shsa5563/Ring-WearTech/Project_Updates/low_power_project_update_7.pdf

## LOW POWER EMBEDDED DESIGN PROJECT UPDATE #7

Team Name: WearTech

Team Mates:

Sanjana Kalyanappagol | Shekhar Satyanarayana
saka2821@colorado.edu | shsa5563@colorado.edu

## Executive Summary:

Part Selection
Battery | GMB401215-45mAh
PMU IC | LT1965
Processor | EFR32BG13– f1024
Inductive Charging IC | BQ5103B
Battery Charger IC | BQ24040
Sensor | BMA280

As discussed, our project requires 2 Blue Gecko dev kits to act as devices in the mesh network.

On Schedule: Yes

Accomplishments:
- We have completed 100% of the schematics.
- Half way through the Layouts.
- Got the schematics reviewed
- Worked on the ESD diode

Next week:
- get second review on schematics
- Complete the Layouts
- Start Firmware Development
- Test Inductive charging
