shsa5563/Ring-WearTech/Final Report/gantchart_final.xlsx

 |  |  |  |  |  |  |  |  |  |  |  |  |  |  |  |  |  |  |  |  |  |  |  |  |  |  |  |  |  |  |  |  |  |  |  |  |  |  |  |  |  |  |  |  |  |  |  |  |  |  |  |  |  |  |  | PCB released to fab
Project Planner
 |  |  |  |  |  |  |  | Period Highlight: |  |  |  |  | 15 |  |  |  | Plan |  |  | Actual |  |  |  | % Complete |  |  |  |  | Actual (beyond plan) |  |  |  |  |  |  |  | % Complete (beyond plan)
 |  | PLAN | PLAN | ACTUAL | ACTUAL | PERCENT |  | August 28th |  |  |  | September 1st |  |  |  |  |  |  |  |  |  |  |  |  |  |  |  |  |  |  |  |  |  |  |  |  |  |  |  |  |  | October 1st
ACTIVITY |  | START | DURATION | START | DURATION | COMPLETE |  | PERIODS
 | Lead |  |  |  |  |  | Comments | 1 | 2 | 3 | 4 | 5 | 6 | 7 | 8 | 9 | 10 | 11 | 12 | 13 | 14 | 15 | 16 | 17 | 18 | 19 | 20 | 21 | 22 | 23 | 24 | 25 | 26 | 27 | 28 | 29 | 30 | 31 | 32 | 33 | 34 | 35 | 36 | 37 | 38 | 39 | 40 | 41 | 42 | 43 | 44 | 45 | 46 | 47 | 48 | 49 | 50 | 51
Search Project Idea | Sanjana & Shekhar | 1 | 7 | 6 | 3 | 100%
Project proposal | Sanjana & Shekhar | 7 | 2 | 8 | 2 | 100%
Search for Part Kits | Sanjana & Shekhar | 11 | 3 | 11 | 3 | 100%
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
