shsa5563/Ring-WearTech/Altium_Schematics_Layout/WearTechPCB/MajorICandDescription.xlsx

Project | Description
Ring-WearTech | A wearable device which recognises and acts on the alphabets/commands/gestures. The accelerometer helps in acquiring the information, which is relyed in realtime to the mobile Device through BLE. The intelligence to decode the information recevied and map to the appropriate defined gestures/commands is accomplished by the Mobile Device.
Major Ics | Description
BQ51013B | Used for Inductive charging from the Inductive coil and produces a current of 1.254A to 1.2A and voltage of 4.3V
BQ24040 | Used for LiPo battery Charging, takes the output from BQ51013B. It has an output Current of 1.2 to 1A and voltage at 4.3V
BMA280 | Accelerometer sensor IC, used to sense the accelerometer readings and double tap
EFR32BG | BLE/Bluetooth Mesh capable IC for accessing the BMA280 sensor and relying the information gained through BLE to the Mobile Device
LT1965 | And LDO for regulating the voltage to 2.5V
