shsa5563/Ring-WearTech/Project_Updates/PMU_Capacitance_Simulation_Assignment/LT1965_MultipleSink.asc

C1: cap; 10µ; Rser=5m
C2: cap; 10µ; Rser=5m
C4: cap; 0.3µ
I1: current; PULSE(0 2.487mA 0 1us 1us 5ms 133ms 4)
I2: current; PULSE(0 4.988mA 10ms 1us 1us 10ms 133ms 4)
I3: current; PULSE(0 4.988mA 23ms 1us 1us 40ms 133ms 4)
I4: current; PULSE(0 10.693mA 63ms 1us 1us 70ms 133ms 4)
R1: RES; 4.53K; tol=1 pwr=0.1
R2: res; 4.12K
R3: res; 18.79K
U1: LT1965
V1: VOLTAGE; 3.7; Rser=700m
Named nets: 0, OUT, IN
.tran 800ms startup
Note:
  If the simulation model is not found please update with the "Sync Release" command from the "Tools" menu.
  It remains the customer's responsibility to verify proper and reliable operation in the actual application.
  Component substitution and printed circuit board layout may significantly affect circuit performance or reliability.
  Contact your local sales representative for assistance. This circuit is distributed to customers only for use with LTC parts.
  Copyright © 2008 Linear Technology Inc. All rights reserved.
LT1965- 1.1A, Low Noise Low Dropout Linear Regulator
Input: 3.3V       Output: 2.5V@1.1A
