shsa5563/Ring-WearTech/Firmware/soc-smartPhone_NoBuff/inc/efr32bg13p532f512gm32.h

/**************************************************************************//**
 * @file efr32bg13p532f512gm32.h
 * @brief CMSIS Cortex-M Peripheral Access Layer Header File
 *        for EFR32BG13P532F512GM32
 * @version 5.3.2
 ******************************************************************************
 * # License
 * <b>Copyright 2017 Silicon Laboratories, Inc. http://www.silabs.com</b>
 ******************************************************************************
 *
 * Permission is granted to anyone to use this software for any purpose,
 * including commercial applications, and to alter it and redistribute it
 * freely, subject to the following restrictions:
 *
 * 1. The origin of this software must not be misrepresented; you must not
 *    claim that you wrote the original software.@n
 * 2. Altered source versions must be plainly marked as such, and must not be
 *    misrepresented as being the original software.@n
 * 3. This notice may not be removed or altered from any source distribution.
 *
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
 * Silicon Laboratories, Inc. will not be liable for any consequential,
 * incidental, or special damages, or any other relief, or for any claim by
 * any third party, arising from your use of this Software.
 *
 *****************************************************************************/

#if defined(__ICCARM__)
#pragma system_include       /* Treat file as system include file. */
#elif defined(__ARMCC_VERSION) && (__ARMCC_VERSION >= 6010050)
#pragma clang system_header  /* Treat file as system include file. */
#endif

#ifndef EFR32BG13P532F512GM32_H
#define EFR32BG13P532F512GM32_H

#ifdef __cplusplus
extern "C" {
#endif

/**************************************************************************//**
 * @addtogroup Parts
 * @{
 *****************************************************************************/

/**************************************************************************//**
 * @defgroup EFR32BG13P532F512GM32 EFR32BG13P532F512GM32
 * @{
 *****************************************************************************/

/** Interrupt Number Definition */
typedef enum IRQn{
/******  Cortex-M4 Processor Exceptions Numbers ********************************************/
  NonMaskableInt_IRQn   = -14,              /*!< 2  Cortex-M4 Non Maskable Interrupt      */
  HardFault_IRQn        = -13,              /*!< 3  Cortex-M4 Hard Fault Interrupt        */
  MemoryManagement_IRQn = -12,              /*!< 4  Cortex-M4 Memory Management Interrupt */
  BusFault_IRQn         = -11,              /*!< 5  Cortex-M4 Bus Fault Interrupt         */
  UsageFault_IRQn       = -10,              /*!< 6  Cortex-M4 Usage Fault Interrupt       */
  SVCall_IRQn           = -5,               /*!< 11 Cortex-M4 SV Call Interrupt           */
  DebugMonitor_IRQn     = -4,               /*!< 12 Cortex-M4 Debug Monitor Interrupt     */
  PendSV_IRQn           = -2,               /*!< 14 Cortex-M4 Pend SV Interrupt           */
  SysTick_IRQn          = -1,               /*!< 15 Cortex-M4 System Tick Interrupt       */

/******  EFR32BG13P Peripheral Interrupt Numbers ********************************************/

  EMU_IRQn              = 0,  /*!< 16+0 EFR32 EMU Interrupt */
  WDOG0_IRQn            = 2,  /*!< 16+2 EFR32 WDOG0 Interrupt */
  WDOG1_IRQn            = 3,  /*!< 16+3 EFR32 WDOG1 Interrupt */
  LDMA_IRQn             = 9,  /*!< 16+9 EFR32 LDMA Interrupt */
  GPIO_EVEN_IRQn        = 10, /*!< 16+10 EFR32 GPIO_EVEN Interrupt */
  TIMER0_IRQn           = 11, /*!< 16+11 EFR32 TIMER0 Interrupt */
  USART0_RX_IRQn        = 12, /*!< 16+12 EFR32 USART0_RX Interrupt */
  USART0_TX_IRQn        = 13, /*!< 16+13 EFR32 USART0_TX Interrupt */
  ACMP0_IRQn            = 14, /*!< 16+14 EFR32 ACMP0 Interrupt */
  ADC0_IRQn             = 15, /*!< 16+15 EFR32 ADC0 Interrupt */
  IDAC0_IRQn            = 16, /*!< 16+16 EFR32 IDAC0 Interrupt */
  I2C0_IRQn             = 17, /*!< 16+17 EFR32 I2C0 Interrupt */
  GPIO_ODD_IRQn         = 18, /*!< 16+18 EFR32 GPIO_ODD Interrupt */
  TIMER1_IRQn           = 19, /*!< 16+19 EFR32 TIMER1 Interrupt */
  USART1_RX_IRQn        = 20, /*!< 16+20 EFR32 USART1_RX Interrupt */
  USART1_TX_IRQn        = 21, /*!< 16+21 EFR32 USART1_TX Interrupt */
  LEUART0_IRQn          = 22, /*!< 16+22 EFR32 LEUART0 Interrupt */
  PCNT0_IRQn            = 23, /*!< 16+23 EFR32 PCNT0 Interrupt */
  CMU_IRQn              = 24, /*!< 16+24 EFR32 CMU Interrupt */
  MSC_IRQn              = 25, /*!< 16+25 EFR32 MSC Interrupt */
  CRYPTO0_IRQn          = 26, /*!< 16+26 EFR32 CRYPTO0 Interrupt */
  LETIMER0_IRQn         = 27, /*!< 16+27 EFR32 LETIMER0 Interrupt */
  RTCC_IRQn             = 31, /*!< 16+31 EFR32 RTCC Interrupt */
  CRYOTIMER_IRQn        = 33, /*!< 16+33 EFR32 CRYOTIMER Interrupt */
  FPUEH_IRQn            = 35, /*!< 16+35 EFR32 FPUEH Interrupt */
  SMU_IRQn              = 36, /*!< 16+36 EFR32 SMU Interrupt */
  WTIMER0_IRQn          = 37, /*!< 16+37 EFR32 WTIMER0 Interrupt */
  USART2_RX_IRQn        = 38, /*!< 16+38 EFR32 USART2_RX Interrupt */
  USART2_TX_IRQn        = 39, /*!< 16+39 EFR32 USART2_TX Interrupt */
  I2C1_IRQn             = 40, /*!< 16+40 EFR32 I2C1 Interrupt */
  VDAC0_IRQn            = 41, /*!< 16+41 EFR32 VDAC0 Interrupt */
  CSEN_IRQn             = 42, /*!< 16+42 EFR32 CSEN Interrupt */
  LESENSE_IRQn          = 43, /*!< 16+43 EFR32 LESENSE Interrupt */
  CRYPTO1_IRQn          = 44, /*!< 16+44 EFR32 CRYPTO1 Interrupt */
  TRNG0_IRQn            = 45, /*!< 16+45 EFR32 TRNG0 Interrupt */
} IRQn_Type;

#define CRYPTO_IRQn               CRYPTO0_IRQn /*!< Alias for CRYPTO0_IRQn */

/**************************************************************************//**
 * @defgroup EFR32BG13P532F512GM32_Core Core
 * @{
 * @brief Processor and Core Peripheral Section
 *****************************************************************************/
#define __MPU_PRESENT             1 /**< Presence of MPU  */
#define __FPU_PRESENT             1 /**< Presence of FPU  */
#define __VTOR_PRESENT            1 /**< Presence of VTOR register in SCB */
#define __NVIC_PRIO_BITS          3 /**< NVIC interrupt priority bits */
#define __Vendor_SysTickConfig    0 /**< Is 1 if different SysTick counter is used */

/** @} End of group EFR32BG13P532F512GM32_Core */

/**************************************************************************//**
* @defgroup EFR32BG13P532F512GM32_Part Part
* @{
******************************************************************************/

/** Part family */
#define _EFR32_BLUE_FAMILY                      1                               /**< BLUE Gecko RF SoC Family  */
#define _EFR_DEVICE                                                             /**< Silicon Labs EFR-type RF SoC */
#define _SILICON_LABS_32B_SERIES_1                                              /**< Silicon Labs series number */
#define _SILICON_LABS_32B_SERIES                1                               /**< Silicon Labs series number */
#define _SILICON_LABS_32B_SERIES_1_CONFIG_3                                     /**< Series 1, Configuration 3 */
#define _SILICON_LABS_32B_SERIES_1_CONFIG       3                               /**< Series 1, Configuration 3 */
#define _SILICON_LABS_GECKO_INTERNAL_SDID       89                              /**< Silicon Labs internal use only, may change any time */
#define _SILICON_LABS_GECKO_INTERNAL_SDID_89                                    /**< Silicon Labs internal use only, may change any time */
#define _SILICON_LABS_EFR32_RADIO_SUBGHZ        1                               /**< Radio supports Sub-GHz */
#define _SILICON_LABS_EFR32_RADIO_2G4HZ         2                               /**< Radio supports 2.4 GHz */
#define _SILICON_LABS_EFR32_RADIO_DUALBAND      3                               /**< Radio supports dual band */
#define _SILICON_LABS_EFR32_RADIO_TYPE          _SILICON_LABS_EFR32_RADIO_2G4HZ /**< Radio type */
#define _SILICON_LABS_32B_PLATFORM_2                                            /**< @deprecated Silicon Labs platform name */
#define _SILICON_LABS_32B_PLATFORM              2                               /**< @deprecated Silicon Labs platform name */
#define _SILICON_LABS_32B_PLATFORM_2_GEN_3                                      /**< @deprecated Platform 2, generation 3 */
#define _SILICON_LABS_32B_PLATFORM_2_GEN        3                               /**< @deprecated Platform 2, generation 3 */

/* If part number is not defined as compiler option, define it */
#if !defined(EFR32BG13P532F512GM32)
#define EFR32BG13P532F512GM32    1 /**< BLUE Gecko Part */
#endif

/** Configure part number */
#define PART_NUMBER                "EFR32BG13P532F512GM32" /**< Part Number */

/** Memory Base addresses and limits */
#define RAM0_CODE_MEM_BASE         ((uint32_t) 0x10000000UL) /**< RAM0_CODE base address  */
#define RAM0_CODE_MEM_SIZE         ((uint32_t) 0x8000UL)     /**< RAM0_CODE available address space  */
#define RAM0_CODE_MEM_END          ((uint32_t) 0x10007FFFUL) /**< RAM0_CODE end address  */
#define RAM0_CODE_MEM_BITS         ((uint32_t) 0x0000000FUL) /**< RAM0_CODE used bits  */
#define RAM2_MEM_BASE              ((uint32_t) 0x20010000UL) /**< RAM2 base address  */
#define RAM2_MEM_SIZE              ((uint32_t) 0x800UL)      /**< RAM2 available address space  */
#define RAM2_MEM_END               ((uint32_t) 0x200107FFUL) /**< RAM2 end address  */
#define RAM2_MEM_BITS              ((uint32_t) 0x0000000BUL) /**< RAM2 used bits  */
#define RAM1_MEM_BASE              ((uint32_t) 0x20008000UL) /**< RAM1 base address  */
#define RAM1_MEM_SIZE              ((uint32_t) 0x8000UL)     /**< RAM1 available address space  */
#define RAM1_MEM_END               ((uint32_t) 0x2000FFFFUL) /**< RAM1 end address  */
#define RAM1_MEM_BITS              ((uint32_t) 0x0000000FUL) /**< RAM1 used bits  */
#define CRYPTO1_BITCLR_MEM_BASE    ((uint32_t) 0x440F0400UL) /**< CRYPTO1_BITCLR base address  */
#define CRYPTO1_BITCLR_MEM_SIZE    ((uint32_t) 0x400UL)      /**< CRYPTO1_BITCLR available address space  */
#define CRYPTO1_BITCLR_MEM_END     ((uint32_t) 0x440F07FFUL) /**< CRYPTO1_BITCLR end address  */
#define CRYPTO1_BITCLR_MEM_BITS    ((uint32_t) 0x0000000AUL) /**< CRYPTO1_BITCLR used bits  */
#define PER_MEM_BASE               ((uint32_t) 0x40000000UL) /**< PER base address  */
#define PER_MEM_SIZE               ((uint32_t) 0xF0000UL)    /**< PER available address space  */
#define PER_MEM_END                ((uint32_t) 0x400EFFFFUL) /**< PER end address  */
#define PER_MEM_BITS               ((uint32_t) 0x00000014UL) /**< PER used bits  */
#define RAM1_CODE_MEM_BASE         ((uint32_t) 0x10008000UL) /**< RAM1_CODE base address  */
#define RAM1_CODE_MEM_SIZE         ((uint32_t) 0x8000UL)     /**< RAM1_CODE available address space  */
#define RAM1_CODE_MEM_END          ((uint32_t) 0x1000FFFFUL) /**< RAM1_CODE end address  */
#define RAM1_CODE_MEM_BITS         ((uint32_t) 0x0000000FUL) /**< RAM1_CODE used bits  */
#define CRYPTO1_MEM_BASE           ((uint32_t) 0x400F0400UL) /**< CRYPTO1 base address  */
#define CRYPTO1_MEM_SIZE           ((uint32_t) 0x400UL)      /**< CRYPTO1 available address space  */
#define CRYPTO1_MEM_END            ((uint32_t) 0x400F07FFUL) /**< CRYPTO1 end address  */
#define CRYPTO1_MEM_BITS           ((uint32_t) 0x0000000AUL) /**< CRYPTO1 used bits  */
#define FLASH_MEM_BASE             ((uint32_t) 0x00000000UL) /**< FLASH base address  */
#define FLASH_MEM_SIZE             ((uint32_t) 0x10000000UL) /**< FLASH available address space  */
#define FLASH_MEM_END              ((uint32_t) 0x0FFFFFFFUL) /**< FLASH end address  */
#define FLASH_MEM_BITS             ((uint32_t) 0x0000001CUL) /**< FLASH used bits  */
#define CRYPTO0_MEM_BASE           ((uint32_t) 0x400F0000UL) /**< CRYPTO0 base address  */
#define CRYPTO0_MEM_SIZE           ((uint32_t) 0x400UL)      /**< CRYPTO0 available address space  */
#define CRYPTO0_MEM_END            ((uint32_t) 0x400F03FFUL) /**< CRYPTO0 end address  */
#define CRYPTO0_MEM_BITS           ((uint32_t) 0x0000000AUL) /**< CRYPTO0 used bits  */
#define CRYPTO_MEM_BASE            CRYPTO0_MEM_BASE          /**< Alias for CRYPTO0_MEM_BASE */
#define CRYPTO_MEM_SIZE            CRYPTO0_MEM_SIZE          /**< Alias for CRYPTO0_MEM_SIZE */
#define CRYPTO_MEM_END             CRYPTO0_MEM_END           /**< Alias for CRYPTO0_MEM_END  */
#define CRYPTO_MEM_BITS            CRYPTO0_MEM_BITS          /**< Alias for CRYPTO0_MEM_BITS */
#define PER_BITCLR_MEM_BASE        ((uint32_t) 0x44000000UL) /**< PER_BITCLR base address  */
#define PER_BITCLR_MEM_SIZE        ((uint32_t) 0xF0000UL)    /**< PER_BITCLR available address space  */
#define PER_BITCLR_MEM_END         ((uint32_t) 0x440EFFFFUL) /**< PER_BITCLR end address  */
#define PER_BITCLR_MEM_BITS        ((uint32_t) 0x00000014UL) /**< PER_BITCLR used bits  */
#define CRYPTO0_BITSET_MEM_BASE    ((uint32_t) 0x460F0000UL) /**< CRYPTO0_BITSET base address  */
#define CRYPTO0_BITSET_MEM_SIZE    ((uint32_t) 0x400UL)      /**< CRYPTO0_BITSET available address space  */
#define CRYPTO0_BITSET_MEM_END     ((uint32_t) 0x460F03FFUL) /**< CRYPTO0_BITSET end address  */
#define CRYPTO0_BITSET_MEM_BITS    ((uint32_t) 0x0000000AUL) /**< CRYPTO0_BITSET used bits  */
#define CRYPTO_BITSET_MEM_BASE     CRYPTO0_BITSET_MEM_BASE   /**< Alias for CRYPTO0_BITSET_MEM_BASE */
#define CRYPTO_BITSET_MEM_SIZE     CRYPTO0_BITSET_MEM_SIZE   /**< Alias for CRYPTO0_BITSET_MEM_SIZE */
#define CRYPTO_BITSET_MEM_END      CRYPTO0_BITSET_MEM_END    /**< Alias for CRYPTO0_BITSET_MEM_END  */
#define CRYPTO_BITSET_MEM_BITS     CRYPTO0_BITSET_MEM_BITS   /**< Alias for CRYPTO0_BITSET_MEM_BITS */
#define CRYPTO0_BITCLR_MEM_BASE    ((uint32_t) 0x440F0000UL) /**< CRYPTO0_BITCLR base address  */
#define CRYPTO0_BITCLR_MEM_SIZE    ((uint32_t) 0x400UL)      /**< CRYPTO0_BITCLR available address space  */
#define CRYPTO0_BITCLR_MEM_END     ((uint32_t) 0x440F03FFUL) /**< CRYPTO0_BITCLR end address  */
#define CRYPTO0_BITCLR_MEM_BITS    ((uint32_t) 0x0000000AUL) /**< CRYPTO0_BITCLR used bits  */
#define CRYPTO_BITCLR_MEM_BASE     CRYPTO0_BITCLR_MEM_BASE   /**< Alias for CRYPTO0_BITCLR_MEM_BASE */
#define CRYPTO_BITCLR_MEM_SIZE     CRYPTO0_BITCLR_MEM_SIZE   /**< Alias for CRYPTO0_BITCLR_MEM_SIZE */
#define CRYPTO_BITCLR_MEM_END      CRYPTO0_BITCLR_MEM_END    /**< Alias for CRYPTO0_BITCLR_MEM_END  */
#define CRYPTO_BITCLR_MEM_BITS     CRYPTO0_BITCLR_MEM_BITS   /**< Alias for CRYPTO0_BITCLR_MEM_BITS */
#define PER_BITSET_MEM_BASE        ((uint32_t) 0x46000000UL) /**< PER_BITSET base address  */
#define PER_BITSET_MEM_SIZE        ((uint32_t) 0xF0000UL)    /**< PER_BITSET available address space  */
#define PER_BITSET_MEM_END         ((uint32_t) 0x460EFFFFUL) /**< PER_BITSET end address  */
#define PER_BITSET_MEM_BITS        ((uint32_t) 0x00000014UL) /**< PER_BITSET used bits  */
#define CRYPTO1_BITSET_MEM_BASE    ((uint32_t) 0x460F0400UL) /**< CRYPTO1_BITSET base address  */
#define CRYPTO1_BITSET_MEM_SIZE    ((uint32_t) 0x400UL)      /**< CRYPTO1_BITSET available address space  */
#define CRYPTO1_BITSET_MEM_END     ((uint32_t) 0x460F07FFUL) /**< CRYPTO1_BITSET end address  */
#define CRYPTO1_BITSET_MEM_BITS    ((uint32_t) 0x0000000AUL) /**< CRYPTO1_BITSET used bits  */
#define RAM2_CODE_MEM_BASE         ((uint32_t) 0x10010000UL) /**< RAM2_CODE base address  */
#define RAM2_CODE_MEM_SIZE         ((uint32_t) 0x800UL)      /**< RAM2_CODE available address space  */
#define RAM2_CODE_MEM_END          ((uint32_t) 0x100107FFUL) /**< RAM2_CODE end address  */
#define RAM2_CODE_MEM_BITS         ((uint32_t) 0x0000000BUL) /**< RAM2_CODE used bits  */
#define RAM_MEM_BASE               ((uint32_t) 0x20000000UL) /**< RAM base address  */
#define RAM_MEM_SIZE               ((uint32_t) 0x8000UL)     /**< RAM available address space  */
#define RAM_MEM_END                ((uint32_t) 0x20007FFFUL) /**< RAM end address  */
#define RAM_MEM_BITS               ((uint32_t) 0x0000000FUL) /**< RAM used bits  */

/** Bit banding area */
#define BITBAND_PER_BASE           ((uint32_t) 0x42000000UL) /**< Peripheral Address Space bit-band area */
#define BITBAND_RAM_BASE           ((uint32_t) 0x22000000UL) /**< SRAM Address Space bit-band area */

/** Flash and SRAM limits for EFR32BG13P532F512GM32 */
#define FLASH_BASE                 (0x00000000UL) /**< Flash Base Address */
#define FLASH_SIZE                 (0x00080000UL) /**< Available Flash Memory */
#define FLASH_PAGE_SIZE            2048U          /**< Flash Memory page size */
#define SRAM_BASE                  (0x20000000UL) /**< SRAM Base Address */
#define SRAM_SIZE                  (0x00010000UL) /**< Available SRAM Memory */
#define __CM4_REV                  0x001          /**< Cortex-M4 Core revision r0p1 */
#define PRS_CHAN_COUNT             12             /**< Number of PRS channels */
#define DMA_CHAN_COUNT             8              /**< Number of DMA channels */
#define EXT_IRQ_COUNT              47             /**< Number of External (NVIC) interrupts */

/** AF channels connect the different on-chip peripherals with the af-mux */
#define AFCHAN_MAX                 118
/** AF channel maximum location number */
#define AFCHANLOC_MAX              32
/** Analog AF channels */
#define AFACHAN_MAX                118

/* Part number capabilities */

#define CRYPTO_PRESENT          /**< CRYPTO is available in this part */
#define CRYPTO_COUNT          2 /**< 2 CRYPTOs available  */
#define TIMER_PRESENT           /**< TIMER is available in this part */
#define TIMER_COUNT           2 /**< 2 TIMERs available  */
#define WTIMER_PRESENT          /**< WTIMER is available in this part */
#define WTIMER_COUNT          1 /**< 1 WTIMERs available  */
#define USART_PRESENT           /**< USART is available in this part */
#define USART_COUNT           3 /**< 3 USARTs available  */
#define LEUART_PRESENT          /**< LEUART is available in this part */
#define LEUART_COUNT          1 /**< 1 LEUARTs available  */
#define LETIMER_PRESENT         /**< LETIMER is available in this part */
#define LETIMER_COUNT         1 /**< 1 LETIMERs available  */
#define PCNT_PRESENT            /**< PCNT is available in this part */
#define PCNT_COUNT            1 /**< 1 PCNTs available  */
#define I2C_PRESENT             /**< I2C is available in this part */
#define I2C_COUNT             2 /**< 2 I2Cs available  */
#define ADC_PRESENT             /**< ADC is available in this part */
#define ADC_COUNT             1 /**< 1 ADCs available  */
#define ACMP_PRESENT            /**< ACMP is available in this part */
#define ACMP_COUNT            2 /**< 2 ACMPs available  */
#define VDAC_PRESENT            /**< VDAC is available in this part */
#define VDAC_COUNT            1 /**< 1 VDACs available  */
#define WDOG_PRESENT            /**< WDOG is available in this part */
#define WDOG_COUNT            2 /**< 2 WDOGs available  */
#define IDAC_PRESENT            /**< IDAC is available in this part */
#define IDAC_COUNT            1 /**< 1 IDACs available  */
#define TRNG_PRESENT            /**< TRNG is available in this part */
#define TRNG_COUNT            1 /**< 1 TRNGs available  */
#define MSC_PRESENT             /**< MSC is available in this part */
#define MSC_COUNT             1 /**< 1 MSC available */
#define EMU_PRESENT             /**< EMU is available in this part */
#define EMU_COUNT             1 /**< 1 EMU available */
#define RMU_PRESENT             /**< RMU is available in this part */
#define RMU_COUNT             1 /**< 1 RMU available */
#define CMU_PRESENT             /**< CMU is available in this part */
#define CMU_COUNT             1 /**< 1 CMU available */
#define GPIO_PRESENT            /**< GPIO is available in this part */
#define GPIO_COUNT            1 /**< 1 GPIO available */
#define PRS_PRESENT             /**< PRS is available in this part */
#define PRS_COUNT             1 /**< 1 PRS available */
#define LDMA_PRESENT            /**< LDMA is available in this part */
#define LDMA_COUNT            1 /**< 1 LDMA available */
#define FPUEH_PRESENT           /**< FPUEH is available in this part */
#define FPUEH_COUNT           1 /**< 1 FPUEH available */
#define GPCRC_PRESENT           /**< GPCRC is available in this part */
#define GPCRC_COUNT           1 /**< 1 GPCRC available */
#define CRYOTIMER_PRESENT       /**< CRYOTIMER is available in this part */
#define CRYOTIMER_COUNT       1 /**< 1 CRYOTIMER available */
#define CSEN_PRESENT            /**< CSEN is available in this part */
#define CSEN_COUNT            1 /**< 1 CSEN available */
#define LESENSE_PRESENT         /**< LESENSE is available in this part */
#define LESENSE_COUNT         1 /**< 1 LESENSE available */
#define RTCC_PRESENT            /**< RTCC is available in this part */
#define RTCC_COUNT            1 /**< 1 RTCC available */
#define ETM_PRESENT             /**< ETM is available in this part */
#define ETM_COUNT             1 /**< 1 ETM available */
#define BOOTLOADER_PRESENT      /**< BOOTLOADER is available in this part */
#define BOOTLOADER_COUNT      1 /**< 1 BOOTLOADER available */
#define SMU_PRESENT             /**< SMU is available in this part */
#define SMU_COUNT             1 /**< 1 SMU available */
#define DCDC_PRESENT            /**< DCDC is available in this part */
#define DCDC_COUNT            1 /**< 1 DCDC available */

#include "core_cm4.h"           /* Cortex-M4 processor and core peripherals */
#include "system_efr32bg13p.h"  /* System Header File */

/** @} End of group EFR32BG13P532F512GM32_Part */

/**************************************************************************//**
 * @defgroup EFR32BG13P532F512GM32_Peripheral_TypeDefs Peripheral TypeDefs
 * @{
 * @brief Device Specific Peripheral Register Structures
 *****************************************************************************/

#include "efr32bg13p_msc.h"
#include "efr32bg13p_emu.h"
#include "efr32bg13p_rmu.h"
#include "efr32bg13p_cmu.h"
#include "efr32bg13p_crypto.h"
#include "efr32bg13p_gpio_p.h"
#include "efr32bg13p_gpio.h"
#include "efr32bg13p_prs_ch.h"
#include "efr32bg13p_prs.h"
#include "efr32bg13p_ldma_ch.h"
#include "efr32bg13p_ldma.h"
#include "efr32bg13p_fpueh.h"
#include "efr32bg13p_gpcrc.h"
#include "efr32bg13p_timer_cc.h"
#include "efr32bg13p_timer.h"
#include "efr32bg13p_usart.h"
#include "efr32bg13p_leuart.h"
#include "efr32bg13p_letimer.h"
#include "efr32bg13p_cryotimer.h"
#include "efr32bg13p_pcnt.h"
#include "efr32bg13p_i2c.h"
#include "efr32bg13p_adc.h"
#include "efr32bg13p_acmp.h"
#include "efr32bg13p_vdac_opa.h"
#include "efr32bg13p_vdac.h"
#include "efr32bg13p_csen.h"
#include "efr32bg13p_lesense_st.h"
#include "efr32bg13p_lesense_buf.h"
#include "efr32bg13p_lesense_ch.h"
#include "efr32bg13p_lesense.h"
#include "efr32bg13p_rtcc_cc.h"
#include "efr32bg13p_rtcc_ret.h"
#include "efr32bg13p_rtcc.h"
#include "efr32bg13p_wdog_pch.h"
#include "efr32bg13p_wdog.h"
#include "efr32bg13p_etm.h"
#include "efr32bg13p_idac.h"
#include "efr32bg13p_smu.h"
#include "efr32bg13p_trng.h"
#include "efr32bg13p_dma_descriptor.h"
#include "efr32bg13p_devinfo.h"
#include "efr32bg13p_romtable.h"

/** @} End of group EFR32BG13P532F512GM32_Peripheral_TypeDefs  */

/**************************************************************************//**
 * @defgroup EFR32BG13P532F512GM32_Peripheral_Base Peripheral Memory Map
 * @{
 *****************************************************************************/

#define MSC_BASE          (0x400E0000UL) /**< MSC base address  */
#define EMU_BASE          (0x400E3000UL) /**< EMU base address  */
#define RMU_BASE          (0x400E5000UL) /**< RMU base address  */
#define CMU_BASE          (0x400E4000UL) /**< CMU base address  */
#define CRYPTO0_BASE      (0x400F0000UL) /**< CRYPTO0 base address  */
#define CRYPTO_BASE       CRYPTO0_BASE   /**< Alias for CRYPTO0 base address */
#define CRYPTO1_BASE      (0x400F0400UL) /**< CRYPTO1 base address  */
#define GPIO_BASE         (0x4000A000UL) /**< GPIO base address  */
#define PRS_BASE          (0x400E6000UL) /**< PRS base address  */
#define LDMA_BASE         (0x400E2000UL) /**< LDMA base address  */
#define FPUEH_BASE        (0x400E1000UL) /**< FPUEH base address  */
#define GPCRC_BASE        (0x4001C000UL) /**< GPCRC base address  */
#define TIMER0_BASE       (0x40018000UL) /**< TIMER0 base address  */
#define TIMER1_BASE       (0x40018400UL) /**< TIMER1 base address  */
#define WTIMER0_BASE      (0x4001A000UL) /**< WTIMER0 base address  */
#define USART0_BASE       (0x40010000UL) /**< USART0 base address  */
#define USART1_BASE       (0x40010400UL) /**< USART1 base address  */
#define USART2_BASE       (0x40010800UL) /**< USART2 base address  */
#define LEUART0_BASE      (0x4004A000UL) /**< LEUART0 base address  */
#define LETIMER0_BASE     (0x40046000UL) /**< LETIMER0 base address  */
#define CRYOTIMER_BASE    (0x4001E000UL) /**< CRYOTIMER base address  */
#define PCNT0_BASE        (0x4004E000UL) /**< PCNT0 base address  */
#define I2C0_BASE         (0x4000C000UL) /**< I2C0 base address  */
#define I2C1_BASE         (0x4000C400UL) /**< I2C1 base address  */
#define ADC0_BASE         (0x40002000UL) /**< ADC0 base address  */
#define ACMP0_BASE        (0x40000000UL) /**< ACMP0 base address  */
#define ACMP1_BASE        (0x40000400UL) /**< ACMP1 base address  */
#define VDAC0_BASE        (0x40008000UL) /**< VDAC0 base address  */
#define CSEN_BASE         (0x4001F000UL) /**< CSEN base address  */
#define LESENSE_BASE      (0x40055000UL) /**< LESENSE base address  */
#define RTCC_BASE         (0x40042000UL) /**< RTCC base address  */
#define WDOG0_BASE        (0x40052000UL) /**< WDOG0 base address  */
#define WDOG1_BASE        (0x40052400UL) /**< WDOG1 base address  */
#define ETM_BASE          (0xE0041000UL) /**< ETM base address  */
#define IDAC0_BASE        (0x40006000UL) /**< IDAC0 base address  */
#define SMU_BASE          (0x40022000UL) /**< SMU base address  */
#define TRNG0_BASE        (0x4001D000UL) /**< TRNG0 base address  */
#define DEVINFO_BASE      (0x0FE081B0UL) /**< DEVINFO base address */
#define ROMTABLE_BASE     (0xE00FFFD0UL) /**< ROMTABLE base address */
#define LOCKBITS_BASE     (0x0FE04000UL) /**< Lock-bits page base address */
#define USERDATA_BASE     (0x0FE00000UL) /**< User data page base address */

/** @} End of group EFR32BG13P532F512GM32_Peripheral_Base */

/**************************************************************************//**
 * @defgroup EFR32BG13P532F512GM32_Peripheral_Declaration Peripheral Declarations
 * @{
 *****************************************************************************/

#define MSC          ((MSC_TypeDef *) MSC_BASE)             /**< MSC base pointer */
#define EMU          ((EMU_TypeDef *) EMU_BASE)             /**< EMU base pointer */
#define RMU          ((RMU_TypeDef *) RMU_BASE)             /**< RMU base pointer */
#define CMU          ((CMU_TypeDef *) CMU_BASE)             /**< CMU base pointer */
#define CRYPTO0      ((CRYPTO_TypeDef *) CRYPTO0_BASE)      /**< CRYPTO0 base pointer */
#define CRYPTO       CRYPTO0                                /**< Alias for CRYPTO0 base pointer */
#define CRYPTO1      ((CRYPTO_TypeDef *) CRYPTO1_BASE)      /**< CRYPTO1 base pointer */
#define GPIO         ((GPIO_TypeDef *) GPIO_BASE)           /**< GPIO base pointer */
#define PRS          ((PRS_TypeDef *) PRS_BASE)             /**< PRS base pointer */
#define LDMA         ((LDMA_TypeDef *) LDMA_BASE)           /**< LDMA base pointer */
#define FPUEH        ((FPUEH_TypeDef *) FPUEH_BASE)         /**< FPUEH base pointer */
#define GPCRC        ((GPCRC_TypeDef *) GPCRC_BASE)         /**< GPCRC base pointer */
#define TIMER0       ((TIMER_TypeDef *) TIMER0_BASE)        /**< TIMER0 base pointer */
#define TIMER1       ((TIMER_TypeDef *) TIMER1_BASE)        /**< TIMER1 base pointer */
#define WTIMER0      ((TIMER_TypeDef *) WTIMER0_BASE)       /**< WTIMER0 base pointer */
#define USART0       ((USART_TypeDef *) USART0_BASE)        /**< USART0 base pointer */
#define USART1       ((USART_TypeDef *) USART1_BASE)        /**< USART1 base pointer */
#define USART2       ((USART_TypeDef *) USART2_BASE)        /**< USART2 base pointer */
#define LEUART0      ((LEUART_TypeDef *) LEUART0_BASE)      /**< LEUART0 base pointer */
#define LETIMER0     ((LETIMER_TypeDef *) LETIMER0_BASE)    /**< LETIMER0 base pointer */
#define CRYOTIMER    ((CRYOTIMER_TypeDef *) CRYOTIMER_BASE) /**< CRYOTIMER base pointer */
#define PCNT0        ((PCNT_TypeDef *) PCNT0_BASE)          /**< PCNT0 base pointer */
#define I2C0         ((I2C_TypeDef *) I2C0_BASE)            /**< I2C0 base pointer */
#define I2C1         ((I2C_TypeDef *) I2C1_BASE)            /**< I2C1 base pointer */
#define ADC0         ((ADC_TypeDef *) ADC0_BASE)            /**< ADC0 base pointer */
#define ACMP0        ((ACMP_TypeDef *) ACMP0_BASE)          /**< ACMP0 base pointer */
#define ACMP1        ((ACMP_TypeDef *) ACMP1_BASE)          /**< ACMP1 base pointer */
#define VDAC0        ((VDAC_TypeDef *) VDAC0_BASE)          /**< VDAC0 base pointer */
#define CSEN         ((CSEN_TypeDef *) CSEN_BASE)           /**< CSEN base pointer */
#define LESENSE      ((LESENSE_TypeDef *) LESENSE_BASE)     /**< LESENSE base pointer */
#define RTCC         ((RTCC_TypeDef *) RTCC_BASE)           /**< RTCC base pointer */
#define WDOG0        ((WDOG_TypeDef *) WDOG0_BASE)          /**< WDOG0 base pointer */
#define WDOG1        ((WDOG_TypeDef *) WDOG1_BASE)          /**< WDOG1 base pointer */
#define ETM          ((ETM_TypeDef *) ETM_BASE)             /**< ETM base pointer */
#define IDAC0        ((IDAC_TypeDef *) IDAC0_BASE)          /**< IDAC0 base pointer */
#define SMU          ((SMU_TypeDef *) SMU_BASE)             /**< SMU base pointer */
#define TRNG0        ((TRNG_TypeDef *) TRNG0_BASE)          /**< TRNG0 base pointer */
#define DEVINFO      ((DEVINFO_TypeDef *) DEVINFO_BASE)     /**< DEVINFO base pointer */
#define ROMTABLE     ((ROMTABLE_TypeDef *) ROMTABLE_BASE)   /**< ROMTABLE base pointer */

/** @} End of group EFR32BG13P532F512GM32_Peripheral_Declaration */

/**************************************************************************//**
 * @defgroup EFR32BG13P532F512GM32_Peripheral_Offsets Peripheral Offsets
 * @{
 *****************************************************************************/

#define CRYPTO_OFFSET     0x400 /**< Offset in bytes between CRYPTO instances */
#define TIMER_OFFSET      0x400 /**< Offset in bytes between TIMER instances */
#define WTIMER_OFFSET     0x400 /**< Offset in bytes between WTIMER instances */
#define USART_OFFSET      0x400 /**< Offset in bytes between USART instances */
#define LEUART_OFFSET     0x400 /**< Offset in bytes between LEUART instances */
#define LETIMER_OFFSET    0x400 /**< Offset in bytes between LETIMER instances */
#define PCNT_OFFSET       0x400 /**< Offset in bytes between PCNT instances */
#define I2C_OFFSET        0x400 /**< Offset in bytes between I2C instances */
#define ADC_OFFSET        0x400 /**< Offset in bytes between ADC instances */
#define ACMP_OFFSET       0x400 /**< Offset in bytes between ACMP instances */
#define VDAC_OFFSET       0x400 /**< Offset in bytes between VDAC instances */
#define WDOG_OFFSET       0x400 /**< Offset in bytes between WDOG instances */
#define IDAC_OFFSET       0x400 /**< Offset in bytes between IDAC instances */
#define TRNG_OFFSET       0x400 /**< Offset in bytes between TRNG instances */

/** @} End of group EFR32BG13P532F512GM32_Peripheral_Offsets */

/**************************************************************************//**
 * @defgroup EFR32BG13P532F512GM32_BitFields Bit Fields
 * @{
 *****************************************************************************/

#include "efr32bg13p_prs_signals.h"
#include "efr32bg13p_dmareq.h"

/**************************************************************************//**
 * @addtogroup EFR32BG13P532F512GM32_WTIMER
 * @{
 * @defgroup EFR32BG13P532F512GM32_WTIMER_BitFields  WTIMER Bit Fields
 * @{
 *****************************************************************************/

/* Bit fields for WTIMER CTRL */
#define _WTIMER_CTRL_RESETVALUE                     0x00000000UL                              /**< Default value for WTIMER_CTRL */
#define _WTIMER_CTRL_MASK                           0x3F036FFBUL                              /**< Mask for WTIMER_CTRL */
#define _WTIMER_CTRL_MODE_SHIFT                     0                                         /**< Shift value for TIMER_MODE */
#define _WTIMER_CTRL_MODE_MASK                      0x3UL                                     /**< Bit mask for TIMER_MODE */
#define _WTIMER_CTRL_MODE_DEFAULT                   0x00000000UL                              /**< Mode DEFAULT for WTIMER_CTRL */
#define _WTIMER_CTRL_MODE_UP                        0x00000000UL                              /**< Mode UP for WTIMER_CTRL */
#define _WTIMER_CTRL_MODE_DOWN                      0x00000001UL                              /**< Mode DOWN for WTIMER_CTRL */
#define _WTIMER_CTRL_MODE_UPDOWN                    0x00000002UL                              /**< Mode UPDOWN for WTIMER_CTRL */
#define _WTIMER_CTRL_MODE_QDEC                      0x00000003UL                              /**< Mode QDEC for WTIMER_CTRL */
#define WTIMER_CTRL_MODE_DEFAULT                    (_WTIMER_CTRL_MODE_DEFAULT << 0)          /**< Shifted mode DEFAULT for WTIMER_CTRL */
#define WTIMER_CTRL_MODE_UP                         (_WTIMER_CTRL_MODE_UP << 0)               /**< Shifted mode UP for WTIMER_CTRL */
#define WTIMER_CTRL_MODE_DOWN                       (_WTIMER_CTRL_MODE_DOWN << 0)             /**< Shifted mode DOWN for WTIMER_CTRL */
#define WTIMER_CTRL_MODE_UPDOWN                     (_WTIMER_CTRL_MODE_UPDOWN << 0)           /**< Shifted mode UPDOWN for WTIMER_CTRL */
#define WTIMER_CTRL_MODE_QDEC                       (_WTIMER_CTRL_MODE_QDEC << 0)             /**< Shifted mode QDEC for WTIMER_CTRL */
#define WTIMER_CTRL_SYNC                            (0x1UL << 3)                              /**< Timer Start/Stop/Reload Synchronization */
#define _WTIMER_CTRL_SYNC_SHIFT                     3                                         /**< Shift value for TIMER_SYNC */
#define _WTIMER_CTRL_SYNC_MASK                      0x8UL                                     /**< Bit mask for TIMER_SYNC */
#define _WTIMER_CTRL_SYNC_DEFAULT                   0x00000000UL                              /**< Mode DEFAULT for WTIMER_CTRL */
#define WTIMER_CTRL_SYNC_DEFAULT                    (_WTIMER_CTRL_SYNC_DEFAULT << 3)          /**< Shifted mode DEFAULT for WTIMER_CTRL */
#define WTIMER_CTRL_OSMEN                           (0x1UL << 4)                              /**< One-shot Mode Enable */
#define _WTIMER_CTRL_OSMEN_SHIFT                    4                                         /**< Shift value for TIMER_OSMEN */
#define _WTIMER_CTRL_OSMEN_MASK                     0x10UL                                    /**< Bit mask for TIMER_OSMEN */
#define _WTIMER_CTRL_OSMEN_DEFAULT                  0x00000000UL                              /**< Mode DEFAULT for WTIMER_CTRL */
#define WTIMER_CTRL_OSMEN_DEFAULT                   (_WTIMER_CTRL_OSMEN_DEFAULT << 4)         /**< Shifted mode DEFAULT for WTIMER_CTRL */
#define WTIMER_CTRL_QDM                             (0x1UL << 5)                              /**< Quadrature Decoder Mode Selection */
#define _WTIMER_CTRL_QDM_SHIFT                      5                                         /**< Shift value for TIMER_QDM */
#define _WTIMER_CTRL_QDM_MASK                       0x20UL                                    /**< Bit mask for TIMER_QDM */
#define _WTIMER_CTRL_QDM_DEFAULT                    0x00000000UL                              /**< Mode DEFAULT for WTIMER_CTRL */
#define _WTIMER_CTRL_QDM_X2                         0x00000000UL                              /**< Mode X2 for WTIMER_CTRL */
#define _WTIMER_CTRL_QDM_X4                         0x00000001UL                              /**< Mode X4 for WTIMER_CTRL */
#define WTIMER_CTRL_QDM_DEFAULT                     (_WTIMER_CTRL_QDM_DEFAULT << 5)           /**< Shifted mode DEFAULT for WTIMER_CTRL */
#define WTIMER_CTRL_QDM_X2                          (_WTIMER_CTRL_QDM_X2 << 5)                /**< Shifted mode X2 for WTIMER_CTRL */
#define WTIMER_CTRL_QDM_X4                          (_WTIMER_CTRL_QDM_X4 << 5)                /**< Shifted mode X4 for WTIMER_CTRL */
#define WTIMER_CTRL_DEBUGRUN                        (0x1UL << 6)                              /**< Debug Mode Run Enable */
#define _WTIMER_CTRL_DEBUGRUN_SHIFT                 6                                         /**< Shift value for TIMER_DEBUGRUN */
#define _WTIMER_CTRL_DEBUGRUN_MASK                  0x40UL                                    /**< Bit mask for TIMER_DEBUGRUN */
#define _WTIMER_CTRL_DEBUGRUN_DEFAULT               0x00000000UL                              /**< Mode DEFAULT for WTIMER_CTRL */
#define WTIMER_CTRL_DEBUGRUN_DEFAULT                (_WTIMER_CTRL_DEBUGRUN_DEFAULT << 6)      /**< Shifted mode DEFAULT for WTIMER_CTRL */
#define WTIMER_CTRL_DMACLRACT                       (0x1UL << 7)                              /**< DMA Request Clear on Active */
#define _WTIMER_CTRL_DMACLRACT_SHIFT                7                                         /**< Shift value for TIMER_DMACLRACT */
#define _WTIMER_CTRL_DMACLRACT_MASK                 0x80UL                                    /**< Bit mask for TIMER_DMACLRACT */
#define _WTIMER_CTRL_DMACLRACT_DEFAULT              0x00000000UL                              /**< Mode DEFAULT for WTIMER_CTRL */
#define WTIMER_CTRL_DMACLRACT_DEFAULT               (_WTIMER_CTRL_DMACLRACT_DEFAULT << 7)     /**< Shifted mode DEFAULT for WTIMER_CTRL */
#define _WTIMER_CTRL_RISEA_SHIFT                    8                                         /**< Shift value for TIMER_RISEA */
#define _WTIMER_CTRL_RISEA_MASK                     0x300UL                                   /**< Bit mask for TIMER_RISEA */
#define _WTIMER_CTRL_RISEA_DEFAULT                  0x00000000UL                              /**< Mode DEFAULT for WTIMER_CTRL */
#define _WTIMER_CTRL_RISEA_NONE                     0x00000000UL                              /**< Mode NONE for WTIMER_CTRL */
#define _WTIMER_CTRL_RISEA_START                    0x00000001UL                              /**< Mode START for WTIMER_CTRL */
#define _WTIMER_CTRL_RISEA_STOP                     0x00000002UL                              /**< Mode STOP for WTIMER_CTRL */
#define _WTIMER_CTRL_RISEA_RELOADSTART              0x00000003UL                              /**< Mode RELOADSTART for WTIMER_CTRL */
#define WTIMER_CTRL_RISEA_DEFAULT                   (_WTIMER_CTRL_RISEA_DEFAULT << 8)         /**< Shifted mode DEFAULT for WTIMER_CTRL */
#define WTIMER_CTRL_RISEA_NONE                      (_WTIMER_CTRL_RISEA_NONE << 8)            /**< Shifted mode NONE for WTIMER_CTRL */
#define WTIMER_CTRL_RISEA_START                     (_WTIMER_CTRL_RISEA_START << 8)           /**< Shifted mode START for WTIMER_CTRL */
#define WTIMER_CTRL_RISEA_STOP                      (_WTIMER_CTRL_RISEA_STOP << 8)            /**< Shifted mode STOP for WTIMER_CTRL */
#define WTIMER_CTRL_RISEA_RELOADSTART               (_WTIMER_CTRL_RISEA_RELOADSTART << 8)     /**< Shifted mode RELOADSTART for WTIMER_CTRL */
#define _WTIMER_CTRL_FALLA_SHIFT                    10                                        /**< Shift value for TIMER_FALLA */
#define _WTIMER_CTRL_FALLA_MASK                     0xC00UL                                   /**< Bit mask for TIMER_FALLA */
#define _WTIMER_CTRL_FALLA_DEFAULT                  0x00000000UL                              /**< Mode DEFAULT for WTIMER_CTRL */
#define _WTIMER_CTRL_FALLA_NONE                     0x00000000UL                              /**< Mode NONE for WTIMER_CTRL */
#define _WTIMER_CTRL_FALLA_START                    0x00000001UL                              /**< Mode START for WTIMER_CTRL */
#define _WTIMER_CTRL_FALLA_STOP                     0x00000002UL                              /**< Mode STOP for WTIMER_CTRL */
#define _WTIMER_CTRL_FALLA_RELOADSTART              0x00000003UL                              /**< Mode RELOADSTART for WTIMER_CTRL */
#define WTIMER_CTRL_FALLA_DEFAULT                   (_WTIMER_CTRL_FALLA_DEFAULT << 10)        /**< Shifted mode DEFAULT for WTIMER_CTRL */
#define WTIMER_CTRL_FALLA_NONE                      (_WTIMER_CTRL_FALLA_NONE << 10)           /**< Shifted mode NONE for WTIMER_CTRL */
#define WTIMER_CTRL_FALLA_START                     (_WTIMER_CTRL_FALLA_START << 10)          /**< Shifted mode START for WTIMER_CTRL */
#define WTIMER_CTRL_FALLA_STOP                      (_WTIMER_CTRL_FALLA_STOP << 10)           /**< Shifted mode STOP for WTIMER_CTRL */
#define WTIMER_CTRL_FALLA_RELOADSTART               (_WTIMER_CTRL_FALLA_RELOADSTART << 10)    /**< Shifted mode RELOADSTART for WTIMER_CTRL */
#define WTIMER_CTRL_X2CNT                           (0x1UL << 13)                             /**< 2x Count Mode */
#define _WTIMER_CTRL_X2CNT_SHIFT                    13                                        /**< Shift value for TIMER_X2CNT */
#define _WTIMER_CTRL_X2CNT_MASK                     0x2000UL                                  /**< Bit mask for TIMER_X2CNT */
#define _WTIMER_CTRL_X2CNT_DEFAULT                  0x00000000UL                              /**< Mode DEFAULT for WTIMER_CTRL */
#define WTIMER_CTRL_X2CNT_DEFAULT                   (_WTIMER_CTRL_X2CNT_DEFAULT << 13)        /**< Shifted mode DEFAULT for WTIMER_CTRL */
#define WTIMER_CTRL_DISSYNCOUT                      (0x1UL << 14)                             /**< Disable Timer from Start/Stop/Reload other Synchronized Timers */
#define _WTIMER_CTRL_DISSYNCOUT_SHIFT               14                                        /**< Shift value for TIMER_DISSYNCOUT */
#define _WTIMER_CTRL_DISSYNCOUT_MASK                0x4000UL                                  /**< Bit mask for TIMER_DISSYNCOUT */
#define _WTIMER_CTRL_DISSYNCOUT_DEFAULT             0x00000000UL                              /**< Mode DEFAULT for WTIMER_CTRL */
#define WTIMER_CTRL_DISSYNCOUT_DEFAULT              (_WTIMER_CTRL_DISSYNCOUT_DEFAULT << 14)   /**< Shifted mode DEFAULT for WTIMER_CTRL */
#define _WTIMER_CTRL_CLKSEL_SHIFT                   16                                        /**< Shift value for TIMER_CLKSEL */
#define _WTIMER_CTRL_CLKSEL_MASK                    0x30000UL                                 /**< Bit mask for TIMER_CLKSEL */
#define _WTIMER_CTRL_CLKSEL_DEFAULT                 0x00000000UL                              /**< Mode DEFAULT for WTIMER_CTRL */
#define _WTIMER_CTRL_CLKSEL_PRESCHFPERCLK           0x00000000UL                              /**< Mode PRESCHFPERCLK for WTIMER_CTRL */
#define _WTIMER_CTRL_CLKSEL_CC1                     0x00000001UL                              /**< Mode CC1 for WTIMER_CTRL */
#define _WTIMER_CTRL_CLKSEL_TIMEROUF                0x00000002UL                              /**< Mode TIMEROUF for WTIMER_CTRL */
#define WTIMER_CTRL_CLKSEL_DEFAULT                  (_WTIMER_CTRL_CLKSEL_DEFAULT << 16)       /**< Shifted mode DEFAULT for WTIMER_CTRL */
#define WTIMER_CTRL_CLKSEL_PRESCHFPERCLK            (_WTIMER_CTRL_CLKSEL_PRESCHFPERCLK << 16) /**< Shifted mode PRESCHFPERCLK for WTIMER_CTRL */
#define WTIMER_CTRL_CLKSEL_CC1                      (_WTIMER_CTRL_CLKSEL_CC1 << 16)           /**< Shifted mode CC1 for WTIMER_CTRL */
#define WTIMER_CTRL_CLKSEL_TIMEROUF                 (_WTIMER_CTRL_CLKSEL_TIMEROUF << 16)      /**< Shifted mode TIMEROUF for WTIMER_CTRL */
#define _WTIMER_CTRL_PRESC_SHIFT                    24                                        /**< Shift value for TIMER_PRESC */
#define _WTIMER_CTRL_PRESC_MASK                     0xF000000UL                               /**< Bit mask for TIMER_PRESC */
#define _WTIMER_CTRL_PRESC_DEFAULT                  0x00000000UL                              /**< Mode DEFAULT for WTIMER_CTRL */
#define _WTIMER_CTRL_PRESC_DIV1                     0x00000000UL                              /**< Mode DIV1 for WTIMER_CTRL */
#define _WTIMER_CTRL_PRESC_DIV2                     0x00000001UL                              /**< Mode DIV2 for WTIMER_CTRL */
#define _WTIMER_CTRL_PRESC_DIV4                     0x00000002UL                              /**< Mode DIV4 for WTIMER_CTRL */
#define _WTIMER_CTRL_PRESC_DIV8                     0x00000003UL                              /**< Mode DIV8 for WTIMER_CTRL */
#define _WTIMER_CTRL_PRESC_DIV16                    0x00000004UL                              /**< Mode DIV16 for WTIMER_CTRL */
#define _WTIMER_CTRL_PRESC_DIV32                    0x00000005UL                              /**< Mode DIV32 for WTIMER_CTRL */
#define _WTIMER_CTRL_PRESC_DIV64                    0x00000006UL                              /**< Mode DIV64 for WTIMER_CTRL */
#define _WTIMER_CTRL_PRESC_DIV128                   0x00000007UL                              /**< Mode DIV128 for WTIMER_CTRL */
#define _WTIMER_CTRL_PRESC_DIV256                   0x00000008UL                              /**< Mode DIV256 for WTIMER_CTRL */
#define _WTIMER_CTRL_PRESC_DIV512                   0x00000009UL                              /**< Mode DIV512 for WTIMER_CTRL */
#define _WTIMER_CTRL_PRESC_DIV1024                  0x0000000AUL                              /**< Mode DIV1024 for WTIMER_CTRL */
#define WTIMER_CTRL_PRESC_DEFAULT                   (_WTIMER_CTRL_PRESC_DEFAULT << 24)        /**< Shifted mode DEFAULT for WTIMER_CTRL */
#define WTIMER_CTRL_PRESC_DIV1                      (_WTIMER_CTRL_PRESC_DIV1 << 24)           /**< Shifted mode DIV1 for WTIMER_CTRL */
#define WTIMER_CTRL_PRESC_DIV2                      (_WTIMER_CTRL_PRESC_DIV2 << 24)           /**< Shifted mode DIV2 for WTIMER_CTRL */
#define WTIMER_CTRL_PRESC_DIV4                      (_WTIMER_CTRL_PRESC_DIV4 << 24)           /**< Shifted mode DIV4 for WTIMER_CTRL */
#define WTIMER_CTRL_PRESC_DIV8                      (_WTIMER_CTRL_PRESC_DIV8 << 24)           /**< Shifted mode DIV8 for WTIMER_CTRL */
#define WTIMER_CTRL_PRESC_DIV16                     (_WTIMER_CTRL_PRESC_DIV16 << 24)          /**< Shifted mode DIV16 for WTIMER_CTRL */
#define WTIMER_CTRL_PRESC_DIV32                     (_WTIMER_CTRL_PRESC_DIV32 << 24)          /**< Shifted mode DIV32 for WTIMER_CTRL */
#define WTIMER_CTRL_PRESC_DIV64                     (_WTIMER_CTRL_PRESC_DIV64 << 24)          /**< Shifted mode DIV64 for WTIMER_CTRL */
#define WTIMER_CTRL_PRESC_DIV128                    (_WTIMER_CTRL_PRESC_DIV128 << 24)         /**< Shifted mode DIV128 for WTIMER_CTRL */
#define WTIMER_CTRL_PRESC_DIV256                    (_WTIMER_CTRL_PRESC_DIV256 << 24)         /**< Shifted mode DIV256 for WTIMER_CTRL */
#define WTIMER_CTRL_PRESC_DIV512                    (_WTIMER_CTRL_PRESC_DIV512 << 24)         /**< Shifted mode DIV512 for WTIMER_CTRL */
#define WTIMER_CTRL_PRESC_DIV1024                   (_WTIMER_CTRL_PRESC_DIV1024 << 24)        /**< Shifted mode DIV1024 for WTIMER_CTRL */
#define WTIMER_CTRL_ATI                             (0x1UL << 28)                             /**< Always Track Inputs */
#define _WTIMER_CTRL_ATI_SHIFT                      28                                        /**< Shift value for TIMER_ATI */
#define _WTIMER_CTRL_ATI_MASK                       0x10000000UL                              /**< Bit mask for TIMER_ATI */
#define _WTIMER_CTRL_ATI_DEFAULT                    0x00000000UL                              /**< Mode DEFAULT for WTIMER_CTRL */
#define WTIMER_CTRL_ATI_DEFAULT                     (_WTIMER_CTRL_ATI_DEFAULT << 28)          /**< Shifted mode DEFAULT for WTIMER_CTRL */
#define WTIMER_CTRL_RSSCOIST                        (0x1UL << 29)                             /**< Reload-Start Sets Compare Output initial State */
#define _WTIMER_CTRL_RSSCOIST_SHIFT                 29                                        /**< Shift value for TIMER_RSSCOIST */
#define _WTIMER_CTRL_RSSCOIST_MASK                  0x20000000UL                              /**< Bit mask for TIMER_RSSCOIST */
#define _WTIMER_CTRL_RSSCOIST_DEFAULT               0x00000000UL                              /**< Mode DEFAULT for WTIMER_CTRL */
#define WTIMER_CTRL_RSSCOIST_DEFAULT                (_WTIMER_CTRL_RSSCOIST_DEFAULT << 29)     /**< Shifted mode DEFAULT for WTIMER_CTRL */

/* Bit fields for WTIMER CMD */
#define _WTIMER_CMD_RESETVALUE                      0x00000000UL                     /**< Default value for WTIMER_CMD */
#define _WTIMER_CMD_MASK                            0x00000003UL                     /**< Mask for WTIMER_CMD */
#define WTIMER_CMD_START                            (0x1UL << 0)                     /**< Start Timer */
#define _WTIMER_CMD_START_SHIFT                     0                                /**< Shift value for TIMER_START */
#define _WTIMER_CMD_START_MASK                      0x1UL                            /**< Bit mask for TIMER_START */
#define _WTIMER_CMD_START_DEFAULT                   0x00000000UL                     /**< Mode DEFAULT for WTIMER_CMD */
#define WTIMER_CMD_START_DEFAULT                    (_WTIMER_CMD_START_DEFAULT << 0) /**< Shifted mode DEFAULT for WTIMER_CMD */
#define WTIMER_CMD_STOP                             (0x1UL << 1)                     /**< Stop Timer */
#define _WTIMER_CMD_STOP_SHIFT                      1                                /**< Shift value for TIMER_STOP */
#define _WTIMER_CMD_STOP_MASK                       0x2UL                            /**< Bit mask for TIMER_STOP */
#define _WTIMER_CMD_STOP_DEFAULT                    0x00000000UL                     /**< Mode DEFAULT for WTIMER_CMD */
#define WTIMER_CMD_STOP_DEFAULT                     (_WTIMER_CMD_STOP_DEFAULT << 1)  /**< Shifted mode DEFAULT for WTIMER_CMD */

/* Bit fields for WTIMER STATUS */
#define _WTIMER_STATUS_RESETVALUE                   0x00000000UL                           /**< Default value for WTIMER_STATUS */
#define _WTIMER_STATUS_MASK                         0x0F0F0F07UL                           /**< Mask for WTIMER_STATUS */
#define WTIMER_STATUS_RUNNING                       (0x1UL << 0)                           /**< Running */
#define _WTIMER_STATUS_RUNNING_SHIFT                0                                      /**< Shift value for TIMER_RUNNING */
#define _WTIMER_STATUS_RUNNING_MASK                 0x1UL                                  /**< Bit mask for TIMER_RUNNING */
#define _WTIMER_STATUS_RUNNING_DEFAULT              0x00000000UL                           /**< Mode DEFAULT for WTIMER_STATUS */
#define WTIMER_STATUS_RUNNING_DEFAULT               (_WTIMER_STATUS_RUNNING_DEFAULT << 0)  /**< Shifted mode DEFAULT for WTIMER_STATUS */
#define WTIMER_STATUS_DIR                           (0x1UL << 1)                           /**< Direction */
#define _WTIMER_STATUS_DIR_SHIFT                    1                                      /**< Shift value for TIMER_DIR */
#define _WTIMER_STATUS_DIR_MASK                     0x2UL                                  /**< Bit mask for TIMER_DIR */
#define _WTIMER_STATUS_DIR_DEFAULT                  0x00000000UL                           /**< Mode DEFAULT for WTIMER_STATUS */
#define _WTIMER_STATUS_DIR_UP                       0x00000000UL                           /**< Mode UP for WTIMER_STATUS */
#define _WTIMER_STATUS_DIR_DOWN                     0x00000001UL                           /**< Mode DOWN for WTIMER_STATUS */
#define WTIMER_STATUS_DIR_DEFAULT                   (_WTIMER_STATUS_DIR_DEFAULT << 1)      /**< Shifted mode DEFAULT for WTIMER_STATUS */
#define WTIMER_STATUS_DIR_UP                        (_WTIMER_STATUS_DIR_UP << 1)           /**< Shifted mode UP for WTIMER_STATUS */
#define WTIMER_STATUS_DIR_DOWN                      (_WTIMER_STATUS_DIR_DOWN << 1)         /**< Shifted mode DOWN for WTIMER_STATUS */
#define WTIMER_STATUS_TOPBV                         (0x1UL << 2)                           /**< TOPB Valid */
#define _WTIMER_STATUS_TOPBV_SHIFT                  2                                      /**< Shift value for TIMER_TOPBV */
#define _WTIMER_STATUS_TOPBV_MASK                   0x4UL                                  /**< Bit mask for TIMER_TOPBV */
#define _WTIMER_STATUS_TOPBV_DEFAULT                0x00000000UL                           /**< Mode DEFAULT for WTIMER_STATUS */
#define WTIMER_STATUS_TOPBV_DEFAULT                 (_WTIMER_STATUS_TOPBV_DEFAULT << 2)    /**< Shifted mode DEFAULT for WTIMER_STATUS */
#define WTIMER_STATUS_CCVBV0                        (0x1UL << 8)                           /**< CC0 CCVB Valid */
#define _WTIMER_STATUS_CCVBV0_SHIFT                 8                                      /**< Shift value for TIMER_CCVBV0 */
#define _WTIMER_STATUS_CCVBV0_MASK                  0x100UL                                /**< Bit mask for TIMER_CCVBV0 */
#define _WTIMER_STATUS_CCVBV0_DEFAULT               0x00000000UL                           /**< Mode DEFAULT for WTIMER_STATUS */
#define WTIMER_STATUS_CCVBV0_DEFAULT                (_WTIMER_STATUS_CCVBV0_DEFAULT << 8)   /**< Shifted mode DEFAULT for WTIMER_STATUS */
#define WTIMER_STATUS_CCVBV1                        (0x1UL << 9)                           /**< CC1 CCVB Valid */
#define _WTIMER_STATUS_CCVBV1_SHIFT                 9                                      /**< Shift value for TIMER_CCVBV1 */
#define _WTIMER_STATUS_CCVBV1_MASK                  0x200UL                                /**< Bit mask for TIMER_CCVBV1 */
#define _WTIMER_STATUS_CCVBV1_DEFAULT               0x00000000UL                           /**< Mode DEFAULT for WTIMER_STATUS */
#define WTIMER_STATUS_CCVBV1_DEFAULT                (_WTIMER_STATUS_CCVBV1_DEFAULT << 9)   /**< Shifted mode DEFAULT for WTIMER_STATUS */
#define WTIMER_STATUS_CCVBV2                        (0x1UL << 10)                          /**< CC2 CCVB Valid */
#define _WTIMER_STATUS_CCVBV2_SHIFT                 10                                     /**< Shift value for TIMER_CCVBV2 */
#define _WTIMER_STATUS_CCVBV2_MASK                  0x400UL                                /**< Bit mask for TIMER_CCVBV2 */
#define _WTIMER_STATUS_CCVBV2_DEFAULT               0x00000000UL                           /**< Mode DEFAULT for WTIMER_STATUS */
#define WTIMER_STATUS_CCVBV2_DEFAULT                (_WTIMER_STATUS_CCVBV2_DEFAULT << 10)  /**< Shifted mode DEFAULT for WTIMER_STATUS */
#define WTIMER_STATUS_CCVBV3                        (0x1UL << 11)                          /**< CC3 CCVB Valid */
#define _WTIMER_STATUS_CCVBV3_SHIFT                 11                                     /**< Shift value for TIMER_CCVBV3 */
#define _WTIMER_STATUS_CCVBV3_MASK                  0x800UL                                /**< Bit mask for TIMER_CCVBV3 */
#define _WTIMER_STATUS_CCVBV3_DEFAULT               0x00000000UL                           /**< Mode DEFAULT for WTIMER_STATUS */
#define WTIMER_STATUS_CCVBV3_DEFAULT                (_WTIMER_STATUS_CCVBV3_DEFAULT << 11)  /**< Shifted mode DEFAULT for WTIMER_STATUS */
#define WTIMER_STATUS_ICV0                          (0x1UL << 16)                          /**< CC0 Input Capture Valid */
#define _WTIMER_STATUS_ICV0_SHIFT                   16                                     /**< Shift value for TIMER_ICV0 */
#define _WTIMER_STATUS_ICV0_MASK                    0x10000UL                              /**< Bit mask for TIMER_ICV0 */
#define _WTIMER_STATUS_ICV0_DEFAULT                 0x00000000UL                           /**< Mode DEFAULT for WTIMER_STATUS */
#define WTIMER_STATUS_ICV0_DEFAULT                  (_WTIMER_STATUS_ICV0_DEFAULT << 16)    /**< Shifted mode DEFAULT for WTIMER_STATUS */
#define WTIMER_STATUS_ICV1                          (0x1UL << 17)                          /**< CC1 Input Capture Valid */
#define _WTIMER_STATUS_ICV1_SHIFT                   17                                     /**< Shift value for TIMER_ICV1 */
#define _WTIMER_STATUS_ICV1_MASK                    0x20000UL                              /**< Bit mask for TIMER_ICV1 */
#define _WTIMER_STATUS_ICV1_DEFAULT                 0x00000000UL                           /**< Mode DEFAULT for WTIMER_STATUS */
#define WTIMER_STATUS_ICV1_DEFAULT                  (_WTIMER_STATUS_ICV1_DEFAULT << 17)    /**< Shifted mode DEFAULT for WTIMER_STATUS */
#define WTIMER_STATUS_ICV2                          (0x1UL << 18)                          /**< CC2 Input Capture Valid */
#define _WTIMER_STATUS_ICV2_SHIFT                   18                                     /**< Shift value for TIMER_ICV2 */
#define _WTIMER_STATUS_ICV2_MASK                    0x40000UL                              /**< Bit mask for TIMER_ICV2 */
#define _WTIMER_STATUS_ICV2_DEFAULT                 0x00000000UL                           /**< Mode DEFAULT for WTIMER_STATUS */
#define WTIMER_STATUS_ICV2_DEFAULT                  (_WTIMER_STATUS_ICV2_DEFAULT << 18)    /**< Shifted mode DEFAULT for WTIMER_STATUS */
#define WTIMER_STATUS_ICV3                          (0x1UL << 19)                          /**< CC3 Input Capture Valid */
#define _WTIMER_STATUS_ICV3_SHIFT                   19                                     /**< Shift value for TIMER_ICV3 */
#define _WTIMER_STATUS_ICV3_MASK                    0x80000UL                              /**< Bit mask for TIMER_ICV3 */
#define _WTIMER_STATUS_ICV3_DEFAULT                 0x00000000UL                           /**< Mode DEFAULT for WTIMER_STATUS */
#define WTIMER_STATUS_ICV3_DEFAULT                  (_WTIMER_STATUS_ICV3_DEFAULT << 19)    /**< Shifted mode DEFAULT for WTIMER_STATUS */
#define WTIMER_STATUS_CCPOL0                        (0x1UL << 24)                          /**< CC0 Polarity */
#define _WTIMER_STATUS_CCPOL0_SHIFT                 24                                     /**< Shift value for TIMER_CCPOL0 */
#define _WTIMER_STATUS_CCPOL0_MASK                  0x1000000UL                            /**< Bit mask for TIMER_CCPOL0 */
#define _WTIMER_STATUS_CCPOL0_DEFAULT               0x00000000UL                           /**< Mode DEFAULT for WTIMER_STATUS */
#define _WTIMER_STATUS_CCPOL0_LOWRISE               0x00000000UL                           /**< Mode LOWRISE for WTIMER_STATUS */
#define _WTIMER_STATUS_CCPOL0_HIGHFALL              0x00000001UL                           /**< Mode HIGHFALL for WTIMER_STATUS */
#define WTIMER_STATUS_CCPOL0_DEFAULT                (_WTIMER_STATUS_CCPOL0_DEFAULT << 24)  /**< Shifted mode DEFAULT for WTIMER_STATUS */
#define WTIMER_STATUS_CCPOL0_LOWRISE                (_WTIMER_STATUS_CCPOL0_LOWRISE << 24)  /**< Shifted mode LOWRISE for WTIMER_STATUS */
#define WTIMER_STATUS_CCPOL0_HIGHFALL               (_WTIMER_STATUS_CCPOL0_HIGHFALL << 24) /**< Shifted mode HIGHFALL for WTIMER_STATUS */
#define WTIMER_STATUS_CCPOL1                        (0x1UL << 25)                          /**< CC1 Polarity */
#define _WTIMER_STATUS_CCPOL1_SHIFT                 25                                     /**< Shift value for TIMER_CCPOL1 */
#define _WTIMER_STATUS_CCPOL1_MASK                  0x2000000UL                            /**< Bit mask for TIMER_CCPOL1 */
#define _WTIMER_STATUS_CCPOL1_DEFAULT               0x00000000UL                           /**< Mode DEFAULT for WTIMER_STATUS */
#define _WTIMER_STATUS_CCPOL1_LOWRISE               0x00000000UL                           /**< Mode LOWRISE for WTIMER_STATUS */
#define _WTIMER_STATUS_CCPOL1_HIGHFALL              0x00000001UL                           /**< Mode HIGHFALL for WTIMER_STATUS */
#define WTIMER_STATUS_CCPOL1_DEFAULT                (_WTIMER_STATUS_CCPOL1_DEFAULT << 25)  /**< Shifted mode DEFAULT for WTIMER_STATUS */
#define WTIMER_STATUS_CCPOL1_LOWRISE                (_WTIMER_STATUS_CCPOL1_LOWRISE << 25)  /**< Shifted mode LOWRISE for WTIMER_STATUS */
#define WTIMER_STATUS_CCPOL1_HIGHFALL               (_WTIMER_STATUS_CCPOL1_HIGHFALL << 25) /**< Shifted mode HIGHFALL for WTIMER_STATUS */
#define WTIMER_STATUS_CCPOL2                        (0x1UL << 26)                          /**< CC2 Polarity */
#define _WTIMER_STATUS_CCPOL2_SHIFT                 26                                     /**< Shift value for TIMER_CCPOL2 */
#define _WTIMER_STATUS_CCPOL2_MASK                  0x4000000UL                            /**< Bit mask for TIMER_CCPOL2 */
#define _WTIMER_STATUS_CCPOL2_DEFAULT               0x00000000UL                           /**< Mode DEFAULT for WTIMER_STATUS */
#define _WTIMER_STATUS_CCPOL2_LOWRISE               0x00000000UL                           /**< Mode LOWRISE for WTIMER_STATUS */
#define _WTIMER_STATUS_CCPOL2_HIGHFALL              0x00000001UL                           /**< Mode HIGHFALL for WTIMER_STATUS */
#define WTIMER_STATUS_CCPOL2_DEFAULT                (_WTIMER_STATUS_CCPOL2_DEFAULT << 26)  /**< Shifted mode DEFAULT for WTIMER_STATUS */
#define WTIMER_STATUS_CCPOL2_LOWRISE                (_WTIMER_STATUS_CCPOL2_LOWRISE << 26)  /**< Shifted mode LOWRISE for WTIMER_STATUS */
#define WTIMER_STATUS_CCPOL2_HIGHFALL               (_WTIMER_STATUS_CCPOL2_HIGHFALL << 26) /**< Shifted mode HIGHFALL for WTIMER_STATUS */
#define WTIMER_STATUS_CCPOL3                        (0x1UL << 27)                          /**< CC3 Polarity */
#define _WTIMER_STATUS_CCPOL3_SHIFT                 27                                     /**< Shift value for TIMER_CCPOL3 */
#define _WTIMER_STATUS_CCPOL3_MASK                  0x8000000UL                            /**< Bit mask for TIMER_CCPOL3 */
#define _WTIMER_STATUS_CCPOL3_DEFAULT               0x00000000UL                           /**< Mode DEFAULT for WTIMER_STATUS */
#define _WTIMER_STATUS_CCPOL3_LOWRISE               0x00000000UL                           /**< Mode LOWRISE for WTIMER_STATUS */
#define _WTIMER_STATUS_CCPOL3_HIGHFALL              0x00000001UL                           /**< Mode HIGHFALL for WTIMER_STATUS */
#define WTIMER_STATUS_CCPOL3_DEFAULT                (_WTIMER_STATUS_CCPOL3_DEFAULT << 27)  /**< Shifted mode DEFAULT for WTIMER_STATUS */
#define WTIMER_STATUS_CCPOL3_LOWRISE                (_WTIMER_STATUS_CCPOL3_LOWRISE << 27)  /**< Shifted mode LOWRISE for WTIMER_STATUS */
#define WTIMER_STATUS_CCPOL3_HIGHFALL               (_WTIMER_STATUS_CCPOL3_HIGHFALL << 27) /**< Shifted mode HIGHFALL for WTIMER_STATUS */

/* Bit fields for WTIMER IF */
#define _WTIMER_IF_RESETVALUE                       0x00000000UL                      /**< Default value for WTIMER_IF */
#define _WTIMER_IF_MASK                             0x00000FF7UL                      /**< Mask for WTIMER_IF */
#define WTIMER_IF_OF                                (0x1UL << 0)                      /**< Overflow Interrupt Flag */
#define _WTIMER_IF_OF_SHIFT                         0                                 /**< Shift value for TIMER_OF */
#define _WTIMER_IF_OF_MASK                          0x1UL                             /**< Bit mask for TIMER_OF */
#define _WTIMER_IF_OF_DEFAULT                       0x00000000UL                      /**< Mode DEFAULT for WTIMER_IF */
#define WTIMER_IF_OF_DEFAULT                        (_WTIMER_IF_OF_DEFAULT << 0)      /**< Shifted mode DEFAULT for WTIMER_IF */
#define WTIMER_IF_UF                                (0x1UL << 1)                      /**< Underflow Interrupt Flag */
#define _WTIMER_IF_UF_SHIFT                         1                                 /**< Shift value for TIMER_UF */
#define _WTIMER_IF_UF_MASK                          0x2UL                             /**< Bit mask for TIMER_UF */
#define _WTIMER_IF_UF_DEFAULT                       0x00000000UL                      /**< Mode DEFAULT for WTIMER_IF */
#define WTIMER_IF_UF_DEFAULT                        (_WTIMER_IF_UF_DEFAULT << 1)      /**< Shifted mode DEFAULT for WTIMER_IF */
#define WTIMER_IF_DIRCHG                            (0x1UL << 2)                      /**< Direction Change Detect Interrupt Flag */
#define _WTIMER_IF_DIRCHG_SHIFT                     2                                 /**< Shift value for TIMER_DIRCHG */
#define _WTIMER_IF_DIRCHG_MASK                      0x4UL                             /**< Bit mask for TIMER_DIRCHG */
#define _WTIMER_IF_DIRCHG_DEFAULT                   0x00000000UL                      /**< Mode DEFAULT for WTIMER_IF */
#define WTIMER_IF_DIRCHG_DEFAULT                    (_WTIMER_IF_DIRCHG_DEFAULT << 2)  /**< Shifted mode DEFAULT for WTIMER_IF */
#define WTIMER_IF_CC0                               (0x1UL << 4)                      /**< CC Channel 0 Interrupt Flag */
#define _WTIMER_IF_CC0_SHIFT                        4                                 /**< Shift value for TIMER_CC0 */
#define _WTIMER_IF_CC0_MASK                         0x10UL                            /**< Bit mask for TIMER_CC0 */
#define _WTIMER_IF_CC0_DEFAULT                      0x00000000UL                      /**< Mode DEFAULT for WTIMER_IF */
#define WTIMER_IF_CC0_DEFAULT                       (_WTIMER_IF_CC0_DEFAULT << 4)     /**< Shifted mode DEFAULT for WTIMER_IF */
#define WTIMER_IF_CC1                               (0x1UL << 5)                      /**< CC Channel 1 Interrupt Flag */
#define _WTIMER_IF_CC1_SHIFT                        5                                 /**< Shift value for TIMER_CC1 */
#define _WTIMER_IF_CC1_MASK                         0x20UL                            /**< Bit mask for TIMER_CC1 */
#define _WTIMER_IF_CC1_DEFAULT                      0x00000000UL                      /**< Mode DEFAULT for WTIMER_IF */
#define WTIMER_IF_CC1_DEFAULT                       (_WTIMER_IF_CC1_DEFAULT << 5)     /**< Shifted mode DEFAULT for WTIMER_IF */
#define WTIMER_IF_CC2                               (0x1UL << 6)                      /**< CC Channel 2 Interrupt Flag */
#define _WTIMER_IF_CC2_SHIFT                        6                                 /**< Shift value for TIMER_CC2 */
#define _WTIMER_IF_CC2_MASK                         0x40UL                            /**< Bit mask for TIMER_CC2 */
#define _WTIMER_IF_CC2_DEFAULT                      0x00000000UL                      /**< Mode DEFAULT for WTIMER_IF */
#define WTIMER_IF_CC2_DEFAULT                       (_WTIMER_IF_CC2_DEFAULT << 6)     /**< Shifted mode DEFAULT for WTIMER_IF */
#define WTIMER_IF_CC3                               (0x1UL << 7)                      /**< CC Channel 3 Interrupt Flag */
#define _WTIMER_IF_CC3_SHIFT                        7                                 /**< Shift value for TIMER_CC3 */
#define _WTIMER_IF_CC3_MASK                         0x80UL                            /**< Bit mask for TIMER_CC3 */
#define _WTIMER_IF_CC3_DEFAULT                      0x00000000UL                      /**< Mode DEFAULT for WTIMER_IF */
#define WTIMER_IF_CC3_DEFAULT                       (_WTIMER_IF_CC3_DEFAULT << 7)     /**< Shifted mode DEFAULT for WTIMER_IF */
#define WTIMER_IF_ICBOF0                            (0x1UL << 8)                      /**< CC Channel 0 Input Capture Buffer Overflow Interrupt Flag */
#define _WTIMER_IF_ICBOF0_SHIFT                     8                                 /**< Shift value for TIMER_ICBOF0 */
#define _WTIMER_IF_ICBOF0_MASK                      0x100UL                           /**< Bit mask for TIMER_ICBOF0 */
#define _WTIMER_IF_ICBOF0_DEFAULT                   0x00000000UL                      /**< Mode DEFAULT for WTIMER_IF */
#define WTIMER_IF_ICBOF0_DEFAULT                    (_WTIMER_IF_ICBOF0_DEFAULT << 8)  /**< Shifted mode DEFAULT for WTIMER_IF */
#define WTIMER_IF_ICBOF1                            (0x1UL << 9)                      /**< CC Channel 1 Input Capture Buffer Overflow Interrupt Flag */
#define _WTIMER_IF_ICBOF1_SHIFT                     9                                 /**< Shift value for TIMER_ICBOF1 */
#define _WTIMER_IF_ICBOF1_MASK                      0x200UL                           /**< Bit mask for TIMER_ICBOF1 */
#define _WTIMER_IF_ICBOF1_DEFAULT                   0x00000000UL                      /**< Mode DEFAULT for WTIMER_IF */
#define WTIMER_IF_ICBOF1_DEFAULT                    (_WTIMER_IF_ICBOF1_DEFAULT << 9)  /**< Shifted mode DEFAULT for WTIMER_IF */
#define WTIMER_IF_ICBOF2                            (0x1UL << 10)                     /**< CC Channel 2 Input Capture Buffer Overflow Interrupt Flag */
#define _WTIMER_IF_ICBOF2_SHIFT                     10                                /**< Shift value for TIMER_ICBOF2 */
#define _WTIMER_IF_ICBOF2_MASK                      0x400UL                           /**< Bit mask for TIMER_ICBOF2 */
#define _WTIMER_IF_ICBOF2_DEFAULT                   0x00000000UL                      /**< Mode DEFAULT for WTIMER_IF */
#define WTIMER_IF_ICBOF2_DEFAULT                    (_WTIMER_IF_ICBOF2_DEFAULT << 10) /**< Shifted mode DEFAULT for WTIMER_IF */
#define WTIMER_IF_ICBOF3                            (0x1UL << 11)                     /**< CC Channel 3 Input Capture Buffer Overflow Interrupt Flag */
#define _WTIMER_IF_ICBOF3_SHIFT                     11                                /**< Shift value for TIMER_ICBOF3 */
#define _WTIMER_IF_ICBOF3_MASK                      0x800UL                           /**< Bit mask for TIMER_ICBOF3 */
#define _WTIMER_IF_ICBOF3_DEFAULT                   0x00000000UL                      /**< Mode DEFAULT for WTIMER_IF */
#define WTIMER_IF_ICBOF3_DEFAULT                    (_WTIMER_IF_ICBOF3_DEFAULT << 11) /**< Shifted mode DEFAULT for WTIMER_IF */

/* Bit fields for WTIMER IFS */
#define _WTIMER_IFS_RESETVALUE                      0x00000000UL                       /**< Default value for WTIMER_IFS */
#define _WTIMER_IFS_MASK                            0x00000FF7UL                       /**< Mask for WTIMER_IFS */
#define WTIMER_IFS_OF                               (0x1UL << 0)                       /**< Set OF Interrupt Flag */
#define _WTIMER_IFS_OF_SHIFT                        0                                  /**< Shift value for TIMER_OF */
#define _WTIMER_IFS_OF_MASK                         0x1UL                              /**< Bit mask for TIMER_OF */
#define _WTIMER_IFS_OF_DEFAULT                      0x00000000UL                       /**< Mode DEFAULT for WTIMER_IFS */
#define WTIMER_IFS_OF_DEFAULT                       (_WTIMER_IFS_OF_DEFAULT << 0)      /**< Shifted mode DEFAULT for WTIMER_IFS */
#define WTIMER_IFS_UF                               (0x1UL << 1)                       /**< Set UF Interrupt Flag */
#define _WTIMER_IFS_UF_SHIFT                        1                                  /**< Shift value for TIMER_UF */
#define _WTIMER_IFS_UF_MASK                         0x2UL                              /**< Bit mask for TIMER_UF */
#define _WTIMER_IFS_UF_DEFAULT                      0x00000000UL                       /**< Mode DEFAULT for WTIMER_IFS */
#define WTIMER_IFS_UF_DEFAULT                       (_WTIMER_IFS_UF_DEFAULT << 1)      /**< Shifted mode DEFAULT for WTIMER_IFS */
#define WTIMER_IFS_DIRCHG                           (0x1UL << 2)                       /**< Set DIRCHG Interrupt Flag */
#define _WTIMER_IFS_DIRCHG_SHIFT                    2                                  /**< Shift value for TIMER_DIRCHG */
#define _WTIMER_IFS_DIRCHG_MASK                     0x4UL                              /**< Bit mask for TIMER_DIRCHG */
#define _WTIMER_IFS_DIRCHG_DEFAULT                  0x00000000UL                       /**< Mode DEFAULT for WTIMER_IFS */
#define WTIMER_IFS_DIRCHG_DEFAULT                   (_WTIMER_IFS_DIRCHG_DEFAULT << 2)  /**< Shifted mode DEFAULT for WTIMER_IFS */
#define WTIMER_IFS_CC0                              (0x1UL << 4)                       /**< Set CC0 Interrupt Flag */
#define _WTIMER_IFS_CC0_SHIFT                       4                                  /**< Shift value for TIMER_CC0 */
#define _WTIMER_IFS_CC0_MASK                        0x10UL                             /**< Bit mask for TIMER_CC0 */
#define _WTIMER_IFS_CC0_DEFAULT                     0x00000000UL                       /**< Mode DEFAULT for WTIMER_IFS */
#define WTIMER_IFS_CC0_DEFAULT                      (_WTIMER_IFS_CC0_DEFAULT << 4)     /**< Shifted mode DEFAULT for WTIMER_IFS */
#define WTIMER_IFS_CC1                              (0x1UL << 5)                       /**< Set CC1 Interrupt Flag */
#define _WTIMER_IFS_CC1_SHIFT                       5                                  /**< Shift value for TIMER_CC1 */
#define _WTIMER_IFS_CC1_MASK                        0x20UL                             /**< Bit mask for TIMER_CC1 */
#define _WTIMER_IFS_CC1_DEFAULT                     0x00000000UL                       /**< Mode DEFAULT for WTIMER_IFS */
#define WTIMER_IFS_CC1_DEFAULT                      (_WTIMER_IFS_CC1_DEFAULT << 5)     /**< Shifted mode DEFAULT for WTIMER_IFS */
#define WTIMER_IFS_CC2                              (0x1UL << 6)                       /**< Set CC2 Interrupt Flag */
#define _WTIMER_IFS_CC2_SHIFT                       6                                  /**< Shift value for TIMER_CC2 */
#define _WTIMER_IFS_CC2_MASK                        0x40UL                             /**< Bit mask for TIMER_CC2 */
#define _WTIMER_IFS_CC2_DEFAULT                     0x00000000UL                       /**< Mode DEFAULT for WTIMER_IFS */
#define WTIMER_IFS_CC2_DEFAULT                      (_WTIMER_IFS_CC2_DEFAULT << 6)     /**< Shifted mode DEFAULT for WTIMER_IFS */
#define WTIMER_IFS_CC3                              (0x1UL << 7)                       /**< Set CC3 Interrupt Flag */
#define _WTIMER_IFS_CC3_SHIFT                       7                                  /**< Shift value for TIMER_CC3 */
#define _WTIMER_IFS_CC3_MASK                        0x80UL                             /**< Bit mask for TIMER_CC3 */
#define _WTIMER_IFS_CC3_DEFAULT                     0x00000000UL                       /**< Mode DEFAULT for WTIMER_IFS */
#define WTIMER_IFS_CC3_DEFAULT                      (_WTIMER_IFS_CC3_DEFAULT << 7)     /**< Shifted mode DEFAULT for WTIMER_IFS */
#define WTIMER_IFS_ICBOF0                           (0x1UL << 8)                       /**< Set ICBOF0 Interrupt Flag */
#define _WTIMER_IFS_ICBOF0_SHIFT                    8                                  /**< Shift value for TIMER_ICBOF0 */
#define _WTIMER_IFS_ICBOF0_MASK                     0x100UL                            /**< Bit mask for TIMER_ICBOF0 */
#define _WTIMER_IFS_ICBOF0_DEFAULT                  0x00000000UL                       /**< Mode DEFAULT for WTIMER_IFS */
#define WTIMER_IFS_ICBOF0_DEFAULT                   (_WTIMER_IFS_ICBOF0_DEFAULT << 8)  /**< Shifted mode DEFAULT for WTIMER_IFS */
#define WTIMER_IFS_ICBOF1                           (0x1UL << 9)                       /**< Set ICBOF1 Interrupt Flag */
#define _WTIMER_IFS_ICBOF1_SHIFT                    9                                  /**< Shift value for TIMER_ICBOF1 */
#define _WTIMER_IFS_ICBOF1_MASK                     0x200UL                            /**< Bit mask for TIMER_ICBOF1 */
#define _WTIMER_IFS_ICBOF1_DEFAULT                  0x00000000UL                       /**< Mode DEFAULT for WTIMER_IFS */
#define WTIMER_IFS_ICBOF1_DEFAULT                   (_WTIMER_IFS_ICBOF1_DEFAULT << 9)  /**< Shifted mode DEFAULT for WTIMER_IFS */
#define WTIMER_IFS_ICBOF2                           (0x1UL << 10)                      /**< Set ICBOF2 Interrupt Flag */
#define _WTIMER_IFS_ICBOF2_SHIFT                    10                                 /**< Shift value for TIMER_ICBOF2 */
#define _WTIMER_IFS_ICBOF2_MASK                     0x400UL                            /**< Bit mask for TIMER_ICBOF2 */
#define _WTIMER_IFS_ICBOF2_DEFAULT                  0x00000000UL                       /**< Mode DEFAULT for WTIMER_IFS */
#define WTIMER_IFS_ICBOF2_DEFAULT                   (_WTIMER_IFS_ICBOF2_DEFAULT << 10) /**< Shifted mode DEFAULT for WTIMER_IFS */
#define WTIMER_IFS_ICBOF3                           (0x1UL << 11)                      /**< Set ICBOF3 Interrupt Flag */
#define _WTIMER_IFS_ICBOF3_SHIFT                    11                                 /**< Shift value for TIMER_ICBOF3 */
#define _WTIMER_IFS_ICBOF3_MASK                     0x800UL                            /**< Bit mask for TIMER_ICBOF3 */
#define _WTIMER_IFS_ICBOF3_DEFAULT                  0x00000000UL                       /**< Mode DEFAULT for WTIMER_IFS */
#define WTIMER_IFS_ICBOF3_DEFAULT                   (_WTIMER_IFS_ICBOF3_DEFAULT << 11) /**< Shifted mode DEFAULT for WTIMER_IFS */

/* Bit fields for WTIMER IFC */
#define _WTIMER_IFC_RESETVALUE                      0x00000000UL                       /**< Default value for WTIMER_IFC */
#define _WTIMER_IFC_MASK                            0x00000FF7UL                       /**< Mask for WTIMER_IFC */
#define WTIMER_IFC_OF                               (0x1UL << 0)                       /**< Clear OF Interrupt Flag */
#define _WTIMER_IFC_OF_SHIFT                        0                                  /**< Shift value for TIMER_OF */
#define _WTIMER_IFC_OF_MASK                         0x1UL                              /**< Bit mask for TIMER_OF */
#define _WTIMER_IFC_OF_DEFAULT                      0x00000000UL                       /**< Mode DEFAULT for WTIMER_IFC */
#define WTIMER_IFC_OF_DEFAULT                       (_WTIMER_IFC_OF_DEFAULT << 0)      /**< Shifted mode DEFAULT for WTIMER_IFC */
#define WTIMER_IFC_UF                               (0x1UL << 1)                       /**< Clear UF Interrupt Flag */
#define _WTIMER_IFC_UF_SHIFT                        1                                  /**< Shift value for TIMER_UF */
#define _WTIMER_IFC_UF_MASK                         0x2UL                              /**< Bit mask for TIMER_UF */
#define _WTIMER_IFC_UF_DEFAULT                      0x00000000UL                       /**< Mode DEFAULT for WTIMER_IFC */
#define WTIMER_IFC_UF_DEFAULT                       (_WTIMER_IFC_UF_DEFAULT << 1)      /**< Shifted mode DEFAULT for WTIMER_IFC */
#define WTIMER_IFC_DIRCHG                           (0x1UL << 2)                       /**< Clear DIRCHG Interrupt Flag */
#define _WTIMER_IFC_DIRCHG_SHIFT                    2                                  /**< Shift value for TIMER_DIRCHG */
#define _WTIMER_IFC_DIRCHG_MASK                     0x4UL                              /**< Bit mask for TIMER_DIRCHG */
#define _WTIMER_IFC_DIRCHG_DEFAULT                  0x00000000UL                       /**< Mode DEFAULT for WTIMER_IFC */
#define WTIMER_IFC_DIRCHG_DEFAULT                   (_WTIMER_IFC_DIRCHG_DEFAULT << 2)  /**< Shifted mode DEFAULT for WTIMER_IFC */
#define WTIMER_IFC_CC0                              (0x1UL << 4)                       /**< Clear CC0 Interrupt Flag */
#define _WTIMER_IFC_CC0_SHIFT                       4                                  /**< Shift value for TIMER_CC0 */
#define _WTIMER_IFC_CC0_MASK                        0x10UL                             /**< Bit mask for TIMER_CC0 */
#define _WTIMER_IFC_CC0_DEFAULT                     0x00000000UL                       /**< Mode DEFAULT for WTIMER_IFC */
#define WTIMER_IFC_CC0_DEFAULT                      (_WTIMER_IFC_CC0_DEFAULT << 4)     /**< Shifted mode DEFAULT for WTIMER_IFC */
#define WTIMER_IFC_CC1                              (0x1UL << 5)                       /**< Clear CC1 Interrupt Flag */
#define _WTIMER_IFC_CC1_SHIFT                       5                                  /**< Shift value for TIMER_CC1 */
#define _WTIMER_IFC_CC1_MASK                        0x20UL                             /**< Bit mask for TIMER_CC1 */
#define _WTIMER_IFC_CC1_DEFAULT                     0x00000000UL                       /**< Mode DEFAULT for WTIMER_IFC */
#define WTIMER_IFC_CC1_DEFAULT                      (_WTIMER_IFC_CC1_DEFAULT << 5)     /**< Shifted mode DEFAULT for WTIMER_IFC */
#define WTIMER_IFC_CC2                              (0x1UL << 6)                       /**< Clear CC2 Interrupt Flag */
#define _WTIMER_IFC_CC2_SHIFT                       6                                  /**< Shift value for TIMER_CC2 */
#define _WTIMER_IFC_CC2_MASK                        0x40UL                             /**< Bit mask for TIMER_CC2 */
#define _WTIMER_IFC_CC2_DEFAULT                     0x00000000UL                       /**< Mode DEFAULT for WTIMER_IFC */
#define WTIMER_IFC_CC2_DEFAULT                      (_WTIMER_IFC_CC2_DEFAULT << 6)     /**< Shifted mode DEFAULT for WTIMER_IFC */
#define WTIMER_IFC_CC3                              (0x1UL << 7)                       /**< Clear CC3 Interrupt Flag */
#define _WTIMER_IFC_CC3_SHIFT                       7                                  /**< Shift value for TIMER_CC3 */
#define _WTIMER_IFC_CC3_MASK                        0x80UL                             /**< Bit mask for TIMER_CC3 */
#define _WTIMER_IFC_CC3_DEFAULT                     0x00000000UL                       /**< Mode DEFAULT for WTIMER_IFC */
#define WTIMER_IFC_CC3_DEFAULT                      (_WTIMER_IFC_CC3_DEFAULT << 7)     /**< Shifted mode DEFAULT for WTIMER_IFC */
#define WTIMER_IFC_ICBOF0                           (0x1UL << 8)                       /**< Clear ICBOF0 Interrupt Flag */
#define _WTIMER_IFC_ICBOF0_SHIFT                    8                                  /**< Shift value for TIMER_ICBOF0 */
#define _WTIMER_IFC_ICBOF0_MASK                     0x100UL                            /**< Bit mask for TIMER_ICBOF0 */
#define _WTIMER_IFC_ICBOF0_DEFAULT                  0x00000000UL                       /**< Mode DEFAULT for WTIMER_IFC */
#define WTIMER_IFC_ICBOF0_DEFAULT                   (_WTIMER_IFC_ICBOF0_DEFAULT << 8)  /**< Shifted mode DEFAULT for WTIMER_IFC */
#define WTIMER_IFC_ICBOF1                           (0x1UL << 9)                       /**< Clear ICBOF1 Interrupt Flag */
#define _WTIMER_IFC_ICBOF1_SHIFT                    9                                  /**< Shift value for TIMER_ICBOF1 */
#define _WTIMER_IFC_ICBOF1_MASK                     0x200UL                            /**< Bit mask for TIMER_ICBOF1 */
#define _WTIMER_IFC_ICBOF1_DEFAULT                  0x00000000UL                       /**< Mode DEFAULT for WTIMER_IFC */
#define WTIMER_IFC_ICBOF1_DEFAULT                   (_WTIMER_IFC_ICBOF1_DEFAULT << 9)  /**< Shifted mode DEFAULT for WTIMER_IFC */
#define WTIMER_IFC_ICBOF2                           (0x1UL << 10)                      /**< Clear ICBOF2 Interrupt Flag */
#define _WTIMER_IFC_ICBOF2_SHIFT                    10                                 /**< Shift value for TIMER_ICBOF2 */
#define _WTIMER_IFC_ICBOF2_MASK                     0x400UL                            /**< Bit mask for TIMER_ICBOF2 */
#define _WTIMER_IFC_ICBOF2_DEFAULT                  0x00000000UL                       /**< Mode DEFAULT for WTIMER_IFC */
#define WTIMER_IFC_ICBOF2_DEFAULT                   (_WTIMER_IFC_ICBOF2_DEFAULT << 10) /**< Shifted mode DEFAULT for WTIMER_IFC */
#define WTIMER_IFC_ICBOF3                           (0x1UL << 11)                      /**< Clear ICBOF3 Interrupt Flag */
#define _WTIMER_IFC_ICBOF3_SHIFT                    11                                 /**< Shift value for TIMER_ICBOF3 */
#define _WTIMER_IFC_ICBOF3_MASK                     0x800UL                            /**< Bit mask for TIMER_ICBOF3 */
#define _WTIMER_IFC_ICBOF3_DEFAULT                  0x00000000UL                       /**< Mode DEFAULT for WTIMER_IFC */
#define WTIMER_IFC_ICBOF3_DEFAULT                   (_WTIMER_IFC_ICBOF3_DEFAULT << 11) /**< Shifted mode DEFAULT for WTIMER_IFC */

/* Bit fields for WTIMER IEN */
#define _WTIMER_IEN_RESETVALUE                      0x00000000UL                       /**< Default value for WTIMER_IEN */
#define _WTIMER_IEN_MASK                            0x00000FF7UL                       /**< Mask for WTIMER_IEN */
#define WTIMER_IEN_OF                               (0x1UL << 0)                       /**< OF Interrupt Enable */
#define _WTIMER_IEN_OF_SHIFT                        0                                  /**< Shift value for TIMER_OF */
#define _WTIMER_IEN_OF_MASK                         0x1UL                              /**< Bit mask for TIMER_OF */
#define _WTIMER_IEN_OF_DEFAULT                      0x00000000UL                       /**< Mode DEFAULT for WTIMER_IEN */
#define WTIMER_IEN_OF_DEFAULT                       (_WTIMER_IEN_OF_DEFAULT << 0)      /**< Shifted mode DEFAULT for WTIMER_IEN */
#define WTIMER_IEN_UF                               (0x1UL << 1)                       /**< UF Interrupt Enable */
#define _WTIMER_IEN_UF_SHIFT                        1                                  /**< Shift value for TIMER_UF */
#define _WTIMER_IEN_UF_MASK                         0x2UL                              /**< Bit mask for TIMER_UF */
#define _WTIMER_IEN_UF_DEFAULT                      0x00000000UL                       /**< Mode DEFAULT for WTIMER_IEN */
#define WTIMER_IEN_UF_DEFAULT                       (_WTIMER_IEN_UF_DEFAULT << 1)      /**< Shifted mode DEFAULT for WTIMER_IEN */
#define WTIMER_IEN_DIRCHG                           (0x1UL << 2)                       /**< DIRCHG Interrupt Enable */
#define _WTIMER_IEN_DIRCHG_SHIFT                    2                                  /**< Shift value for TIMER_DIRCHG */
#define _WTIMER_IEN_DIRCHG_MASK                     0x4UL                              /**< Bit mask for TIMER_DIRCHG */
#define _WTIMER_IEN_DIRCHG_DEFAULT                  0x00000000UL                       /**< Mode DEFAULT for WTIMER_IEN */
#define WTIMER_IEN_DIRCHG_DEFAULT                   (_WTIMER_IEN_DIRCHG_DEFAULT << 2)  /**< Shifted mode DEFAULT for WTIMER_IEN */
#define WTIMER_IEN_CC0                              (0x1UL << 4)                       /**< CC0 Interrupt Enable */
#define _WTIMER_IEN_CC0_SHIFT                       4                                  /**< Shift value for TIMER_CC0 */
#define _WTIMER_IEN_CC0_MASK                        0x10UL                             /**< Bit mask for TIMER_CC0 */
#define _WTIMER_IEN_CC0_DEFAULT                     0x00000000UL                       /**< Mode DEFAULT for WTIMER_IEN */
#define WTIMER_IEN_CC0_DEFAULT                      (_WTIMER_IEN_CC0_DEFAULT << 4)     /**< Shifted mode DEFAULT for WTIMER_IEN */
#define WTIMER_IEN_CC1                              (0x1UL << 5)                       /**< CC1 Interrupt Enable */
#define _WTIMER_IEN_CC1_SHIFT                       5                                  /**< Shift value for TIMER_CC1 */
#define _WTIMER_IEN_CC1_MASK                        0x20UL                             /**< Bit mask for TIMER_CC1 */
#define _WTIMER_IEN_CC1_DEFAULT                     0x00000000UL                       /**< Mode DEFAULT for WTIMER_IEN */
#define WTIMER_IEN_CC1_DEFAULT                      (_WTIMER_IEN_CC1_DEFAULT << 5)     /**< Shifted mode DEFAULT for WTIMER_IEN */
#define WTIMER_IEN_CC2                              (0x1UL << 6)                       /**< CC2 Interrupt Enable */
#define _WTIMER_IEN_CC2_SHIFT                       6                                  /**< Shift value for TIMER_CC2 */
#define _WTIMER_IEN_CC2_MASK                        0x40UL                             /**< Bit mask for TIMER_CC2 */
#define _WTIMER_IEN_CC2_DEFAULT                     0x00000000UL                       /**< Mode DEFAULT for WTIMER_IEN */
#define WTIMER_IEN_CC2_DEFAULT                      (_WTIMER_IEN_CC2_DEFAULT << 6)     /**< Shifted mode DEFAULT for WTIMER_IEN */
#define WTIMER_IEN_CC3                              (0x1UL << 7)                       /**< CC3 Interrupt Enable */
#define _WTIMER_IEN_CC3_SHIFT                       7                                  /**< Shift value for TIMER_CC3 */
#define _WTIMER_IEN_CC3_MASK                        0x80UL                             /**< Bit mask for TIMER_CC3 */
#define _WTIMER_IEN_CC3_DEFAULT                     0x00000000UL                       /**< Mode DEFAULT for WTIMER_IEN */
#define WTIMER_IEN_CC3_DEFAULT                      (_WTIMER_IEN_CC3_DEFAULT << 7)     /**< Shifted mode DEFAULT for WTIMER_IEN */
#define WTIMER_IEN_ICBOF0                           (0x1UL << 8)                       /**< ICBOF0 Interrupt Enable */
#define _WTIMER_IEN_ICBOF0_SHIFT                    8                                  /**< Shift value for TIMER_ICBOF0 */
#define _WTIMER_IEN_ICBOF0_MASK                     0x100UL                            /**< Bit mask for TIMER_ICBOF0 */
#define _WTIMER_IEN_ICBOF0_DEFAULT                  0x00000000UL                       /**< Mode DEFAULT for WTIMER_IEN */
#define WTIMER_IEN_ICBOF0_DEFAULT                   (_WTIMER_IEN_ICBOF0_DEFAULT << 8)  /**< Shifted mode DEFAULT for WTIMER_IEN */
#define WTIMER_IEN_ICBOF1                           (0x1UL << 9)                       /**< ICBOF1 Interrupt Enable */
#define _WTIMER_IEN_ICBOF1_SHIFT                    9                                  /**< Shift value for TIMER_ICBOF1 */
#define _WTIMER_IEN_ICBOF1_MASK                     0x200UL                            /**< Bit mask for TIMER_ICBOF1 */
#define _WTIMER_IEN_ICBOF1_DEFAULT                  0x00000000UL                       /**< Mode DEFAULT for WTIMER_IEN */
#define WTIMER_IEN_ICBOF1_DEFAULT                   (_WTIMER_IEN_ICBOF1_DEFAULT << 9)  /**< Shifted mode DEFAULT for WTIMER_IEN */
#define WTIMER_IEN_ICBOF2                           (0x1UL << 10)                      /**< ICBOF2 Interrupt Enable */
#define _WTIMER_IEN_ICBOF2_SHIFT                    10                                 /**< Shift value for TIMER_ICBOF2 */
#define _WTIMER_IEN_ICBOF2_MASK                     0x400UL                            /**< Bit mask for TIMER_ICBOF2 */
#define _WTIMER_IEN_ICBOF2_DEFAULT                  0x00000000UL                       /**< Mode DEFAULT for WTIMER_IEN */
#define WTIMER_IEN_ICBOF2_DEFAULT                   (_WTIMER_IEN_ICBOF2_DEFAULT << 10) /**< Shifted mode DEFAULT for WTIMER_IEN */
#define WTIMER_IEN_ICBOF3                           (0x1UL << 11)                      /**< ICBOF3 Interrupt Enable */
#define _WTIMER_IEN_ICBOF3_SHIFT                    11                                 /**< Shift value for TIMER_ICBOF3 */
#define _WTIMER_IEN_ICBOF3_MASK                     0x800UL                            /**< Bit mask for TIMER_ICBOF3 */
#define _WTIMER_IEN_ICBOF3_DEFAULT                  0x00000000UL                       /**< Mode DEFAULT for WTIMER_IEN */
#define WTIMER_IEN_ICBOF3_DEFAULT                   (_WTIMER_IEN_ICBOF3_DEFAULT << 11) /**< Shifted mode DEFAULT for WTIMER_IEN */

/* Bit fields for WTIMER TOP */
#define _WTIMER_TOP_RESETVALUE                      0x0000FFFFUL                   /**< Default value for WTIMER_TOP */
#define _WTIMER_TOP_MASK                            0xFFFFFFFFUL                   /**< Mask for WTIMER_TOP */
#define _WTIMER_TOP_TOP_SHIFT                       0                              /**< Shift value for TIMER_TOP */
#define _WTIMER_TOP_TOP_MASK                        0xFFFFFFFFUL                   /**< Bit mask for TIMER_TOP */
#define _WTIMER_TOP_TOP_DEFAULT                     0x0000FFFFUL                   /**< Mode DEFAULT for WTIMER_TOP */
#define WTIMER_TOP_TOP_DEFAULT                      (_WTIMER_TOP_TOP_DEFAULT << 0) /**< Shifted mode DEFAULT for WTIMER_TOP */

/* Bit fields for WTIMER TOPB */
#define _WTIMER_TOPB_RESETVALUE                     0x00000000UL                     /**< Default value for WTIMER_TOPB */
#define _WTIMER_TOPB_MASK                           0xFFFFFFFFUL                     /**< Mask for WTIMER_TOPB */
#define _WTIMER_TOPB_TOPB_SHIFT                     0                                /**< Shift value for TIMER_TOPB */
#define _WTIMER_TOPB_TOPB_MASK                      0xFFFFFFFFUL                     /**< Bit mask for TIMER_TOPB */
#define _WTIMER_TOPB_TOPB_DEFAULT                   0x00000000UL                     /**< Mode DEFAULT for WTIMER_TOPB */
#define WTIMER_TOPB_TOPB_DEFAULT                    (_WTIMER_TOPB_TOPB_DEFAULT << 0) /**< Shifted mode DEFAULT for WTIMER_TOPB */

/* Bit fields for WTIMER CNT */
#define _WTIMER_CNT_RESETVALUE                      0x00000000UL                   /**< Default value for WTIMER_CNT */
#define _WTIMER_CNT_MASK                            0xFFFFFFFFUL                   /**< Mask for WTIMER_CNT */
#define _WTIMER_CNT_CNT_SHIFT                       0                              /**< Shift value for TIMER_CNT */
#define _WTIMER_CNT_CNT_MASK                        0xFFFFFFFFUL                   /**< Bit mask for TIMER_CNT */
#define _WTIMER_CNT_CNT_DEFAULT                     0x00000000UL                   /**< Mode DEFAULT for WTIMER_CNT */
#define WTIMER_CNT_CNT_DEFAULT                      (_WTIMER_CNT_CNT_DEFAULT << 0) /**< Shifted mode DEFAULT for WTIMER_CNT */

/* Bit fields for WTIMER LOCK */
#define _WTIMER_LOCK_RESETVALUE                     0x00000000UL                              /**< Default value for WTIMER_LOCK */
#define _WTIMER_LOCK_MASK                           0x0000FFFFUL                              /**< Mask for WTIMER_LOCK */
#define _WTIMER_LOCK_TIMERLOCKKEY_SHIFT             0                                         /**< Shift value for TIMER_TIMERLOCKKEY */
#define _WTIMER_LOCK_TIMERLOCKKEY_MASK              0xFFFFUL                                  /**< Bit mask for TIMER_TIMERLOCKKEY */
#define _WTIMER_LOCK_TIMERLOCKKEY_DEFAULT           0x00000000UL                              /**< Mode DEFAULT for WTIMER_LOCK */
#define _WTIMER_LOCK_TIMERLOCKKEY_LOCK              0x00000000UL                              /**< Mode LOCK for WTIMER_LOCK */
#define _WTIMER_LOCK_TIMERLOCKKEY_UNLOCKED          0x00000000UL                              /**< Mode UNLOCKED for WTIMER_LOCK */
#define _WTIMER_LOCK_TIMERLOCKKEY_LOCKED            0x00000001UL                              /**< Mode LOCKED for WTIMER_LOCK */
#define _WTIMER_LOCK_TIMERLOCKKEY_UNLOCK            0x0000CE80UL                              /**< Mode UNLOCK for WTIMER_LOCK */
#define WTIMER_LOCK_TIMERLOCKKEY_DEFAULT            (_WTIMER_LOCK_TIMERLOCKKEY_DEFAULT << 0)  /**< Shifted mode DEFAULT for WTIMER_LOCK */
#define WTIMER_LOCK_TIMERLOCKKEY_LOCK               (_WTIMER_LOCK_TIMERLOCKKEY_LOCK << 0)     /**< Shifted mode LOCK for WTIMER_LOCK */
#define WTIMER_LOCK_TIMERLOCKKEY_UNLOCKED           (_WTIMER_LOCK_TIMERLOCKKEY_UNLOCKED << 0) /**< Shifted mode UNLOCKED for WTIMER_LOCK */
#define WTIMER_LOCK_TIMERLOCKKEY_LOCKED             (_WTIMER_LOCK_TIMERLOCKKEY_LOCKED << 0)   /**< Shifted mode LOCKED for WTIMER_LOCK */
#define WTIMER_LOCK_TIMERLOCKKEY_UNLOCK             (_WTIMER_LOCK_TIMERLOCKKEY_UNLOCK << 0)   /**< Shifted mode UNLOCK for WTIMER_LOCK */

/* Bit fields for WTIMER ROUTEPEN */
#define _WTIMER_ROUTEPEN_RESETVALUE                 0x00000000UL                              /**< Default value for WTIMER_ROUTEPEN */
#define _WTIMER_ROUTEPEN_MASK                       0x0000070FUL                              /**< Mask for WTIMER_ROUTEPEN */
#define WTIMER_ROUTEPEN_CC0PEN                      (0x1UL << 0)                              /**< CC Channel 0 Pin Enable */
#define _WTIMER_ROUTEPEN_CC0PEN_SHIFT               0                                         /**< Shift value for TIMER_CC0PEN */
#define _WTIMER_ROUTEPEN_CC0PEN_MASK                0x1UL                                     /**< Bit mask for TIMER_CC0PEN */
#define _WTIMER_ROUTEPEN_CC0PEN_DEFAULT             0x00000000UL                              /**< Mode DEFAULT for WTIMER_ROUTEPEN */
#define WTIMER_ROUTEPEN_CC0PEN_DEFAULT              (_WTIMER_ROUTEPEN_CC0PEN_DEFAULT << 0)    /**< Shifted mode DEFAULT for WTIMER_ROUTEPEN */
#define WTIMER_ROUTEPEN_CC1PEN                      (0x1UL << 1)                              /**< CC Channel 1 Pin Enable */
#define _WTIMER_ROUTEPEN_CC1PEN_SHIFT               1                                         /**< Shift value for TIMER_CC1PEN */
#define _WTIMER_ROUTEPEN_CC1PEN_MASK                0x2UL                                     /**< Bit mask for TIMER_CC1PEN */
#define _WTIMER_ROUTEPEN_CC1PEN_DEFAULT             0x00000000UL                              /**< Mode DEFAULT for WTIMER_ROUTEPEN */
#define WTIMER_ROUTEPEN_CC1PEN_DEFAULT              (_WTIMER_ROUTEPEN_CC1PEN_DEFAULT << 1)    /**< Shifted mode DEFAULT for WTIMER_ROUTEPEN */
#define WTIMER_ROUTEPEN_CC2PEN                      (0x1UL << 2)                              /**< CC Channel 2 Pin Enable */
#define _WTIMER_ROUTEPEN_CC2PEN_SHIFT               2                                         /**< Shift value for TIMER_CC2PEN */
#define _WTIMER_ROUTEPEN_CC2PEN_MASK                0x4UL                                     /**< Bit mask for TIMER_CC2PEN */
#define _WTIMER_ROUTEPEN_CC2PEN_DEFAULT             0x00000000UL                              /**< Mode DEFAULT for WTIMER_ROUTEPEN */
#define WTIMER_ROUTEPEN_CC2PEN_DEFAULT              (_WTIMER_ROUTEPEN_CC2PEN_DEFAULT << 2)    /**< Shifted mode DEFAULT for WTIMER_ROUTEPEN */
#define WTIMER_ROUTEPEN_CC3PEN                      (0x1UL << 3)                              /**< CC Channel 3 Pin Enable */
#define _WTIMER_ROUTEPEN_CC3PEN_SHIFT               3                                         /**< Shift value for TIMER_CC3PEN */
#define _WTIMER_ROUTEPEN_CC3PEN_MASK                0x8UL                                     /**< Bit mask for TIMER_CC3PEN */
#define _WTIMER_ROUTEPEN_CC3PEN_DEFAULT             0x00000000UL                              /**< Mode DEFAULT for WTIMER_ROUTEPEN */
#define WTIMER_ROUTEPEN_CC3PEN_DEFAULT              (_WTIMER_ROUTEPEN_CC3PEN_DEFAULT << 3)    /**< Shifted mode DEFAULT for WTIMER_ROUTEPEN */
#define WTIMER_ROUTEPEN_CDTI0PEN                    (0x1UL << 8)                              /**< CC Channel 0 Complementary Dead-Time Insertion Pin Enable */
#define _WTIMER_ROUTEPEN_CDTI0PEN_SHIFT             8                                         /**< Shift value for TIMER_CDTI0PEN */
#define _WTIMER_ROUTEPEN_CDTI0PEN_MASK              0x100UL                                   /**< Bit mask for TIMER_CDTI0PEN */
#define _WTIMER_ROUTEPEN_CDTI0PEN_DEFAULT           0x00000000UL                              /**< Mode DEFAULT for WTIMER_ROUTEPEN */
#define WTIMER_ROUTEPEN_CDTI0PEN_DEFAULT            (_WTIMER_ROUTEPEN_CDTI0PEN_DEFAULT << 8)  /**< Shifted mode DEFAULT for WTIMER_ROUTEPEN */
#define WTIMER_ROUTEPEN_CDTI1PEN                    (0x1UL << 9)                              /**< CC Channel 1 Complementary Dead-Time Insertion Pin Enable */
#define _WTIMER_ROUTEPEN_CDTI1PEN_SHIFT             9                                         /**< Shift value for TIMER_CDTI1PEN */
#define _WTIMER_ROUTEPEN_CDTI1PEN_MASK              0x200UL                                   /**< Bit mask for TIMER_CDTI1PEN */
#define _WTIMER_ROUTEPEN_CDTI1PEN_DEFAULT           0x00000000UL                              /**< Mode DEFAULT for WTIMER_ROUTEPEN */
#define WTIMER_ROUTEPEN_CDTI1PEN_DEFAULT            (_WTIMER_ROUTEPEN_CDTI1PEN_DEFAULT << 9)  /**< Shifted mode DEFAULT for WTIMER_ROUTEPEN */
#define WTIMER_ROUTEPEN_CDTI2PEN                    (0x1UL << 10)                             /**< CC Channel 2 Complementary Dead-Time Insertion Pin Enable */
#define _WTIMER_ROUTEPEN_CDTI2PEN_SHIFT             10                                        /**< Shift value for TIMER_CDTI2PEN */
#define _WTIMER_ROUTEPEN_CDTI2PEN_MASK              0x400UL                                   /**< Bit mask for TIMER_CDTI2PEN */
#define _WTIMER_ROUTEPEN_CDTI2PEN_DEFAULT           0x00000000UL                              /**< Mode DEFAULT for WTIMER_ROUTEPEN */
#define WTIMER_ROUTEPEN_CDTI2PEN_DEFAULT            (_WTIMER_ROUTEPEN_CDTI2PEN_DEFAULT << 10) /**< Shifted mode DEFAULT for WTIMER_ROUTEPEN */
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
