shsa5563/Ring-WearTech/Firmware/soc-smartPhone_NoBuff/inc/efr32bg13p_acmp.h

/**************************************************************************//**
 * @file efr32bg13p_acmp.h
 * @brief EFR32BG13P_ACMP register and bit field definitions
 * @version 5.3.2
 ******************************************************************************
 * # License
 * <b>Copyright 2017 Silicon Laboratories, Inc. http://www.silabs.com</b>
 ******************************************************************************
 *
 * Permission is granted to anyone to use this software for any purpose,
 * including commercial applications, and to alter it and redistribute it
 * freely, subject to the following restrictions:
 *
 * 1. The origin of this software must not be misrepresented; you must not
 *    claim that you wrote the original software.@n
 * 2. Altered source versions must be plainly marked as such, and must not be
 *    misrepresented as being the original software.@n
 * 3. This notice may not be removed or altered from any source distribution.
 *
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
 * Silicon Laboratories, Inc. will not be liable for any consequential,
 * incidental, or special damages, or any other relief, or for any claim by
 * any third party, arising from your use of this Software.
 *
 *****************************************************************************/

#if defined(__ICCARM__)
#pragma system_include       /* Treat file as system include file. */
#elif defined(__ARMCC_VERSION) && (__ARMCC_VERSION >= 6010050)
#pragma clang system_header  /* Treat file as system include file. */
#endif

/**************************************************************************//**
* @addtogroup Parts
* @{
******************************************************************************/
/**************************************************************************//**
 * @defgroup EFR32BG13P_ACMP ACMP
 * @{
 * @brief EFR32BG13P_ACMP Register Declaration
 *****************************************************************************/
/** ACMP Register Declaration */
typedef struct {
  __IOM uint32_t CTRL;          /**< Control Register  */
  __IOM uint32_t INPUTSEL;      /**< Input Selection Register  */
  __IM uint32_t  STATUS;        /**< Status Register  */
  __IM uint32_t  IF;            /**< Interrupt Flag Register  */
  __IOM uint32_t IFS;           /**< Interrupt Flag Set Register  */
  __IOM uint32_t IFC;           /**< Interrupt Flag Clear Register  */
  __IOM uint32_t IEN;           /**< Interrupt Enable Register  */
  uint32_t       RESERVED0[1];  /**< Reserved for future use **/
  __IM uint32_t  APORTREQ;      /**< APORT Request Status Register  */
  __IM uint32_t  APORTCONFLICT; /**< APORT Conflict Status Register  */
  __IOM uint32_t HYSTERESIS0;   /**< Hysteresis 0 Register  */
  __IOM uint32_t HYSTERESIS1;   /**< Hysteresis 1 Register  */

  uint32_t       RESERVED1[4];  /**< Reserved for future use **/
  __IOM uint32_t ROUTEPEN;      /**< I/O Routing Pine Enable Register  */
  __IOM uint32_t ROUTELOC0;     /**< I/O Routing Location Register  */
  __IOM uint32_t EXTIFCTRL;     /**< External override interface control  */
} ACMP_TypeDef;                 /** @} */

/**************************************************************************//**
 * @addtogroup EFR32BG13P_ACMP
 * @{
 * @defgroup EFR32BG13P_ACMP_BitFields  ACMP Bit Fields
 * @{
 *****************************************************************************/

/* Bit fields for ACMP CTRL */
#define _ACMP_CTRL_RESETVALUE                          0x07000000UL                               /**< Default value for ACMP_CTRL */
#define _ACMP_CTRL_MASK                                0xBF3CF70DUL                               /**< Mask for ACMP_CTRL */
#define ACMP_CTRL_EN                                   (0x1UL << 0)                               /**< Analog Comparator Enable */
#define _ACMP_CTRL_EN_SHIFT                            0                                          /**< Shift value for ACMP_EN */
#define _ACMP_CTRL_EN_MASK                             0x1UL                                      /**< Bit mask for ACMP_EN */
#define _ACMP_CTRL_EN_DEFAULT                          0x00000000UL                               /**< Mode DEFAULT for ACMP_CTRL */
#define ACMP_CTRL_EN_DEFAULT                           (_ACMP_CTRL_EN_DEFAULT << 0)               /**< Shifted mode DEFAULT for ACMP_CTRL */
#define ACMP_CTRL_INACTVAL                             (0x1UL << 2)                               /**< Inactive Value */
#define _ACMP_CTRL_INACTVAL_SHIFT                      2                                          /**< Shift value for ACMP_INACTVAL */
#define _ACMP_CTRL_INACTVAL_MASK                       0x4UL                                      /**< Bit mask for ACMP_INACTVAL */
#define _ACMP_CTRL_INACTVAL_DEFAULT                    0x00000000UL                               /**< Mode DEFAULT for ACMP_CTRL */
#define _ACMP_CTRL_INACTVAL_LOW                        0x00000000UL                               /**< Mode LOW for ACMP_CTRL */
#define _ACMP_CTRL_INACTVAL_HIGH                       0x00000001UL                               /**< Mode HIGH for ACMP_CTRL */
#define ACMP_CTRL_INACTVAL_DEFAULT                     (_ACMP_CTRL_INACTVAL_DEFAULT << 2)         /**< Shifted mode DEFAULT for ACMP_CTRL */
#define ACMP_CTRL_INACTVAL_LOW                         (_ACMP_CTRL_INACTVAL_LOW << 2)             /**< Shifted mode LOW for ACMP_CTRL */
#define ACMP_CTRL_INACTVAL_HIGH                        (_ACMP_CTRL_INACTVAL_HIGH << 2)            /**< Shifted mode HIGH for ACMP_CTRL */
#define ACMP_CTRL_GPIOINV                              (0x1UL << 3)                               /**< Comparator GPIO Output Invert */
#define _ACMP_CTRL_GPIOINV_SHIFT                       3                                          /**< Shift value for ACMP_GPIOINV */
#define _ACMP_CTRL_GPIOINV_MASK                        0x8UL                                      /**< Bit mask for ACMP_GPIOINV */
#define _ACMP_CTRL_GPIOINV_DEFAULT                     0x00000000UL                               /**< Mode DEFAULT for ACMP_CTRL */
#define _ACMP_CTRL_GPIOINV_NOTINV                      0x00000000UL                               /**< Mode NOTINV for ACMP_CTRL */
#define _ACMP_CTRL_GPIOINV_INV                         0x00000001UL                               /**< Mode INV for ACMP_CTRL */
#define ACMP_CTRL_GPIOINV_DEFAULT                      (_ACMP_CTRL_GPIOINV_DEFAULT << 3)          /**< Shifted mode DEFAULT for ACMP_CTRL */
#define ACMP_CTRL_GPIOINV_NOTINV                       (_ACMP_CTRL_GPIOINV_NOTINV << 3)           /**< Shifted mode NOTINV for ACMP_CTRL */
#define ACMP_CTRL_GPIOINV_INV                          (_ACMP_CTRL_GPIOINV_INV << 3)              /**< Shifted mode INV for ACMP_CTRL */
#define ACMP_CTRL_APORTXMASTERDIS                      (0x1UL << 8)                               /**< APORT Bus X Master Disable */
#define _ACMP_CTRL_APORTXMASTERDIS_SHIFT               8                                          /**< Shift value for ACMP_APORTXMASTERDIS */
#define _ACMP_CTRL_APORTXMASTERDIS_MASK                0x100UL                                    /**< Bit mask for ACMP_APORTXMASTERDIS */
#define _ACMP_CTRL_APORTXMASTERDIS_DEFAULT             0x00000000UL                               /**< Mode DEFAULT for ACMP_CTRL */
#define ACMP_CTRL_APORTXMASTERDIS_DEFAULT              (_ACMP_CTRL_APORTXMASTERDIS_DEFAULT << 8)  /**< Shifted mode DEFAULT for ACMP_CTRL */
#define ACMP_CTRL_APORTYMASTERDIS                      (0x1UL << 9)                               /**< APORT Bus Y Master Disable */
#define _ACMP_CTRL_APORTYMASTERDIS_SHIFT               9                                          /**< Shift value for ACMP_APORTYMASTERDIS */
#define _ACMP_CTRL_APORTYMASTERDIS_MASK                0x200UL                                    /**< Bit mask for ACMP_APORTYMASTERDIS */
#define _ACMP_CTRL_APORTYMASTERDIS_DEFAULT             0x00000000UL                               /**< Mode DEFAULT for ACMP_CTRL */
#define ACMP_CTRL_APORTYMASTERDIS_DEFAULT              (_ACMP_CTRL_APORTYMASTERDIS_DEFAULT << 9)  /**< Shifted mode DEFAULT for ACMP_CTRL */
#define ACMP_CTRL_APORTVMASTERDIS                      (0x1UL << 10)                              /**< APORT Bus Master Disable for Bus selected by VASEL */
#define _ACMP_CTRL_APORTVMASTERDIS_SHIFT               10                                         /**< Shift value for ACMP_APORTVMASTERDIS */
#define _ACMP_CTRL_APORTVMASTERDIS_MASK                0x400UL                                    /**< Bit mask for ACMP_APORTVMASTERDIS */
#define _ACMP_CTRL_APORTVMASTERDIS_DEFAULT             0x00000000UL                               /**< Mode DEFAULT for ACMP_CTRL */
#define ACMP_CTRL_APORTVMASTERDIS_DEFAULT              (_ACMP_CTRL_APORTVMASTERDIS_DEFAULT << 10) /**< Shifted mode DEFAULT for ACMP_CTRL */
#define _ACMP_CTRL_PWRSEL_SHIFT                        12                                         /**< Shift value for ACMP_PWRSEL */
#define _ACMP_CTRL_PWRSEL_MASK                         0x7000UL                                   /**< Bit mask for ACMP_PWRSEL */
#define _ACMP_CTRL_PWRSEL_DEFAULT                      0x00000000UL                               /**< Mode DEFAULT for ACMP_CTRL */
#define _ACMP_CTRL_PWRSEL_AVDD                         0x00000000UL                               /**< Mode AVDD for ACMP_CTRL */
#define _ACMP_CTRL_PWRSEL_VREGVDD                      0x00000001UL                               /**< Mode VREGVDD for ACMP_CTRL */
#define _ACMP_CTRL_PWRSEL_IOVDD0                       0x00000002UL                               /**< Mode IOVDD0 for ACMP_CTRL */
#define _ACMP_CTRL_PWRSEL_IOVDD1                       0x00000004UL                               /**< Mode IOVDD1 for ACMP_CTRL */
#define ACMP_CTRL_PWRSEL_DEFAULT                       (_ACMP_CTRL_PWRSEL_DEFAULT << 12)          /**< Shifted mode DEFAULT for ACMP_CTRL */
#define ACMP_CTRL_PWRSEL_AVDD                          (_ACMP_CTRL_PWRSEL_AVDD << 12)             /**< Shifted mode AVDD for ACMP_CTRL */
#define ACMP_CTRL_PWRSEL_VREGVDD                       (_ACMP_CTRL_PWRSEL_VREGVDD << 12)          /**< Shifted mode VREGVDD for ACMP_CTRL */
#define ACMP_CTRL_PWRSEL_IOVDD0                        (_ACMP_CTRL_PWRSEL_IOVDD0 << 12)           /**< Shifted mode IOVDD0 for ACMP_CTRL */
#define ACMP_CTRL_PWRSEL_IOVDD1                        (_ACMP_CTRL_PWRSEL_IOVDD1 << 12)           /**< Shifted mode IOVDD1 for ACMP_CTRL */
#define ACMP_CTRL_ACCURACY                             (0x1UL << 15)                              /**< ACMP accuracy mode */
#define _ACMP_CTRL_ACCURACY_SHIFT                      15                                         /**< Shift value for ACMP_ACCURACY */
#define _ACMP_CTRL_ACCURACY_MASK                       0x8000UL                                   /**< Bit mask for ACMP_ACCURACY */
#define _ACMP_CTRL_ACCURACY_DEFAULT                    0x00000000UL                               /**< Mode DEFAULT for ACMP_CTRL */
#define _ACMP_CTRL_ACCURACY_LOW                        0x00000000UL                               /**< Mode LOW for ACMP_CTRL */
#define _ACMP_CTRL_ACCURACY_HIGH                       0x00000001UL                               /**< Mode HIGH for ACMP_CTRL */
#define ACMP_CTRL_ACCURACY_DEFAULT                     (_ACMP_CTRL_ACCURACY_DEFAULT << 15)        /**< Shifted mode DEFAULT for ACMP_CTRL */
#define ACMP_CTRL_ACCURACY_LOW                         (_ACMP_CTRL_ACCURACY_LOW << 15)            /**< Shifted mode LOW for ACMP_CTRL */
#define ACMP_CTRL_ACCURACY_HIGH                        (_ACMP_CTRL_ACCURACY_HIGH << 15)           /**< Shifted mode HIGH for ACMP_CTRL */
#define _ACMP_CTRL_INPUTRANGE_SHIFT                    18                                         /**< Shift value for ACMP_INPUTRANGE */
#define _ACMP_CTRL_INPUTRANGE_MASK                     0xC0000UL                                  /**< Bit mask for ACMP_INPUTRANGE */
#define _ACMP_CTRL_INPUTRANGE_DEFAULT                  0x00000000UL                               /**< Mode DEFAULT for ACMP_CTRL */
#define _ACMP_CTRL_INPUTRANGE_FULL                     0x00000000UL                               /**< Mode FULL for ACMP_CTRL */
#define _ACMP_CTRL_INPUTRANGE_GTVDDDIV2                0x00000001UL                               /**< Mode GTVDDDIV2 for ACMP_CTRL */
#define _ACMP_CTRL_INPUTRANGE_LTVDDDIV2                0x00000002UL                               /**< Mode LTVDDDIV2 for ACMP_CTRL */
#define ACMP_CTRL_INPUTRANGE_DEFAULT                   (_ACMP_CTRL_INPUTRANGE_DEFAULT << 18)      /**< Shifted mode DEFAULT for ACMP_CTRL */
#define ACMP_CTRL_INPUTRANGE_FULL                      (_ACMP_CTRL_INPUTRANGE_FULL << 18)         /**< Shifted mode FULL for ACMP_CTRL */
#define ACMP_CTRL_INPUTRANGE_GTVDDDIV2                 (_ACMP_CTRL_INPUTRANGE_GTVDDDIV2 << 18)    /**< Shifted mode GTVDDDIV2 for ACMP_CTRL */
#define ACMP_CTRL_INPUTRANGE_LTVDDDIV2                 (_ACMP_CTRL_INPUTRANGE_LTVDDDIV2 << 18)    /**< Shifted mode LTVDDDIV2 for ACMP_CTRL */
#define ACMP_CTRL_IRISE                                (0x1UL << 20)                              /**< Rising Edge Interrupt Sense */
#define _ACMP_CTRL_IRISE_SHIFT                         20                                         /**< Shift value for ACMP_IRISE */
#define _ACMP_CTRL_IRISE_MASK                          0x100000UL                                 /**< Bit mask for ACMP_IRISE */
#define _ACMP_CTRL_IRISE_DEFAULT                       0x00000000UL                               /**< Mode DEFAULT for ACMP_CTRL */
#define _ACMP_CTRL_IRISE_DISABLED                      0x00000000UL                               /**< Mode DISABLED for ACMP_CTRL */
#define _ACMP_CTRL_IRISE_ENABLED                       0x00000001UL                               /**< Mode ENABLED for ACMP_CTRL */
#define ACMP_CTRL_IRISE_DEFAULT                        (_ACMP_CTRL_IRISE_DEFAULT << 20)           /**< Shifted mode DEFAULT for ACMP_CTRL */
#define ACMP_CTRL_IRISE_DISABLED                       (_ACMP_CTRL_IRISE_DISABLED << 20)          /**< Shifted mode DISABLED for ACMP_CTRL */
#define ACMP_CTRL_IRISE_ENABLED                        (_ACMP_CTRL_IRISE_ENABLED << 20)           /**< Shifted mode ENABLED for ACMP_CTRL */
#define ACMP_CTRL_IFALL                                (0x1UL << 21)                              /**< Falling Edge Interrupt Sense */
#define _ACMP_CTRL_IFALL_SHIFT                         21                                         /**< Shift value for ACMP_IFALL */
#define _ACMP_CTRL_IFALL_MASK                          0x200000UL                                 /**< Bit mask for ACMP_IFALL */
#define _ACMP_CTRL_IFALL_DEFAULT                       0x00000000UL                               /**< Mode DEFAULT for ACMP_CTRL */
#define _ACMP_CTRL_IFALL_DISABLED                      0x00000000UL                               /**< Mode DISABLED for ACMP_CTRL */
#define _ACMP_CTRL_IFALL_ENABLED                       0x00000001UL                               /**< Mode ENABLED for ACMP_CTRL */
#define ACMP_CTRL_IFALL_DEFAULT                        (_ACMP_CTRL_IFALL_DEFAULT << 21)           /**< Shifted mode DEFAULT for ACMP_CTRL */
#define ACMP_CTRL_IFALL_DISABLED                       (_ACMP_CTRL_IFALL_DISABLED << 21)          /**< Shifted mode DISABLED for ACMP_CTRL */
#define ACMP_CTRL_IFALL_ENABLED                        (_ACMP_CTRL_IFALL_ENABLED << 21)           /**< Shifted mode ENABLED for ACMP_CTRL */
#define _ACMP_CTRL_BIASPROG_SHIFT                      24                                         /**< Shift value for ACMP_BIASPROG */
#define _ACMP_CTRL_BIASPROG_MASK                       0x3F000000UL                               /**< Bit mask for ACMP_BIASPROG */
#define _ACMP_CTRL_BIASPROG_DEFAULT                    0x00000007UL                               /**< Mode DEFAULT for ACMP_CTRL */
#define ACMP_CTRL_BIASPROG_DEFAULT                     (_ACMP_CTRL_BIASPROG_DEFAULT << 24)        /**< Shifted mode DEFAULT for ACMP_CTRL */
#define ACMP_CTRL_FULLBIAS                             (0x1UL << 31)                              /**< Full Bias Current */
#define _ACMP_CTRL_FULLBIAS_SHIFT                      31                                         /**< Shift value for ACMP_FULLBIAS */
#define _ACMP_CTRL_FULLBIAS_MASK                       0x80000000UL                               /**< Bit mask for ACMP_FULLBIAS */
#define _ACMP_CTRL_FULLBIAS_DEFAULT                    0x00000000UL                               /**< Mode DEFAULT for ACMP_CTRL */
#define ACMP_CTRL_FULLBIAS_DEFAULT                     (_ACMP_CTRL_FULLBIAS_DEFAULT << 31)        /**< Shifted mode DEFAULT for ACMP_CTRL */

/* Bit fields for ACMP INPUTSEL */
#define _ACMP_INPUTSEL_RESETVALUE                      0x00000000UL                             /**< Default value for ACMP_INPUTSEL */
#define _ACMP_INPUTSEL_MASK                            0x757FFFFFUL                             /**< Mask for ACMP_INPUTSEL */
#define _ACMP_INPUTSEL_POSSEL_SHIFT                    0                                        /**< Shift value for ACMP_POSSEL */
#define _ACMP_INPUTSEL_POSSEL_MASK                     0xFFUL                                   /**< Bit mask for ACMP_POSSEL */
#define _ACMP_INPUTSEL_POSSEL_DEFAULT                  0x00000000UL                             /**< Mode DEFAULT for ACMP_INPUTSEL */
#define _ACMP_INPUTSEL_POSSEL_APORT0XCH0               0x00000000UL                             /**< Mode APORT0XCH0 for ACMP_INPUTSEL */
#define _ACMP_INPUTSEL_POSSEL_APORT0XCH1               0x00000001UL                             /**< Mode APORT0XCH1 for ACMP_INPUTSEL */
#define _ACMP_INPUTSEL_POSSEL_APORT0XCH2               0x00000002UL                             /**< Mode APORT0XCH2 for ACMP_INPUTSEL */
#define _ACMP_INPUTSEL_POSSEL_APORT0XCH3               0x00000003UL                             /**< Mode APORT0XCH3 for ACMP_INPUTSEL */
#define _ACMP_INPUTSEL_POSSEL_APORT0XCH4               0x00000004UL                             /**< Mode APORT0XCH4 for ACMP_INPUTSEL */
#define _ACMP_INPUTSEL_POSSEL_APORT0XCH5               0x00000005UL                             /**< Mode APORT0XCH5 for ACMP_INPUTSEL */
#define _ACMP_INPUTSEL_POSSEL_APORT0XCH6               0x00000006UL                             /**< Mode APORT0XCH6 for ACMP_INPUTSEL */
#define _ACMP_INPUTSEL_POSSEL_APORT0XCH7               0x00000007UL                             /**< Mode APORT0XCH7 for ACMP_INPUTSEL */
#define _ACMP_INPUTSEL_POSSEL_APORT0XCH8               0x00000008UL                             /**< Mode APORT0XCH8 for ACMP_INPUTSEL */
#define _ACMP_INPUTSEL_POSSEL_APORT0XCH9               0x00000009UL                             /**< Mode APORT0XCH9 for ACMP_INPUTSEL */
#define _ACMP_INPUTSEL_POSSEL_APORT0XCH10              0x0000000AUL                             /**< Mode APORT0XCH10 for ACMP_INPUTSEL */
#define _ACMP_INPUTSEL_POSSEL_APORT0XCH11              0x0000000BUL                             /**< Mode APORT0XCH11 for ACMP_INPUTSEL */
#define _ACMP_INPUTSEL_POSSEL_APORT0XCH12              0x0000000CUL                             /**< Mode APORT0XCH12 for ACMP_INPUTSEL */
#define _ACMP_INPUTSEL_POSSEL_APORT0XCH13              0x0000000DUL                             /**< Mode APORT0XCH13 for ACMP_INPUTSEL */
#define _ACMP_INPUTSEL_POSSEL_APORT0XCH14              0x0000000EUL                             /**< Mode APORT0XCH14 for ACMP_INPUTSEL */
#define _ACMP_INPUTSEL_POSSEL_APORT0XCH15              0x0000000FUL                             /**< Mode APORT0XCH15 for ACMP_INPUTSEL */
#define _ACMP_INPUTSEL_POSSEL_APORT0YCH0               0x00000010UL                             /**< Mode APORT0YCH0 for ACMP_INPUTSEL */
#define _ACMP_INPUTSEL_POSSEL_APORT0YCH1               0x00000011UL                             /**< Mode APORT0YCH1 for ACMP_INPUTSEL */
#define _ACMP_INPUTSEL_POSSEL_APORT0YCH2               0x00000012UL                             /**< Mode APORT0YCH2 for ACMP_INPUTSEL */
#define _ACMP_INPUTSEL_POSSEL_APORT0YCH3               0x00000013UL                             /**< Mode APORT0YCH3 for ACMP_INPUTSEL */
#define _ACMP_INPUTSEL_POSSEL_APORT0YCH4               0x00000014UL                             /**< Mode APORT0YCH4 for ACMP_INPUTSEL */
#define _ACMP_INPUTSEL_POSSEL_APORT0YCH5               0x00000015UL                             /**< Mode APORT0YCH5 for ACMP_INPUTSEL */
#define _ACMP_INPUTSEL_POSSEL_APORT0YCH6               0x00000016UL                             /**< Mode APORT0YCH6 for ACMP_INPUTSEL */
#define _ACMP_INPUTSEL_POSSEL_APORT0YCH7               0x00000017UL                             /**< Mode APORT0YCH7 for ACMP_INPUTSEL */
#define _ACMP_INPUTSEL_POSSEL_APORT0YCH8               0x00000018UL                             /**< Mode APORT0YCH8 for ACMP_INPUTSEL */
#define _ACMP_INPUTSEL_POSSEL_APORT0YCH9               0x00000019UL                             /**< Mode APORT0YCH9 for ACMP_INPUTSEL */
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
#define _ACMP_INPUTSEL_POSSEL_APORT1XCH24              0x00000038UL                             /**< Mode APORT1XCH24 for ACMP_INPUTSEL */
#define _ACMP_INPUTSEL_POSSEL_APORT1YCH25              0x00000039UL                             /**< Mode APORT1YCH25 for ACMP_INPUTSEL */
#define _ACMP_INPUTSEL_POSSEL_APORT1XCH26              0x0000003AUL                             /**< Mode APORT1XCH26 for ACMP_INPUTSEL */
#define _ACMP_INPUTSEL_POSSEL_APORT1YCH27              0x0000003BUL                             /**< Mode APORT1YCH27 for ACMP_INPUTSEL */
#define _ACMP_INPUTSEL_POSSEL_APORT1XCH28              0x0000003CUL                             /**< Mode APORT1XCH28 for ACMP_INPUTSEL */
#define _ACMP_INPUTSEL_POSSEL_APORT1YCH29              0x0000003DUL                             /**< Mode APORT1YCH29 for ACMP_INPUTSEL */
#define _ACMP_INPUTSEL_POSSEL_APORT1XCH30              0x0000003EUL                             /**< Mode APORT1XCH30 for ACMP_INPUTSEL */
#define _ACMP_INPUTSEL_POSSEL_APORT1YCH31              0x0000003FUL                             /**< Mode APORT1YCH31 for ACMP_INPUTSEL */
#define _ACMP_INPUTSEL_POSSEL_APORT2YCH0               0x00000040UL                             /**< Mode APORT2YCH0 for ACMP_INPUTSEL */
#define _ACMP_INPUTSEL_POSSEL_APORT2XCH1               0x00000041UL                             /**< Mode APORT2XCH1 for ACMP_INPUTSEL */
#define _ACMP_INPUTSEL_POSSEL_APORT2YCH2               0x00000042UL                             /**< Mode APORT2YCH2 for ACMP_INPUTSEL */
#define _ACMP_INPUTSEL_POSSEL_APORT2XCH3               0x00000043UL                             /**< Mode APORT2XCH3 for ACMP_INPUTSEL */
#define _ACMP_INPUTSEL_POSSEL_APORT2YCH4               0x00000044UL                             /**< Mode APORT2YCH4 for ACMP_INPUTSEL */
#define _ACMP_INPUTSEL_POSSEL_APORT2XCH5               0x00000045UL                             /**< Mode APORT2XCH5 for ACMP_INPUTSEL */
#define _ACMP_INPUTSEL_POSSEL_APORT2YCH6               0x00000046UL                             /**< Mode APORT2YCH6 for ACMP_INPUTSEL */
#define _ACMP_INPUTSEL_POSSEL_APORT2XCH7               0x00000047UL                             /**< Mode APORT2XCH7 for ACMP_INPUTSEL */
#define _ACMP_INPUTSEL_POSSEL_APORT2YCH8               0x00000048UL                             /**< Mode APORT2YCH8 for ACMP_INPUTSEL */
#define _ACMP_INPUTSEL_POSSEL_APORT2XCH9               0x00000049UL                             /**< Mode APORT2XCH9 for ACMP_INPUTSEL */
#define _ACMP_INPUTSEL_POSSEL_APORT2YCH10              0x0000004AUL                             /**< Mode APORT2YCH10 for ACMP_INPUTSEL */
#define _ACMP_INPUTSEL_POSSEL_APORT2XCH11              0x0000004BUL                             /**< Mode APORT2XCH11 for ACMP_INPUTSEL */
#define _ACMP_INPUTSEL_POSSEL_APORT2YCH12              0x0000004CUL                             /**< Mode APORT2YCH12 for ACMP_INPUTSEL */
#define _ACMP_INPUTSEL_POSSEL_APORT2XCH13              0x0000004DUL                             /**< Mode APORT2XCH13 for ACMP_INPUTSEL */
#define _ACMP_INPUTSEL_POSSEL_APORT2YCH14              0x0000004EUL                             /**< Mode APORT2YCH14 for ACMP_INPUTSEL */
#define _ACMP_INPUTSEL_POSSEL_APORT2XCH15              0x0000004FUL                             /**< Mode APORT2XCH15 for ACMP_INPUTSEL */
#define _ACMP_INPUTSEL_POSSEL_APORT2YCH16              0x00000050UL                             /**< Mode APORT2YCH16 for ACMP_INPUTSEL */
#define _ACMP_INPUTSEL_POSSEL_APORT2XCH17              0x00000051UL                             /**< Mode APORT2XCH17 for ACMP_INPUTSEL */
#define _ACMP_INPUTSEL_POSSEL_APORT2YCH18              0x00000052UL                             /**< Mode APORT2YCH18 for ACMP_INPUTSEL */
#define _ACMP_INPUTSEL_POSSEL_APORT2XCH19              0x00000053UL                             /**< Mode APORT2XCH19 for ACMP_INPUTSEL */
#define _ACMP_INPUTSEL_POSSEL_APORT2YCH20              0x00000054UL                             /**< Mode APORT2YCH20 for ACMP_INPUTSEL */
#define _ACMP_INPUTSEL_POSSEL_APORT2XCH21              0x00000055UL                             /**< Mode APORT2XCH21 for ACMP_INPUTSEL */
#define _ACMP_INPUTSEL_POSSEL_APORT2YCH22              0x00000056UL                             /**< Mode APORT2YCH22 for ACMP_INPUTSEL */
#define _ACMP_INPUTSEL_POSSEL_APORT2XCH23              0x00000057UL                             /**< Mode APORT2XCH23 for ACMP_INPUTSEL */
#define _ACMP_INPUTSEL_POSSEL_APORT2YCH24              0x00000058UL                             /**< Mode APORT2YCH24 for ACMP_INPUTSEL */
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
#define _ACMP_INPUTSEL_POSSEL_APORT3YCH23              0x00000077UL                             /**< Mode APORT3YCH23 for ACMP_INPUTSEL */
#define _ACMP_INPUTSEL_POSSEL_APORT3XCH24              0x00000078UL                             /**< Mode APORT3XCH24 for ACMP_INPUTSEL */
#define _ACMP_INPUTSEL_POSSEL_APORT3YCH25              0x00000079UL                             /**< Mode APORT3YCH25 for ACMP_INPUTSEL */
#define _ACMP_INPUTSEL_POSSEL_APORT3XCH26              0x0000007AUL                             /**< Mode APORT3XCH26 for ACMP_INPUTSEL */
#define _ACMP_INPUTSEL_POSSEL_APORT3YCH27              0x0000007BUL                             /**< Mode APORT3YCH27 for ACMP_INPUTSEL */
#define _ACMP_INPUTSEL_POSSEL_APORT3XCH28              0x0000007CUL                             /**< Mode APORT3XCH28 for ACMP_INPUTSEL */
#define _ACMP_INPUTSEL_POSSEL_APORT3YCH29              0x0000007DUL                             /**< Mode APORT3YCH29 for ACMP_INPUTSEL */
#define _ACMP_INPUTSEL_POSSEL_APORT3XCH30              0x0000007EUL                             /**< Mode APORT3XCH30 for ACMP_INPUTSEL */
#define _ACMP_INPUTSEL_POSSEL_APORT3YCH31              0x0000007FUL                             /**< Mode APORT3YCH31 for ACMP_INPUTSEL */
#define _ACMP_INPUTSEL_POSSEL_APORT4YCH0               0x00000080UL                             /**< Mode APORT4YCH0 for ACMP_INPUTSEL */
#define _ACMP_INPUTSEL_POSSEL_APORT4XCH1               0x00000081UL                             /**< Mode APORT4XCH1 for ACMP_INPUTSEL */
#define _ACMP_INPUTSEL_POSSEL_APORT4YCH2               0x00000082UL                             /**< Mode APORT4YCH2 for ACMP_INPUTSEL */
#define _ACMP_INPUTSEL_POSSEL_APORT4XCH3               0x00000083UL                             /**< Mode APORT4XCH3 for ACMP_INPUTSEL */
#define _ACMP_INPUTSEL_POSSEL_APORT4YCH4               0x00000084UL                             /**< Mode APORT4YCH4 for ACMP_INPUTSEL */
#define _ACMP_INPUTSEL_POSSEL_APORT4XCH5               0x00000085UL                             /**< Mode APORT4XCH5 for ACMP_INPUTSEL */
#define _ACMP_INPUTSEL_POSSEL_APORT4YCH6               0x00000086UL                             /**< Mode APORT4YCH6 for ACMP_INPUTSEL */
#define _ACMP_INPUTSEL_POSSEL_APORT4XCH7               0x00000087UL                             /**< Mode APORT4XCH7 for ACMP_INPUTSEL */
#define _ACMP_INPUTSEL_POSSEL_APORT4YCH8               0x00000088UL                             /**< Mode APORT4YCH8 for ACMP_INPUTSEL */
#define _ACMP_INPUTSEL_POSSEL_APORT4XCH9               0x00000089UL                             /**< Mode APORT4XCH9 for ACMP_INPUTSEL */
#define _ACMP_INPUTSEL_POSSEL_APORT4YCH10              0x0000008AUL                             /**< Mode APORT4YCH10 for ACMP_INPUTSEL */
#define _ACMP_INPUTSEL_POSSEL_APORT4XCH11              0x0000008BUL                             /**< Mode APORT4XCH11 for ACMP_INPUTSEL */
#define _ACMP_INPUTSEL_POSSEL_APORT4YCH12              0x0000008CUL                             /**< Mode APORT4YCH12 for ACMP_INPUTSEL */
#define _ACMP_INPUTSEL_POSSEL_APORT4XCH13              0x0000008DUL                             /**< Mode APORT4XCH13 for ACMP_INPUTSEL */
#define _ACMP_INPUTSEL_POSSEL_APORT4YCH16              0x00000090UL                             /**< Mode APORT4YCH16 for ACMP_INPUTSEL */
#define _ACMP_INPUTSEL_POSSEL_APORT4XCH17              0x00000091UL                             /**< Mode APORT4XCH17 for ACMP_INPUTSEL */
#define _ACMP_INPUTSEL_POSSEL_APORT4YCH18              0x00000092UL                             /**< Mode APORT4YCH18 for ACMP_INPUTSEL */
#define _ACMP_INPUTSEL_POSSEL_APORT4XCH19              0x00000093UL                             /**< Mode APORT4XCH19 for ACMP_INPUTSEL */
#define _ACMP_INPUTSEL_POSSEL_APORT4YCH20              0x00000094UL                             /**< Mode APORT4YCH20 for ACMP_INPUTSEL */
#define _ACMP_INPUTSEL_POSSEL_APORT4XCH21              0x00000095UL                             /**< Mode APORT4XCH21 for ACMP_INPUTSEL */
#define _ACMP_INPUTSEL_POSSEL_APORT4YCH22              0x00000096UL                             /**< Mode APORT4YCH22 for ACMP_INPUTSEL */
#define _ACMP_INPUTSEL_POSSEL_APORT4XCH23              0x00000097UL                             /**< Mode APORT4XCH23 for ACMP_INPUTSEL */
#define _ACMP_INPUTSEL_POSSEL_APORT4YCH24              0x00000098UL                             /**< Mode APORT4YCH24 for ACMP_INPUTSEL */
#define _ACMP_INPUTSEL_POSSEL_APORT4XCH25              0x00000099UL                             /**< Mode APORT4XCH25 for ACMP_INPUTSEL */
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
#define ACMP_INPUTSEL_POSSEL_APORT1YCH21               (_ACMP_INPUTSEL_POSSEL_APORT1YCH21 << 0) /**< Shifted mode APORT1YCH21 for ACMP_INPUTSEL */
#define ACMP_INPUTSEL_POSSEL_APORT1XCH22               (_ACMP_INPUTSEL_POSSEL_APORT1XCH22 << 0) /**< Shifted mode APORT1XCH22 for ACMP_INPUTSEL */
#define ACMP_INPUTSEL_POSSEL_APORT1YCH23               (_ACMP_INPUTSEL_POSSEL_APORT1YCH23 << 0) /**< Shifted mode APORT1YCH23 for ACMP_INPUTSEL */
#define ACMP_INPUTSEL_POSSEL_APORT1XCH24               (_ACMP_INPUTSEL_POSSEL_APORT1XCH24 << 0) /**< Shifted mode APORT1XCH24 for ACMP_INPUTSEL */
#define ACMP_INPUTSEL_POSSEL_APORT1YCH25               (_ACMP_INPUTSEL_POSSEL_APORT1YCH25 << 0) /**< Shifted mode APORT1YCH25 for ACMP_INPUTSEL */
#define ACMP_INPUTSEL_POSSEL_APORT1XCH26               (_ACMP_INPUTSEL_POSSEL_APORT1XCH26 << 0) /**< Shifted mode APORT1XCH26 for ACMP_INPUTSEL */
#define ACMP_INPUTSEL_POSSEL_APORT1YCH27               (_ACMP_INPUTSEL_POSSEL_APORT1YCH27 << 0) /**< Shifted mode APORT1YCH27 for ACMP_INPUTSEL */
#define ACMP_INPUTSEL_POSSEL_APORT1XCH28               (_ACMP_INPUTSEL_POSSEL_APORT1XCH28 << 0) /**< Shifted mode APORT1XCH28 for ACMP_INPUTSEL */
#define ACMP_INPUTSEL_POSSEL_APORT1YCH29               (_ACMP_INPUTSEL_POSSEL_APORT1YCH29 << 0) /**< Shifted mode APORT1YCH29 for ACMP_INPUTSEL */
#define ACMP_INPUTSEL_POSSEL_APORT1XCH30               (_ACMP_INPUTSEL_POSSEL_APORT1XCH30 << 0) /**< Shifted mode APORT1XCH30 for ACMP_INPUTSEL */
#define ACMP_INPUTSEL_POSSEL_APORT1YCH31               (_ACMP_INPUTSEL_POSSEL_APORT1YCH31 << 0) /**< Shifted mode APORT1YCH31 for ACMP_INPUTSEL */
#define ACMP_INPUTSEL_POSSEL_APORT2YCH0                (_ACMP_INPUTSEL_POSSEL_APORT2YCH0 << 0)  /**< Shifted mode APORT2YCH0 for ACMP_INPUTSEL */
#define ACMP_INPUTSEL_POSSEL_APORT2XCH1                (_ACMP_INPUTSEL_POSSEL_APORT2XCH1 << 0)  /**< Shifted mode APORT2XCH1 for ACMP_INPUTSEL */
#define ACMP_INPUTSEL_POSSEL_APORT2YCH2                (_ACMP_INPUTSEL_POSSEL_APORT2YCH2 << 0)  /**< Shifted mode APORT2YCH2 for ACMP_INPUTSEL */
#define ACMP_INPUTSEL_POSSEL_APORT2XCH3                (_ACMP_INPUTSEL_POSSEL_APORT2XCH3 << 0)  /**< Shifted mode APORT2XCH3 for ACMP_INPUTSEL */
#define ACMP_INPUTSEL_POSSEL_APORT2YCH4                (_ACMP_INPUTSEL_POSSEL_APORT2YCH4 << 0)  /**< Shifted mode APORT2YCH4 for ACMP_INPUTSEL */
#define ACMP_INPUTSEL_POSSEL_APORT2XCH5                (_ACMP_INPUTSEL_POSSEL_APORT2XCH5 << 0)  /**< Shifted mode APORT2XCH5 for ACMP_INPUTSEL */
#define ACMP_INPUTSEL_POSSEL_APORT2YCH6                (_ACMP_INPUTSEL_POSSEL_APORT2YCH6 << 0)  /**< Shifted mode APORT2YCH6 for ACMP_INPUTSEL */
#define ACMP_INPUTSEL_POSSEL_APORT2XCH7                (_ACMP_INPUTSEL_POSSEL_APORT2XCH7 << 0)  /**< Shifted mode APORT2XCH7 for ACMP_INPUTSEL */
#define ACMP_INPUTSEL_POSSEL_APORT2YCH8                (_ACMP_INPUTSEL_POSSEL_APORT2YCH8 << 0)  /**< Shifted mode APORT2YCH8 for ACMP_INPUTSEL */
#define ACMP_INPUTSEL_POSSEL_APORT2XCH9                (_ACMP_INPUTSEL_POSSEL_APORT2XCH9 << 0)  /**< Shifted mode APORT2XCH9 for ACMP_INPUTSEL */
#define ACMP_INPUTSEL_POSSEL_APORT2YCH10               (_ACMP_INPUTSEL_POSSEL_APORT2YCH10 << 0) /**< Shifted mode APORT2YCH10 for ACMP_INPUTSEL */
#define ACMP_INPUTSEL_POSSEL_APORT2XCH11               (_ACMP_INPUTSEL_POSSEL_APORT2XCH11 << 0) /**< Shifted mode APORT2XCH11 for ACMP_INPUTSEL */
#define ACMP_INPUTSEL_POSSEL_APORT2YCH12               (_ACMP_INPUTSEL_POSSEL_APORT2YCH12 << 0) /**< Shifted mode APORT2YCH12 for ACMP_INPUTSEL */
#define ACMP_INPUTSEL_POSSEL_APORT2XCH13               (_ACMP_INPUTSEL_POSSEL_APORT2XCH13 << 0) /**< Shifted mode APORT2XCH13 for ACMP_INPUTSEL */
#define ACMP_INPUTSEL_POSSEL_APORT2YCH14               (_ACMP_INPUTSEL_POSSEL_APORT2YCH14 << 0) /**< Shifted mode APORT2YCH14 for ACMP_INPUTSEL */
#define ACMP_INPUTSEL_POSSEL_APORT2XCH15               (_ACMP_INPUTSEL_POSSEL_APORT2XCH15 << 0) /**< Shifted mode APORT2XCH15 for ACMP_INPUTSEL */
#define ACMP_INPUTSEL_POSSEL_APORT2YCH16               (_ACMP_INPUTSEL_POSSEL_APORT2YCH16 << 0) /**< Shifted mode APORT2YCH16 for ACMP_INPUTSEL */
#define ACMP_INPUTSEL_POSSEL_APORT2XCH17               (_ACMP_INPUTSEL_POSSEL_APORT2XCH17 << 0) /**< Shifted mode APORT2XCH17 for ACMP_INPUTSEL */
#define ACMP_INPUTSEL_POSSEL_APORT2YCH18               (_ACMP_INPUTSEL_POSSEL_APORT2YCH18 << 0) /**< Shifted mode APORT2YCH18 for ACMP_INPUTSEL */
#define ACMP_INPUTSEL_POSSEL_APORT2XCH19               (_ACMP_INPUTSEL_POSSEL_APORT2XCH19 << 0) /**< Shifted mode APORT2XCH19 for ACMP_INPUTSEL */
#define ACMP_INPUTSEL_POSSEL_APORT2YCH20               (_ACMP_INPUTSEL_POSSEL_APORT2YCH20 << 0) /**< Shifted mode APORT2YCH20 for ACMP_INPUTSEL */
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
#define ACMP_INPUTSEL_POSSEL_APORT4XCH27               (_ACMP_INPUTSEL_POSSEL_APORT4XCH27 << 0) /**< Shifted mode APORT4XCH27 for ACMP_INPUTSEL */
#define ACMP_INPUTSEL_POSSEL_APORT4YCH28               (_ACMP_INPUTSEL_POSSEL_APORT4YCH28 << 0) /**< Shifted mode APORT4YCH28 for ACMP_INPUTSEL */
#define ACMP_INPUTSEL_POSSEL_APORT4XCH29               (_ACMP_INPUTSEL_POSSEL_APORT4XCH29 << 0) /**< Shifted mode APORT4XCH29 for ACMP_INPUTSEL */
#define ACMP_INPUTSEL_POSSEL_APORT4YCH30               (_ACMP_INPUTSEL_POSSEL_APORT4YCH30 << 0) /**< Shifted mode APORT4YCH30 for ACMP_INPUTSEL */
#define ACMP_INPUTSEL_POSSEL_APORT4YCH14               (_ACMP_INPUTSEL_POSSEL_APORT4YCH14 << 0) /**< Shifted mode APORT4YCH14 for ACMP_INPUTSEL */
#define ACMP_INPUTSEL_POSSEL_APORT4XCH15               (_ACMP_INPUTSEL_POSSEL_APORT4XCH15 << 0) /**< Shifted mode APORT4XCH15 for ACMP_INPUTSEL */
#define ACMP_INPUTSEL_POSSEL_APORT4XCH31               (_ACMP_INPUTSEL_POSSEL_APORT4XCH31 << 0) /**< Shifted mode APORT4XCH31 for ACMP_INPUTSEL */
#define ACMP_INPUTSEL_POSSEL_DACOUT0                   (_ACMP_INPUTSEL_POSSEL_DACOUT0 << 0)     /**< Shifted mode DACOUT0 for ACMP_INPUTSEL */
#define ACMP_INPUTSEL_POSSEL_DACOUT1                   (_ACMP_INPUTSEL_POSSEL_DACOUT1 << 0)     /**< Shifted mode DACOUT1 for ACMP_INPUTSEL */
#define ACMP_INPUTSEL_POSSEL_VLP                       (_ACMP_INPUTSEL_POSSEL_VLP << 0)         /**< Shifted mode VLP for ACMP_INPUTSEL */
#define ACMP_INPUTSEL_POSSEL_VBDIV                     (_ACMP_INPUTSEL_POSSEL_VBDIV << 0)       /**< Shifted mode VBDIV for ACMP_INPUTSEL */
#define ACMP_INPUTSEL_POSSEL_VADIV                     (_ACMP_INPUTSEL_POSSEL_VADIV << 0)       /**< Shifted mode VADIV for ACMP_INPUTSEL */
#define ACMP_INPUTSEL_POSSEL_VDD                       (_ACMP_INPUTSEL_POSSEL_VDD << 0)         /**< Shifted mode VDD for ACMP_INPUTSEL */
#define ACMP_INPUTSEL_POSSEL_VSS                       (_ACMP_INPUTSEL_POSSEL_VSS << 0)         /**< Shifted mode VSS for ACMP_INPUTSEL */
#define _ACMP_INPUTSEL_NEGSEL_SHIFT                    8                                        /**< Shift value for ACMP_NEGSEL */
#define _ACMP_INPUTSEL_NEGSEL_MASK                     0xFF00UL                                 /**< Bit mask for ACMP_NEGSEL */
#define _ACMP_INPUTSEL_NEGSEL_DEFAULT                  0x00000000UL                             /**< Mode DEFAULT for ACMP_INPUTSEL */
#define _ACMP_INPUTSEL_NEGSEL_APORT0XCH0               0x00000000UL                             /**< Mode APORT0XCH0 for ACMP_INPUTSEL */
#define _ACMP_INPUTSEL_NEGSEL_APORT0XCH1               0x00000001UL                             /**< Mode APORT0XCH1 for ACMP_INPUTSEL */
#define _ACMP_INPUTSEL_NEGSEL_APORT0XCH2               0x00000002UL                             /**< Mode APORT0XCH2 for ACMP_INPUTSEL */
#define _ACMP_INPUTSEL_NEGSEL_APORT0XCH3               0x00000003UL                             /**< Mode APORT0XCH3 for ACMP_INPUTSEL */
#define _ACMP_INPUTSEL_NEGSEL_APORT0XCH4               0x00000004UL                             /**< Mode APORT0XCH4 for ACMP_INPUTSEL */
#define _ACMP_INPUTSEL_NEGSEL_APORT0XCH5               0x00000005UL                             /**< Mode APORT0XCH5 for ACMP_INPUTSEL */
#define _ACMP_INPUTSEL_NEGSEL_APORT0XCH6               0x00000006UL                             /**< Mode APORT0XCH6 for ACMP_INPUTSEL */
#define _ACMP_INPUTSEL_NEGSEL_APORT0XCH7               0x00000007UL                             /**< Mode APORT0XCH7 for ACMP_INPUTSEL */
#define _ACMP_INPUTSEL_NEGSEL_APORT0XCH8               0x00000008UL                             /**< Mode APORT0XCH8 for ACMP_INPUTSEL */
#define _ACMP_INPUTSEL_NEGSEL_APORT0XCH9               0x00000009UL                             /**< Mode APORT0XCH9 for ACMP_INPUTSEL */
#define _ACMP_INPUTSEL_NEGSEL_APORT0XCH10              0x0000000AUL                             /**< Mode APORT0XCH10 for ACMP_INPUTSEL */
#define _ACMP_INPUTSEL_NEGSEL_APORT0XCH11              0x0000000BUL                             /**< Mode APORT0XCH11 for ACMP_INPUTSEL */
#define _ACMP_INPUTSEL_NEGSEL_APORT0XCH12              0x0000000CUL                             /**< Mode APORT0XCH12 for ACMP_INPUTSEL */
#define _ACMP_INPUTSEL_NEGSEL_APORT0XCH13              0x0000000DUL                             /**< Mode APORT0XCH13 for ACMP_INPUTSEL */
#define _ACMP_INPUTSEL_NEGSEL_APORT0XCH14              0x0000000EUL                             /**< Mode APORT0XCH14 for ACMP_INPUTSEL */
#define _ACMP_INPUTSEL_NEGSEL_APORT0XCH15              0x0000000FUL                             /**< Mode APORT0XCH15 for ACMP_INPUTSEL */
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
#define _ACMP_INPUTSEL_NEGSEL_APORT2YCH24              0x00000058UL                             /**< Mode APORT2YCH24 for ACMP_INPUTSEL */
#define _ACMP_INPUTSEL_NEGSEL_APORT2XCH25              0x00000059UL                             /**< Mode APORT2XCH25 for ACMP_INPUTSEL */
#define _ACMP_INPUTSEL_NEGSEL_APORT2YCH26              0x0000005AUL                             /**< Mode APORT2YCH26 for ACMP_INPUTSEL */
#define _ACMP_INPUTSEL_NEGSEL_APORT2XCH27              0x0000005BUL                             /**< Mode APORT2XCH27 for ACMP_INPUTSEL */
#define _ACMP_INPUTSEL_NEGSEL_APORT2YCH28              0x0000005CUL                             /**< Mode APORT2YCH28 for ACMP_INPUTSEL */
#define _ACMP_INPUTSEL_NEGSEL_APORT2XCH29              0x0000005DUL                             /**< Mode APORT2XCH29 for ACMP_INPUTSEL */
#define _ACMP_INPUTSEL_NEGSEL_APORT2YCH30              0x0000005EUL                             /**< Mode APORT2YCH30 for ACMP_INPUTSEL */
#define _ACMP_INPUTSEL_NEGSEL_APORT2XCH31              0x0000005FUL                             /**< Mode APORT2XCH31 for ACMP_INPUTSEL */
#define _ACMP_INPUTSEL_NEGSEL_APORT3XCH0               0x00000060UL                             /**< Mode APORT3XCH0 for ACMP_INPUTSEL */
#define _ACMP_INPUTSEL_NEGSEL_APORT3YCH1               0x00000061UL                             /**< Mode APORT3YCH1 for ACMP_INPUTSEL */
#define _ACMP_INPUTSEL_NEGSEL_APORT3XCH2               0x00000062UL                             /**< Mode APORT3XCH2 for ACMP_INPUTSEL */
#define _ACMP_INPUTSEL_NEGSEL_APORT3YCH3               0x00000063UL                             /**< Mode APORT3YCH3 for ACMP_INPUTSEL */
#define _ACMP_INPUTSEL_NEGSEL_APORT3XCH4               0x00000064UL                             /**< Mode APORT3XCH4 for ACMP_INPUTSEL */
#define _ACMP_INPUTSEL_NEGSEL_APORT3YCH5               0x00000065UL                             /**< Mode APORT3YCH5 for ACMP_INPUTSEL */
#define _ACMP_INPUTSEL_NEGSEL_APORT3XCH6               0x00000066UL                             /**< Mode APORT3XCH6 for ACMP_INPUTSEL */
#define _ACMP_INPUTSEL_NEGSEL_APORT3YCH7               0x00000067UL                             /**< Mode APORT3YCH7 for ACMP_INPUTSEL */
#define _ACMP_INPUTSEL_NEGSEL_APORT3XCH8               0x00000068UL                             /**< Mode APORT3XCH8 for ACMP_INPUTSEL */
#define _ACMP_INPUTSEL_NEGSEL_APORT3YCH9               0x00000069UL                             /**< Mode APORT3YCH9 for ACMP_INPUTSEL */
#define _ACMP_INPUTSEL_NEGSEL_APORT3XCH10              0x0000006AUL                             /**< Mode APORT3XCH10 for ACMP_INPUTSEL */
#define _ACMP_INPUTSEL_NEGSEL_APORT3YCH11              0x0000006BUL                             /**< Mode APORT3YCH11 for ACMP_INPUTSEL */
#define _ACMP_INPUTSEL_NEGSEL_APORT3XCH12              0x0000006CUL                             /**< Mode APORT3XCH12 for ACMP_INPUTSEL */
#define _ACMP_INPUTSEL_NEGSEL_APORT3YCH13              0x0000006DUL                             /**< Mode APORT3YCH13 for ACMP_INPUTSEL */
#define _ACMP_INPUTSEL_NEGSEL_APORT3XCH14              0x0000006EUL                             /**< Mode APORT3XCH14 for ACMP_INPUTSEL */
#define _ACMP_INPUTSEL_NEGSEL_APORT3YCH15              0x0000006FUL                             /**< Mode APORT3YCH15 for ACMP_INPUTSEL */
#define _ACMP_INPUTSEL_NEGSEL_APORT3XCH16              0x00000070UL                             /**< Mode APORT3XCH16 for ACMP_INPUTSEL */
#define _ACMP_INPUTSEL_NEGSEL_APORT3YCH17              0x00000071UL                             /**< Mode APORT3YCH17 for ACMP_INPUTSEL */
#define _ACMP_INPUTSEL_NEGSEL_APORT3XCH18              0x00000072UL                             /**< Mode APORT3XCH18 for ACMP_INPUTSEL */
#define _ACMP_INPUTSEL_NEGSEL_APORT3YCH19              0x00000073UL                             /**< Mode APORT3YCH19 for ACMP_INPUTSEL */
#define _ACMP_INPUTSEL_NEGSEL_APORT3XCH20              0x00000074UL                             /**< Mode APORT3XCH20 for ACMP_INPUTSEL */
#define _ACMP_INPUTSEL_NEGSEL_APORT3YCH21              0x00000075UL                             /**< Mode APORT3YCH21 for ACMP_INPUTSEL */
#define _ACMP_INPUTSEL_NEGSEL_APORT3XCH22              0x00000076UL                             /**< Mode APORT3XCH22 for ACMP_INPUTSEL */
#define _ACMP_INPUTSEL_NEGSEL_APORT3YCH23              0x00000077UL                             /**< Mode APORT3YCH23 for ACMP_INPUTSEL */
#define _ACMP_INPUTSEL_NEGSEL_APORT3XCH24              0x00000078UL                             /**< Mode APORT3XCH24 for ACMP_INPUTSEL */
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
#define _ACMP_INPUTSEL_NEGSEL_APORT4XCH25              0x00000099UL                             /**< Mode APORT4XCH25 for ACMP_INPUTSEL */
#define _ACMP_INPUTSEL_NEGSEL_APORT4YCH26              0x0000009AUL                             /**< Mode APORT4YCH26 for ACMP_INPUTSEL */
#define _ACMP_INPUTSEL_NEGSEL_APORT4XCH27              0x0000009BUL                             /**< Mode APORT4XCH27 for ACMP_INPUTSEL */
#define _ACMP_INPUTSEL_NEGSEL_APORT4YCH28              0x0000009CUL                             /**< Mode APORT4YCH28 for ACMP_INPUTSEL */
#define _ACMP_INPUTSEL_NEGSEL_APORT4XCH29              0x0000009DUL                             /**< Mode APORT4XCH29 for ACMP_INPUTSEL */
#define _ACMP_INPUTSEL_NEGSEL_APORT4YCH30              0x0000009EUL                             /**< Mode APORT4YCH30 for ACMP_INPUTSEL */
#define _ACMP_INPUTSEL_NEGSEL_APORT4YCH14              0x0000009EUL                             /**< Mode APORT4YCH14 for ACMP_INPUTSEL */
#define _ACMP_INPUTSEL_NEGSEL_APORT4XCH15              0x0000009FUL                             /**< Mode APORT4XCH15 for ACMP_INPUTSEL */
#define _ACMP_INPUTSEL_NEGSEL_APORT4XCH31              0x0000009FUL                             /**< Mode APORT4XCH31 for ACMP_INPUTSEL */
#define _ACMP_INPUTSEL_NEGSEL_DACOUT0                  0x000000F2UL                             /**< Mode DACOUT0 for ACMP_INPUTSEL */
#define _ACMP_INPUTSEL_NEGSEL_DACOUT1                  0x000000F3UL                             /**< Mode DACOUT1 for ACMP_INPUTSEL */
#define _ACMP_INPUTSEL_NEGSEL_VLP                      0x000000FBUL                             /**< Mode VLP for ACMP_INPUTSEL */
#define _ACMP_INPUTSEL_NEGSEL_VBDIV                    0x000000FCUL                             /**< Mode VBDIV for ACMP_INPUTSEL */
#define _ACMP_INPUTSEL_NEGSEL_VADIV                    0x000000FDUL                             /**< Mode VADIV for ACMP_INPUTSEL */
#define _ACMP_INPUTSEL_NEGSEL_VDD                      0x000000FEUL                             /**< Mode VDD for ACMP_INPUTSEL */
#define _ACMP_INPUTSEL_NEGSEL_VSS                      0x000000FFUL                             /**< Mode VSS for ACMP_INPUTSEL */
#define ACMP_INPUTSEL_NEGSEL_DEFAULT                   (_ACMP_INPUTSEL_NEGSEL_DEFAULT << 8)     /**< Shifted mode DEFAULT for ACMP_INPUTSEL */
#define ACMP_INPUTSEL_NEGSEL_APORT0XCH0                (_ACMP_INPUTSEL_NEGSEL_APORT0XCH0 << 8)  /**< Shifted mode APORT0XCH0 for ACMP_INPUTSEL */
#define ACMP_INPUTSEL_NEGSEL_APORT0XCH1                (_ACMP_INPUTSEL_NEGSEL_APORT0XCH1 << 8)  /**< Shifted mode APORT0XCH1 for ACMP_INPUTSEL */
#define ACMP_INPUTSEL_NEGSEL_APORT0XCH2                (_ACMP_INPUTSEL_NEGSEL_APORT0XCH2 << 8)  /**< Shifted mode APORT0XCH2 for ACMP_INPUTSEL */
#define ACMP_INPUTSEL_NEGSEL_APORT0XCH3                (_ACMP_INPUTSEL_NEGSEL_APORT0XCH3 << 8)  /**< Shifted mode APORT0XCH3 for ACMP_INPUTSEL */
#define ACMP_INPUTSEL_NEGSEL_APORT0XCH4                (_ACMP_INPUTSEL_NEGSEL_APORT0XCH4 << 8)  /**< Shifted mode APORT0XCH4 for ACMP_INPUTSEL */
#define ACMP_INPUTSEL_NEGSEL_APORT0XCH5                (_ACMP_INPUTSEL_NEGSEL_APORT0XCH5 << 8)  /**< Shifted mode APORT0XCH5 for ACMP_INPUTSEL */
#define ACMP_INPUTSEL_NEGSEL_APORT0XCH6                (_ACMP_INPUTSEL_NEGSEL_APORT0XCH6 << 8)  /**< Shifted mode APORT0XCH6 for ACMP_INPUTSEL */
#define ACMP_INPUTSEL_NEGSEL_APORT0XCH7                (_ACMP_INPUTSEL_NEGSEL_APORT0XCH7 << 8)  /**< Shifted mode APORT0XCH7 for ACMP_INPUTSEL */
#define ACMP_INPUTSEL_NEGSEL_APORT0XCH8                (_ACMP_INPUTSEL_NEGSEL_APORT0XCH8 << 8)  /**< Shifted mode APORT0XCH8 for ACMP_INPUTSEL */
#define ACMP_INPUTSEL_NEGSEL_APORT0XCH9                (_ACMP_INPUTSEL_NEGSEL_APORT0XCH9 << 8)  /**< Shifted mode APORT0XCH9 for ACMP_INPUTSEL */
#define ACMP_INPUTSEL_NEGSEL_APORT0XCH10               (_ACMP_INPUTSEL_NEGSEL_APORT0XCH10 << 8) /**< Shifted mode APORT0XCH10 for ACMP_INPUTSEL */
#define ACMP_INPUTSEL_NEGSEL_APORT0XCH11               (_ACMP_INPUTSEL_NEGSEL_APORT0XCH11 << 8) /**< Shifted mode APORT0XCH11 for ACMP_INPUTSEL */
#define ACMP_INPUTSEL_NEGSEL_APORT0XCH12               (_ACMP_INPUTSEL_NEGSEL_APORT0XCH12 << 8) /**< Shifted mode APORT0XCH12 for ACMP_INPUTSEL */
#define ACMP_INPUTSEL_NEGSEL_APORT0XCH13               (_ACMP_INPUTSEL_NEGSEL_APORT0XCH13 << 8) /**< Shifted mode APORT0XCH13 for ACMP_INPUTSEL */
#define ACMP_INPUTSEL_NEGSEL_APORT0XCH14               (_ACMP_INPUTSEL_NEGSEL_APORT0XCH14 << 8) /**< Shifted mode APORT0XCH14 for ACMP_INPUTSEL */
#define ACMP_INPUTSEL_NEGSEL_APORT0XCH15               (_ACMP_INPUTSEL_NEGSEL_APORT0XCH15 << 8) /**< Shifted mode APORT0XCH15 for ACMP_INPUTSEL */
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
#define ACMP_INPUTSEL_NEGSEL_APORT2YCH20               (_ACMP_INPUTSEL_NEGSEL_APORT2YCH20 << 8) /**< Shifted mode APORT2YCH20 for ACMP_INPUTSEL */
#define ACMP_INPUTSEL_NEGSEL_APORT2XCH21               (_ACMP_INPUTSEL_NEGSEL_APORT2XCH21 << 8) /**< Shifted mode APORT2XCH21 for ACMP_INPUTSEL */
#define ACMP_INPUTSEL_NEGSEL_APORT2YCH22               (_ACMP_INPUTSEL_NEGSEL_APORT2YCH22 << 8) /**< Shifted mode APORT2YCH22 for ACMP_INPUTSEL */
#define ACMP_INPUTSEL_NEGSEL_APORT2XCH23               (_ACMP_INPUTSEL_NEGSEL_APORT2XCH23 << 8) /**< Shifted mode APORT2XCH23 for ACMP_INPUTSEL */
#define ACMP_INPUTSEL_NEGSEL_APORT2YCH24               (_ACMP_INPUTSEL_NEGSEL_APORT2YCH24 << 8) /**< Shifted mode APORT2YCH24 for ACMP_INPUTSEL */
#define ACMP_INPUTSEL_NEGSEL_APORT2XCH25               (_ACMP_INPUTSEL_NEGSEL_APORT2XCH25 << 8) /**< Shifted mode APORT2XCH25 for ACMP_INPUTSEL */
#define ACMP_INPUTSEL_NEGSEL_APORT2YCH26               (_ACMP_INPUTSEL_NEGSEL_APORT2YCH26 << 8) /**< Shifted mode APORT2YCH26 for ACMP_INPUTSEL */
#define ACMP_INPUTSEL_NEGSEL_APORT2XCH27               (_ACMP_INPUTSEL_NEGSEL_APORT2XCH27 << 8) /**< Shifted mode APORT2XCH27 for ACMP_INPUTSEL */
#define ACMP_INPUTSEL_NEGSEL_APORT2YCH28               (_ACMP_INPUTSEL_NEGSEL_APORT2YCH28 << 8) /**< Shifted mode APORT2YCH28 for ACMP_INPUTSEL */
#define ACMP_INPUTSEL_NEGSEL_APORT2XCH29               (_ACMP_INPUTSEL_NEGSEL_APORT2XCH29 << 8) /**< Shifted mode APORT2XCH29 for ACMP_INPUTSEL */
#define ACMP_INPUTSEL_NEGSEL_APORT2YCH30               (_ACMP_INPUTSEL_NEGSEL_APORT2YCH30 << 8) /**< Shifted mode APORT2YCH30 for ACMP_INPUTSEL */
#define ACMP_INPUTSEL_NEGSEL_APORT2XCH31               (_ACMP_INPUTSEL_NEGSEL_APORT2XCH31 << 8) /**< Shifted mode APORT2XCH31 for ACMP_INPUTSEL */
#define ACMP_INPUTSEL_NEGSEL_APORT3XCH0                (_ACMP_INPUTSEL_NEGSEL_APORT3XCH0 << 8)  /**< Shifted mode APORT3XCH0 for ACMP_INPUTSEL */
#define ACMP_INPUTSEL_NEGSEL_APORT3YCH1                (_ACMP_INPUTSEL_NEGSEL_APORT3YCH1 << 8)  /**< Shifted mode APORT3YCH1 for ACMP_INPUTSEL */
#define ACMP_INPUTSEL_NEGSEL_APORT3XCH2                (_ACMP_INPUTSEL_NEGSEL_APORT3XCH2 << 8)  /**< Shifted mode APORT3XCH2 for ACMP_INPUTSEL */
#define ACMP_INPUTSEL_NEGSEL_APORT3YCH3                (_ACMP_INPUTSEL_NEGSEL_APORT3YCH3 << 8)  /**< Shifted mode APORT3YCH3 for ACMP_INPUTSEL */
#define ACMP_INPUTSEL_NEGSEL_APORT3XCH4                (_ACMP_INPUTSEL_NEGSEL_APORT3XCH4 << 8)  /**< Shifted mode APORT3XCH4 for ACMP_INPUTSEL */
#define ACMP_INPUTSEL_NEGSEL_APORT3YCH5                (_ACMP_INPUTSEL_NEGSEL_APORT3YCH5 << 8)  /**< Shifted mode APORT3YCH5 for ACMP_INPUTSEL */
#define ACMP_INPUTSEL_NEGSEL_APORT3XCH6                (_ACMP_INPUTSEL_NEGSEL_APORT3XCH6 << 8)  /**< Shifted mode APORT3XCH6 for ACMP_INPUTSEL */
#define ACMP_INPUTSEL_NEGSEL_APORT3YCH7                (_ACMP_INPUTSEL_NEGSEL_APORT3YCH7 << 8)  /**< Shifted mode APORT3YCH7 for ACMP_INPUTSEL */
#define ACMP_INPUTSEL_NEGSEL_APORT3XCH8                (_ACMP_INPUTSEL_NEGSEL_APORT3XCH8 << 8)  /**< Shifted mode APORT3XCH8 for ACMP_INPUTSEL */
#define ACMP_INPUTSEL_NEGSEL_APORT3YCH9                (_ACMP_INPUTSEL_NEGSEL_APORT3YCH9 << 8)  /**< Shifted mode APORT3YCH9 for ACMP_INPUTSEL */
#define ACMP_INPUTSEL_NEGSEL_APORT3XCH10               (_ACMP_INPUTSEL_NEGSEL_APORT3XCH10 << 8) /**< Shifted mode APORT3XCH10 for ACMP_INPUTSEL */
#define ACMP_INPUTSEL_NEGSEL_APORT3YCH11               (_ACMP_INPUTSEL_NEGSEL_APORT3YCH11 << 8) /**< Shifted mode APORT3YCH11 for ACMP_INPUTSEL */
#define ACMP_INPUTSEL_NEGSEL_APORT3XCH12               (_ACMP_INPUTSEL_NEGSEL_APORT3XCH12 << 8) /**< Shifted mode APORT3XCH12 for ACMP_INPUTSEL */
#define ACMP_INPUTSEL_NEGSEL_APORT3YCH13               (_ACMP_INPUTSEL_NEGSEL_APORT3YCH13 << 8) /**< Shifted mode APORT3YCH13 for ACMP_INPUTSEL */
#define ACMP_INPUTSEL_NEGSEL_APORT3XCH14               (_ACMP_INPUTSEL_NEGSEL_APORT3XCH14 << 8) /**< Shifted mode APORT3XCH14 for ACMP_INPUTSEL */
#define ACMP_INPUTSEL_NEGSEL_APORT3YCH15               (_ACMP_INPUTSEL_NEGSEL_APORT3YCH15 << 8) /**< Shifted mode APORT3YCH15 for ACMP_INPUTSEL */
#define ACMP_INPUTSEL_NEGSEL_APORT3XCH16               (_ACMP_INPUTSEL_NEGSEL_APORT3XCH16 << 8) /**< Shifted mode APORT3XCH16 for ACMP_INPUTSEL */
#define ACMP_INPUTSEL_NEGSEL_APORT3YCH17               (_ACMP_INPUTSEL_NEGSEL_APORT3YCH17 << 8) /**< Shifted mode APORT3YCH17 for ACMP_INPUTSEL */
#define ACMP_INPUTSEL_NEGSEL_APORT3XCH18               (_ACMP_INPUTSEL_NEGSEL_APORT3XCH18 << 8) /**< Shifted mode APORT3XCH18 for ACMP_INPUTSEL */
#define ACMP_INPUTSEL_NEGSEL_APORT3YCH19               (_ACMP_INPUTSEL_NEGSEL_APORT3YCH19 << 8) /**< Shifted mode APORT3YCH19 for ACMP_INPUTSEL */
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
#define ACMP_INPUTSEL_NEGSEL_APORT4YCH18               (_ACMP_INPUTSEL_NEGSEL_APORT4YCH18 << 8) /**< Shifted mode APORT4YCH18 for ACMP_INPUTSEL */
#define ACMP_INPUTSEL_NEGSEL_APORT4XCH19               (_ACMP_INPUTSEL_NEGSEL_APORT4XCH19 << 8) /**< Shifted mode APORT4XCH19 for ACMP_INPUTSEL */
#define ACMP_INPUTSEL_NEGSEL_APORT4YCH20               (_ACMP_INPUTSEL_NEGSEL_APORT4YCH20 << 8) /**< Shifted mode APORT4YCH20 for ACMP_INPUTSEL */
#define ACMP_INPUTSEL_NEGSEL_APORT4XCH21               (_ACMP_INPUTSEL_NEGSEL_APORT4XCH21 << 8) /**< Shifted mode APORT4XCH21 for ACMP_INPUTSEL */
#define ACMP_INPUTSEL_NEGSEL_APORT4YCH22               (_ACMP_INPUTSEL_NEGSEL_APORT4YCH22 << 8) /**< Shifted mode APORT4YCH22 for ACMP_INPUTSEL */
#define ACMP_INPUTSEL_NEGSEL_APORT4XCH23               (_ACMP_INPUTSEL_NEGSEL_APORT4XCH23 << 8) /**< Shifted mode APORT4XCH23 for ACMP_INPUTSEL */
#define ACMP_INPUTSEL_NEGSEL_APORT4YCH24               (_ACMP_INPUTSEL_NEGSEL_APORT4YCH24 << 8) /**< Shifted mode APORT4YCH24 for ACMP_INPUTSEL */
#define ACMP_INPUTSEL_NEGSEL_APORT4XCH25               (_ACMP_INPUTSEL_NEGSEL_APORT4XCH25 << 8) /**< Shifted mode APORT4XCH25 for ACMP_INPUTSEL */
#define ACMP_INPUTSEL_NEGSEL_APORT4YCH26               (_ACMP_INPUTSEL_NEGSEL_APORT4YCH26 << 8) /**< Shifted mode APORT4YCH26 for ACMP_INPUTSEL */
#define ACMP_INPUTSEL_NEGSEL_APORT4XCH27               (_ACMP_INPUTSEL_NEGSEL_APORT4XCH27 << 8) /**< Shifted mode APORT4XCH27 for ACMP_INPUTSEL */
#define ACMP_INPUTSEL_NEGSEL_APORT4YCH28               (_ACMP_INPUTSEL_NEGSEL_APORT4YCH28 << 8) /**< Shifted mode APORT4YCH28 for ACMP_INPUTSEL */
#define ACMP_INPUTSEL_NEGSEL_APORT4XCH29               (_ACMP_INPUTSEL_NEGSEL_APORT4XCH29 << 8) /**< Shifted mode APORT4XCH29 for ACMP_INPUTSEL */
#define ACMP_INPUTSEL_NEGSEL_APORT4YCH30               (_ACMP_INPUTSEL_NEGSEL_APORT4YCH30 << 8) /**< Shifted mode APORT4YCH30 for ACMP_INPUTSEL */
#define ACMP_INPUTSEL_NEGSEL_APORT4YCH14               (_ACMP_INPUTSEL_NEGSEL_APORT4YCH14 << 8) /**< Shifted mode APORT4YCH14 for ACMP_INPUTSEL */
#define ACMP_INPUTSEL_NEGSEL_APORT4XCH15               (_ACMP_INPUTSEL_NEGSEL_APORT4XCH15 << 8) /**< Shifted mode APORT4XCH15 for ACMP_INPUTSEL */
#define ACMP_INPUTSEL_NEGSEL_APORT4XCH31               (_ACMP_INPUTSEL_NEGSEL_APORT4XCH31 << 8) /**< Shifted mode APORT4XCH31 for ACMP_INPUTSEL */
#define ACMP_INPUTSEL_NEGSEL_DACOUT0                   (_ACMP_INPUTSEL_NEGSEL_DACOUT0 << 8)     /**< Shifted mode DACOUT0 for ACMP_INPUTSEL */
#define ACMP_INPUTSEL_NEGSEL_DACOUT1                   (_ACMP_INPUTSEL_NEGSEL_DACOUT1 << 8)     /**< Shifted mode DACOUT1 for ACMP_INPUTSEL */
#define ACMP_INPUTSEL_NEGSEL_VLP                       (_ACMP_INPUTSEL_NEGSEL_VLP << 8)         /**< Shifted mode VLP for ACMP_INPUTSEL */
#define ACMP_INPUTSEL_NEGSEL_VBDIV                     (_ACMP_INPUTSEL_NEGSEL_VBDIV << 8)       /**< Shifted mode VBDIV for ACMP_INPUTSEL */
#define ACMP_INPUTSEL_NEGSEL_VADIV                     (_ACMP_INPUTSEL_NEGSEL_VADIV << 8)       /**< Shifted mode VADIV for ACMP_INPUTSEL */
#define ACMP_INPUTSEL_NEGSEL_VDD                       (_ACMP_INPUTSEL_NEGSEL_VDD << 8)         /**< Shifted mode VDD for ACMP_INPUTSEL */
#define ACMP_INPUTSEL_NEGSEL_VSS                       (_ACMP_INPUTSEL_NEGSEL_VSS << 8)         /**< Shifted mode VSS for ACMP_INPUTSEL */
#define _ACMP_INPUTSEL_VASEL_SHIFT                     16                                       /**< Shift value for ACMP_VASEL */
#define _ACMP_INPUTSEL_VASEL_MASK                      0x3F0000UL                               /**< Bit mask for ACMP_VASEL */
#define _ACMP_INPUTSEL_VASEL_DEFAULT                   0x00000000UL                             /**< Mode DEFAULT for ACMP_INPUTSEL */
#define _ACMP_INPUTSEL_VASEL_VDD                       0x00000000UL                             /**< Mode VDD for ACMP_INPUTSEL */
#define _ACMP_INPUTSEL_VASEL_APORT2YCH0                0x00000001UL                             /**< Mode APORT2YCH0 for ACMP_INPUTSEL */
#define _ACMP_INPUTSEL_VASEL_APORT2YCH2                0x00000003UL                             /**< Mode APORT2YCH2 for ACMP_INPUTSEL */
#define _ACMP_INPUTSEL_VASEL_APORT2YCH4                0x00000005UL                             /**< Mode APORT2YCH4 for ACMP_INPUTSEL */
#define _ACMP_INPUTSEL_VASEL_APORT2YCH6                0x00000007UL                             /**< Mode APORT2YCH6 for ACMP_INPUTSEL */
#define _ACMP_INPUTSEL_VASEL_APORT2YCH8                0x00000009UL                             /**< Mode APORT2YCH8 for ACMP_INPUTSEL */
#define _ACMP_INPUTSEL_VASEL_APORT2YCH10               0x0000000BUL                             /**< Mode APORT2YCH10 for ACMP_INPUTSEL */
#define _ACMP_INPUTSEL_VASEL_APORT2YCH12               0x0000000DUL                             /**< Mode APORT2YCH12 for ACMP_INPUTSEL */
#define _ACMP_INPUTSEL_VASEL_APORT2YCH14               0x0000000FUL                             /**< Mode APORT2YCH14 for ACMP_INPUTSEL */
#define _ACMP_INPUTSEL_VASEL_APORT2YCH16               0x00000011UL                             /**< Mode APORT2YCH16 for ACMP_INPUTSEL */
#define _ACMP_INPUTSEL_VASEL_APORT2YCH18               0x00000013UL                             /**< Mode APORT2YCH18 for ACMP_INPUTSEL */
#define _ACMP_INPUTSEL_VASEL_APORT2YCH20               0x00000015UL                             /**< Mode APORT2YCH20 for ACMP_INPUTSEL */
#define _ACMP_INPUTSEL_VASEL_APORT2YCH22               0x00000017UL                             /**< Mode APORT2YCH22 for ACMP_INPUTSEL */
#define _ACMP_INPUTSEL_VASEL_APORT2YCH24               0x00000019UL                             /**< Mode APORT2YCH24 for ACMP_INPUTSEL */
#define _ACMP_INPUTSEL_VASEL_APORT2YCH26               0x0000001BUL                             /**< Mode APORT2YCH26 for ACMP_INPUTSEL */
#define _ACMP_INPUTSEL_VASEL_APORT2YCH28               0x0000001DUL                             /**< Mode APORT2YCH28 for ACMP_INPUTSEL */
#define _ACMP_INPUTSEL_VASEL_APORT2YCH30               0x0000001FUL                             /**< Mode APORT2YCH30 for ACMP_INPUTSEL */
#define _ACMP_INPUTSEL_VASEL_APORT1XCH0                0x00000020UL                             /**< Mode APORT1XCH0 for ACMP_INPUTSEL */
#define _ACMP_INPUTSEL_VASEL_APORT1YCH1                0x00000021UL                             /**< Mode APORT1YCH1 for ACMP_INPUTSEL */
#define _ACMP_INPUTSEL_VASEL_APORT1XCH2                0x00000022UL                             /**< Mode APORT1XCH2 for ACMP_INPUTSEL */
#define _ACMP_INPUTSEL_VASEL_APORT1YCH3                0x00000023UL                             /**< Mode APORT1YCH3 for ACMP_INPUTSEL */
#define _ACMP_INPUTSEL_VASEL_APORT1XCH4                0x00000024UL                             /**< Mode APORT1XCH4 for ACMP_INPUTSEL */
#define _ACMP_INPUTSEL_VASEL_APORT1YCH5                0x00000025UL                             /**< Mode APORT1YCH5 for ACMP_INPUTSEL */
#define _ACMP_INPUTSEL_VASEL_APORT1XCH6                0x00000026UL                             /**< Mode APORT1XCH6 for ACMP_INPUTSEL */
#define _ACMP_INPUTSEL_VASEL_APORT1YCH7                0x00000027UL                             /**< Mode APORT1YCH7 for ACMP_INPUTSEL */
#define _ACMP_INPUTSEL_VASEL_APORT1XCH8                0x00000028UL                             /**< Mode APORT1XCH8 for ACMP_INPUTSEL */
#define _ACMP_INPUTSEL_VASEL_APORT1YCH9                0x00000029UL                             /**< Mode APORT1YCH9 for ACMP_INPUTSEL */
#define _ACMP_INPUTSEL_VASEL_APORT1XCH10               0x0000002AUL                             /**< Mode APORT1XCH10 for ACMP_INPUTSEL */
#define _ACMP_INPUTSEL_VASEL_APORT1YCH11               0x0000002BUL                             /**< Mode APORT1YCH11 for ACMP_INPUTSEL */
#define _ACMP_INPUTSEL_VASEL_APORT1XCH12               0x0000002CUL                             /**< Mode APORT1XCH12 for ACMP_INPUTSEL */
#define _ACMP_INPUTSEL_VASEL_APORT1YCH13               0x0000002DUL                             /**< Mode APORT1YCH13 for ACMP_INPUTSEL */
#define _ACMP_INPUTSEL_VASEL_APORT1XCH14               0x0000002EUL                             /**< Mode APORT1XCH14 for ACMP_INPUTSEL */
#define _ACMP_INPUTSEL_VASEL_APORT1YCH15               0x0000002FUL                             /**< Mode APORT1YCH15 for ACMP_INPUTSEL */
#define _ACMP_INPUTSEL_VASEL_APORT1XCH16               0x00000030UL                             /**< Mode APORT1XCH16 for ACMP_INPUTSEL */
#define _ACMP_INPUTSEL_VASEL_APORT1YCH17               0x00000031UL                             /**< Mode APORT1YCH17 for ACMP_INPUTSEL */
#define _ACMP_INPUTSEL_VASEL_APORT1XCH18               0x00000032UL                             /**< Mode APORT1XCH18 for ACMP_INPUTSEL */
#define _ACMP_INPUTSEL_VASEL_APORT1YCH19               0x00000033UL                             /**< Mode APORT1YCH19 for ACMP_INPUTSEL */
#define _ACMP_INPUTSEL_VASEL_APORT1XCH20               0x00000034UL                             /**< Mode APORT1XCH20 for ACMP_INPUTSEL */
#define _ACMP_INPUTSEL_VASEL_APORT1YCH21               0x00000035UL                             /**< Mode APORT1YCH21 for ACMP_INPUTSEL */
#define _ACMP_INPUTSEL_VASEL_APORT1XCH22               0x00000036UL                             /**< Mode APORT1XCH22 for ACMP_INPUTSEL */
#define _ACMP_INPUTSEL_VASEL_APORT1YCH23               0x00000037UL                             /**< Mode APORT1YCH23 for ACMP_INPUTSEL */
#define _ACMP_INPUTSEL_VASEL_APORT1XCH24               0x00000038UL                             /**< Mode APORT1XCH24 for ACMP_INPUTSEL */
#define _ACMP_INPUTSEL_VASEL_APORT1YCH25               0x00000039UL                             /**< Mode APORT1YCH25 for ACMP_INPUTSEL */
#define _ACMP_INPUTSEL_VASEL_APORT1XCH26               0x0000003AUL                             /**< Mode APORT1XCH26 for ACMP_INPUTSEL */
#define _ACMP_INPUTSEL_VASEL_APORT1YCH27               0x0000003BUL                             /**< Mode APORT1YCH27 for ACMP_INPUTSEL */
#define _ACMP_INPUTSEL_VASEL_APORT1XCH28               0x0000003CUL                             /**< Mode APORT1XCH28 for ACMP_INPUTSEL */
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
