shsa5563/Ring-WearTech/Firmware/soc-smartPhone_NoBuff/inc/efr32bg13p_adc.h

/**************************************************************************//**
 * @file efr32bg13p_adc.h
 * @brief EFR32BG13P_ADC register and bit field definitions
 * @version 5.3.2
 ******************************************************************************
 * # License
 * <b>Copyright 2017 Silicon Laboratories, Inc. http://www.silabs.com</b>
 ******************************************************************************
 *
 * Permission is granted to anyone to use this software for any purpose,
 * including commercial applications, and to alter it and redistribute it
 * freely, subject to the following restrictions:
 *
 * 1. The origin of this software must not be misrepresented; you must not
 *    claim that you wrote the original software.@n
 * 2. Altered source versions must be plainly marked as such, and must not be
 *    misrepresented as being the original software.@n
 * 3. This notice may not be removed or altered from any source distribution.
 *
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
 * Silicon Laboratories, Inc. will not be liable for any consequential,
 * incidental, or special damages, or any other relief, or for any claim by
 * any third party, arising from your use of this Software.
 *
 *****************************************************************************/

#if defined(__ICCARM__)
#pragma system_include       /* Treat file as system include file. */
#elif defined(__ARMCC_VERSION) && (__ARMCC_VERSION >= 6010050)
#pragma clang system_header  /* Treat file as system include file. */
#endif

/**************************************************************************//**
* @addtogroup Parts
* @{
******************************************************************************/
/**************************************************************************//**
 * @defgroup EFR32BG13P_ADC ADC
 * @{
 * @brief EFR32BG13P_ADC Register Declaration
 *****************************************************************************/
/** ADC Register Declaration */
typedef struct {
  __IOM uint32_t CTRL;            /**< Control Register  */
  uint32_t       RESERVED0[1];    /**< Reserved for future use **/
  __IOM uint32_t CMD;             /**< Command Register  */
  __IM uint32_t  STATUS;          /**< Status Register  */
  __IOM uint32_t SINGLECTRL;      /**< Single Channel Control Register  */
  __IOM uint32_t SINGLECTRLX;     /**< Single Channel Control Register continued  */
  __IOM uint32_t SCANCTRL;        /**< Scan Control Register  */
  __IOM uint32_t SCANCTRLX;       /**< Scan Control Register continued  */
  __IOM uint32_t SCANMASK;        /**< Scan Sequence Input Mask Register  */
  __IOM uint32_t SCANINPUTSEL;    /**< Input Selection register for Scan mode  */
  __IOM uint32_t SCANNEGSEL;      /**< Negative Input select register for Scan  */
  __IOM uint32_t CMPTHR;          /**< Compare Threshold Register  */
  __IOM uint32_t BIASPROG;        /**< Bias Programming Register for various analog blocks used in ADC operation.  */
  __IOM uint32_t CAL;             /**< Calibration Register  */
  __IM uint32_t  IF;              /**< Interrupt Flag Register  */
  __IOM uint32_t IFS;             /**< Interrupt Flag Set Register  */
  __IOM uint32_t IFC;             /**< Interrupt Flag Clear Register  */
  __IOM uint32_t IEN;             /**< Interrupt Enable Register  */
  __IM uint32_t  SINGLEDATA;      /**< Single Conversion Result Data  */
  __IM uint32_t  SCANDATA;        /**< Scan Conversion Result Data  */
  __IM uint32_t  SINGLEDATAP;     /**< Single Conversion Result Data Peek Register  */
  __IM uint32_t  SCANDATAP;       /**< Scan Sequence Result Data Peek Register  */
  uint32_t       RESERVED1[4];    /**< Reserved for future use **/
  __IM uint32_t  SCANDATAX;       /**< Scan Sequence Result Data + Data Source Register  */
  __IM uint32_t  SCANDATAXP;      /**< Scan Sequence Result Data + Data Source Peek Register  */

  uint32_t       RESERVED2[3];    /**< Reserved for future use **/
  __IM uint32_t  APORTREQ;        /**< APORT Request Status Register  */
  __IM uint32_t  APORTCONFLICT;   /**< APORT Conflict Status Register  */
  __IM uint32_t  SINGLEFIFOCOUNT; /**< Single FIFO Count Register  */
  __IM uint32_t  SCANFIFOCOUNT;   /**< Scan FIFO Count Register  */
  __IOM uint32_t SINGLEFIFOCLEAR; /**< Single FIFO Clear Register  */
  __IOM uint32_t SCANFIFOCLEAR;   /**< Scan FIFO Clear Register  */
  __IOM uint32_t APORTMASTERDIS;  /**< APORT Bus Master Disable Register  */
} ADC_TypeDef;                    /** @} */

/**************************************************************************//**
 * @addtogroup EFR32BG13P_ADC
 * @{
 * @defgroup EFR32BG13P_ADC_BitFields  ADC Bit Fields
 * @{
 *****************************************************************************/

/* Bit fields for ADC CTRL */
#define _ADC_CTRL_RESETVALUE                               0x001F0000UL                                  /**< Default value for ADC_CTRL */
#define _ADC_CTRL_MASK                                     0xFF7F7FDFUL                                  /**< Mask for ADC_CTRL */
#define _ADC_CTRL_WARMUPMODE_SHIFT                         0                                             /**< Shift value for ADC_WARMUPMODE */
#define _ADC_CTRL_WARMUPMODE_MASK                          0x3UL                                         /**< Bit mask for ADC_WARMUPMODE */
#define _ADC_CTRL_WARMUPMODE_DEFAULT                       0x00000000UL                                  /**< Mode DEFAULT for ADC_CTRL */
#define _ADC_CTRL_WARMUPMODE_NORMAL                        0x00000000UL                                  /**< Mode NORMAL for ADC_CTRL */
#define _ADC_CTRL_WARMUPMODE_KEEPINSTANDBY                 0x00000001UL                                  /**< Mode KEEPINSTANDBY for ADC_CTRL */
#define _ADC_CTRL_WARMUPMODE_KEEPINSLOWACC                 0x00000002UL                                  /**< Mode KEEPINSLOWACC for ADC_CTRL */
#define _ADC_CTRL_WARMUPMODE_KEEPADCWARM                   0x00000003UL                                  /**< Mode KEEPADCWARM for ADC_CTRL */
#define ADC_CTRL_WARMUPMODE_DEFAULT                        (_ADC_CTRL_WARMUPMODE_DEFAULT << 0)           /**< Shifted mode DEFAULT for ADC_CTRL */
#define ADC_CTRL_WARMUPMODE_NORMAL                         (_ADC_CTRL_WARMUPMODE_NORMAL << 0)            /**< Shifted mode NORMAL for ADC_CTRL */
#define ADC_CTRL_WARMUPMODE_KEEPINSTANDBY                  (_ADC_CTRL_WARMUPMODE_KEEPINSTANDBY << 0)     /**< Shifted mode KEEPINSTANDBY for ADC_CTRL */
#define ADC_CTRL_WARMUPMODE_KEEPINSLOWACC                  (_ADC_CTRL_WARMUPMODE_KEEPINSLOWACC << 0)     /**< Shifted mode KEEPINSLOWACC for ADC_CTRL */
#define ADC_CTRL_WARMUPMODE_KEEPADCWARM                    (_ADC_CTRL_WARMUPMODE_KEEPADCWARM << 0)       /**< Shifted mode KEEPADCWARM for ADC_CTRL */
#define ADC_CTRL_SINGLEDMAWU                               (0x1UL << 2)                                  /**< SINGLEFIFO DMA Wakeup */
#define _ADC_CTRL_SINGLEDMAWU_SHIFT                        2                                             /**< Shift value for ADC_SINGLEDMAWU */
#define _ADC_CTRL_SINGLEDMAWU_MASK                         0x4UL                                         /**< Bit mask for ADC_SINGLEDMAWU */
#define _ADC_CTRL_SINGLEDMAWU_DEFAULT                      0x00000000UL                                  /**< Mode DEFAULT for ADC_CTRL */
#define ADC_CTRL_SINGLEDMAWU_DEFAULT                       (_ADC_CTRL_SINGLEDMAWU_DEFAULT << 2)          /**< Shifted mode DEFAULT for ADC_CTRL */
#define ADC_CTRL_SCANDMAWU                                 (0x1UL << 3)                                  /**< SCANFIFO DMA Wakeup */
#define _ADC_CTRL_SCANDMAWU_SHIFT                          3                                             /**< Shift value for ADC_SCANDMAWU */
#define _ADC_CTRL_SCANDMAWU_MASK                           0x8UL                                         /**< Bit mask for ADC_SCANDMAWU */
#define _ADC_CTRL_SCANDMAWU_DEFAULT                        0x00000000UL                                  /**< Mode DEFAULT for ADC_CTRL */
#define ADC_CTRL_SCANDMAWU_DEFAULT                         (_ADC_CTRL_SCANDMAWU_DEFAULT << 3)            /**< Shifted mode DEFAULT for ADC_CTRL */
#define ADC_CTRL_TAILGATE                                  (0x1UL << 4)                                  /**< Conversion Tailgating */
#define _ADC_CTRL_TAILGATE_SHIFT                           4                                             /**< Shift value for ADC_TAILGATE */
#define _ADC_CTRL_TAILGATE_MASK                            0x10UL                                        /**< Bit mask for ADC_TAILGATE */
#define _ADC_CTRL_TAILGATE_DEFAULT                         0x00000000UL                                  /**< Mode DEFAULT for ADC_CTRL */
#define ADC_CTRL_TAILGATE_DEFAULT                          (_ADC_CTRL_TAILGATE_DEFAULT << 4)             /**< Shifted mode DEFAULT for ADC_CTRL */
#define ADC_CTRL_ASYNCCLKEN                                (0x1UL << 6)                                  /**< Selects ASYNC CLK enable mode when ADCCLKMODE=1 */
#define _ADC_CTRL_ASYNCCLKEN_SHIFT                         6                                             /**< Shift value for ADC_ASYNCCLKEN */
#define _ADC_CTRL_ASYNCCLKEN_MASK                          0x40UL                                        /**< Bit mask for ADC_ASYNCCLKEN */
#define _ADC_CTRL_ASYNCCLKEN_DEFAULT                       0x00000000UL                                  /**< Mode DEFAULT for ADC_CTRL */
#define _ADC_CTRL_ASYNCCLKEN_ASNEEDED                      0x00000000UL                                  /**< Mode ASNEEDED for ADC_CTRL */
#define _ADC_CTRL_ASYNCCLKEN_ALWAYSON                      0x00000001UL                                  /**< Mode ALWAYSON for ADC_CTRL */
#define ADC_CTRL_ASYNCCLKEN_DEFAULT                        (_ADC_CTRL_ASYNCCLKEN_DEFAULT << 6)           /**< Shifted mode DEFAULT for ADC_CTRL */
#define ADC_CTRL_ASYNCCLKEN_ASNEEDED                       (_ADC_CTRL_ASYNCCLKEN_ASNEEDED << 6)          /**< Shifted mode ASNEEDED for ADC_CTRL */
#define ADC_CTRL_ASYNCCLKEN_ALWAYSON                       (_ADC_CTRL_ASYNCCLKEN_ALWAYSON << 6)          /**< Shifted mode ALWAYSON for ADC_CTRL */
#define ADC_CTRL_ADCCLKMODE                                (0x1UL << 7)                                  /**< ADC Clock Mode */
#define _ADC_CTRL_ADCCLKMODE_SHIFT                         7                                             /**< Shift value for ADC_ADCCLKMODE */
#define _ADC_CTRL_ADCCLKMODE_MASK                          0x80UL                                        /**< Bit mask for ADC_ADCCLKMODE */
#define _ADC_CTRL_ADCCLKMODE_DEFAULT                       0x00000000UL                                  /**< Mode DEFAULT for ADC_CTRL */
#define _ADC_CTRL_ADCCLKMODE_SYNC                          0x00000000UL                                  /**< Mode SYNC for ADC_CTRL */
#define _ADC_CTRL_ADCCLKMODE_ASYNC                         0x00000001UL                                  /**< Mode ASYNC for ADC_CTRL */
#define ADC_CTRL_ADCCLKMODE_DEFAULT                        (_ADC_CTRL_ADCCLKMODE_DEFAULT << 7)           /**< Shifted mode DEFAULT for ADC_CTRL */
#define ADC_CTRL_ADCCLKMODE_SYNC                           (_ADC_CTRL_ADCCLKMODE_SYNC << 7)              /**< Shifted mode SYNC for ADC_CTRL */
#define ADC_CTRL_ADCCLKMODE_ASYNC                          (_ADC_CTRL_ADCCLKMODE_ASYNC << 7)             /**< Shifted mode ASYNC for ADC_CTRL */
#define _ADC_CTRL_PRESC_SHIFT                              8                                             /**< Shift value for ADC_PRESC */
#define _ADC_CTRL_PRESC_MASK                               0x7F00UL                                      /**< Bit mask for ADC_PRESC */
#define _ADC_CTRL_PRESC_DEFAULT                            0x00000000UL                                  /**< Mode DEFAULT for ADC_CTRL */
#define _ADC_CTRL_PRESC_NODIVISION                         0x00000000UL                                  /**< Mode NODIVISION for ADC_CTRL */
#define ADC_CTRL_PRESC_DEFAULT                             (_ADC_CTRL_PRESC_DEFAULT << 8)                /**< Shifted mode DEFAULT for ADC_CTRL */
#define ADC_CTRL_PRESC_NODIVISION                          (_ADC_CTRL_PRESC_NODIVISION << 8)             /**< Shifted mode NODIVISION for ADC_CTRL */
#define _ADC_CTRL_TIMEBASE_SHIFT                           16                                            /**< Shift value for ADC_TIMEBASE */
#define _ADC_CTRL_TIMEBASE_MASK                            0x7F0000UL                                    /**< Bit mask for ADC_TIMEBASE */
#define _ADC_CTRL_TIMEBASE_DEFAULT                         0x0000001FUL                                  /**< Mode DEFAULT for ADC_CTRL */
#define ADC_CTRL_TIMEBASE_DEFAULT                          (_ADC_CTRL_TIMEBASE_DEFAULT << 16)            /**< Shifted mode DEFAULT for ADC_CTRL */
#define _ADC_CTRL_OVSRSEL_SHIFT                            24                                            /**< Shift value for ADC_OVSRSEL */
#define _ADC_CTRL_OVSRSEL_MASK                             0xF000000UL                                   /**< Bit mask for ADC_OVSRSEL */
#define _ADC_CTRL_OVSRSEL_DEFAULT                          0x00000000UL                                  /**< Mode DEFAULT for ADC_CTRL */
#define _ADC_CTRL_OVSRSEL_X2                               0x00000000UL                                  /**< Mode X2 for ADC_CTRL */
#define _ADC_CTRL_OVSRSEL_X4                               0x00000001UL                                  /**< Mode X4 for ADC_CTRL */
#define _ADC_CTRL_OVSRSEL_X8                               0x00000002UL                                  /**< Mode X8 for ADC_CTRL */
#define _ADC_CTRL_OVSRSEL_X16                              0x00000003UL                                  /**< Mode X16 for ADC_CTRL */
#define _ADC_CTRL_OVSRSEL_X32                              0x00000004UL                                  /**< Mode X32 for ADC_CTRL */
#define _ADC_CTRL_OVSRSEL_X64                              0x00000005UL                                  /**< Mode X64 for ADC_CTRL */
#define _ADC_CTRL_OVSRSEL_X128                             0x00000006UL                                  /**< Mode X128 for ADC_CTRL */
#define _ADC_CTRL_OVSRSEL_X256                             0x00000007UL                                  /**< Mode X256 for ADC_CTRL */
#define _ADC_CTRL_OVSRSEL_X512                             0x00000008UL                                  /**< Mode X512 for ADC_CTRL */
#define _ADC_CTRL_OVSRSEL_X1024                            0x00000009UL                                  /**< Mode X1024 for ADC_CTRL */
#define _ADC_CTRL_OVSRSEL_X2048                            0x0000000AUL                                  /**< Mode X2048 for ADC_CTRL */
#define _ADC_CTRL_OVSRSEL_X4096                            0x0000000BUL                                  /**< Mode X4096 for ADC_CTRL */
#define ADC_CTRL_OVSRSEL_DEFAULT                           (_ADC_CTRL_OVSRSEL_DEFAULT << 24)             /**< Shifted mode DEFAULT for ADC_CTRL */
#define ADC_CTRL_OVSRSEL_X2                                (_ADC_CTRL_OVSRSEL_X2 << 24)                  /**< Shifted mode X2 for ADC_CTRL */
#define ADC_CTRL_OVSRSEL_X4                                (_ADC_CTRL_OVSRSEL_X4 << 24)                  /**< Shifted mode X4 for ADC_CTRL */
#define ADC_CTRL_OVSRSEL_X8                                (_ADC_CTRL_OVSRSEL_X8 << 24)                  /**< Shifted mode X8 for ADC_CTRL */
#define ADC_CTRL_OVSRSEL_X16                               (_ADC_CTRL_OVSRSEL_X16 << 24)                 /**< Shifted mode X16 for ADC_CTRL */
#define ADC_CTRL_OVSRSEL_X32                               (_ADC_CTRL_OVSRSEL_X32 << 24)                 /**< Shifted mode X32 for ADC_CTRL */
#define ADC_CTRL_OVSRSEL_X64                               (_ADC_CTRL_OVSRSEL_X64 << 24)                 /**< Shifted mode X64 for ADC_CTRL */
#define ADC_CTRL_OVSRSEL_X128                              (_ADC_CTRL_OVSRSEL_X128 << 24)                /**< Shifted mode X128 for ADC_CTRL */
#define ADC_CTRL_OVSRSEL_X256                              (_ADC_CTRL_OVSRSEL_X256 << 24)                /**< Shifted mode X256 for ADC_CTRL */
#define ADC_CTRL_OVSRSEL_X512                              (_ADC_CTRL_OVSRSEL_X512 << 24)                /**< Shifted mode X512 for ADC_CTRL */
#define ADC_CTRL_OVSRSEL_X1024                             (_ADC_CTRL_OVSRSEL_X1024 << 24)               /**< Shifted mode X1024 for ADC_CTRL */
#define ADC_CTRL_OVSRSEL_X2048                             (_ADC_CTRL_OVSRSEL_X2048 << 24)               /**< Shifted mode X2048 for ADC_CTRL */
#define ADC_CTRL_OVSRSEL_X4096                             (_ADC_CTRL_OVSRSEL_X4096 << 24)               /**< Shifted mode X4096 for ADC_CTRL */
#define ADC_CTRL_DBGHALT                                   (0x1UL << 28)                                 /**< Debug Mode Halt Enable */
#define _ADC_CTRL_DBGHALT_SHIFT                            28                                            /**< Shift value for ADC_DBGHALT */
#define _ADC_CTRL_DBGHALT_MASK                             0x10000000UL                                  /**< Bit mask for ADC_DBGHALT */
#define _ADC_CTRL_DBGHALT_DEFAULT                          0x00000000UL                                  /**< Mode DEFAULT for ADC_CTRL */
#define ADC_CTRL_DBGHALT_DEFAULT                           (_ADC_CTRL_DBGHALT_DEFAULT << 28)             /**< Shifted mode DEFAULT for ADC_CTRL */
#define ADC_CTRL_CHCONMODE                                 (0x1UL << 29)                                 /**< Channel Connect */
#define _ADC_CTRL_CHCONMODE_SHIFT                          29                                            /**< Shift value for ADC_CHCONMODE */
#define _ADC_CTRL_CHCONMODE_MASK                           0x20000000UL                                  /**< Bit mask for ADC_CHCONMODE */
#define _ADC_CTRL_CHCONMODE_DEFAULT                        0x00000000UL                                  /**< Mode DEFAULT for ADC_CTRL */
#define _ADC_CTRL_CHCONMODE_MAXSETTLE                      0x00000000UL                                  /**< Mode MAXSETTLE for ADC_CTRL */
#define _ADC_CTRL_CHCONMODE_MAXRESP                        0x00000001UL                                  /**< Mode MAXRESP for ADC_CTRL */
#define ADC_CTRL_CHCONMODE_DEFAULT                         (_ADC_CTRL_CHCONMODE_DEFAULT << 29)           /**< Shifted mode DEFAULT for ADC_CTRL */
#define ADC_CTRL_CHCONMODE_MAXSETTLE                       (_ADC_CTRL_CHCONMODE_MAXSETTLE << 29)         /**< Shifted mode MAXSETTLE for ADC_CTRL */
#define ADC_CTRL_CHCONMODE_MAXRESP                         (_ADC_CTRL_CHCONMODE_MAXRESP << 29)           /**< Shifted mode MAXRESP for ADC_CTRL */
#define _ADC_CTRL_CHCONREFWARMIDLE_SHIFT                   30                                            /**< Shift value for ADC_CHCONREFWARMIDLE */
#define _ADC_CTRL_CHCONREFWARMIDLE_MASK                    0xC0000000UL                                  /**< Bit mask for ADC_CHCONREFWARMIDLE */
#define _ADC_CTRL_CHCONREFWARMIDLE_DEFAULT                 0x00000000UL                                  /**< Mode DEFAULT for ADC_CTRL */
#define _ADC_CTRL_CHCONREFWARMIDLE_PREFSCAN                0x00000000UL                                  /**< Mode PREFSCAN for ADC_CTRL */
#define _ADC_CTRL_CHCONREFWARMIDLE_PREFSINGLE              0x00000001UL                                  /**< Mode PREFSINGLE for ADC_CTRL */
#define _ADC_CTRL_CHCONREFWARMIDLE_KEEPPREV                0x00000002UL                                  /**< Mode KEEPPREV for ADC_CTRL */
#define ADC_CTRL_CHCONREFWARMIDLE_DEFAULT                  (_ADC_CTRL_CHCONREFWARMIDLE_DEFAULT << 30)    /**< Shifted mode DEFAULT for ADC_CTRL */
#define ADC_CTRL_CHCONREFWARMIDLE_PREFSCAN                 (_ADC_CTRL_CHCONREFWARMIDLE_PREFSCAN << 30)   /**< Shifted mode PREFSCAN for ADC_CTRL */
#define ADC_CTRL_CHCONREFWARMIDLE_PREFSINGLE               (_ADC_CTRL_CHCONREFWARMIDLE_PREFSINGLE << 30) /**< Shifted mode PREFSINGLE for ADC_CTRL */
#define ADC_CTRL_CHCONREFWARMIDLE_KEEPPREV                 (_ADC_CTRL_CHCONREFWARMIDLE_KEEPPREV << 30)   /**< Shifted mode KEEPPREV for ADC_CTRL */

/* Bit fields for ADC CMD */
#define _ADC_CMD_RESETVALUE                                0x00000000UL                        /**< Default value for ADC_CMD */
#define _ADC_CMD_MASK                                      0x0000000FUL                        /**< Mask for ADC_CMD */
#define ADC_CMD_SINGLESTART                                (0x1UL << 0)                        /**< Single Channel Conversion Start */
#define _ADC_CMD_SINGLESTART_SHIFT                         0                                   /**< Shift value for ADC_SINGLESTART */
#define _ADC_CMD_SINGLESTART_MASK                          0x1UL                               /**< Bit mask for ADC_SINGLESTART */
#define _ADC_CMD_SINGLESTART_DEFAULT                       0x00000000UL                        /**< Mode DEFAULT for ADC_CMD */
#define ADC_CMD_SINGLESTART_DEFAULT                        (_ADC_CMD_SINGLESTART_DEFAULT << 0) /**< Shifted mode DEFAULT for ADC_CMD */
#define ADC_CMD_SINGLESTOP                                 (0x1UL << 1)                        /**< Single Channel Conversion Stop */
#define _ADC_CMD_SINGLESTOP_SHIFT                          1                                   /**< Shift value for ADC_SINGLESTOP */
#define _ADC_CMD_SINGLESTOP_MASK                           0x2UL                               /**< Bit mask for ADC_SINGLESTOP */
#define _ADC_CMD_SINGLESTOP_DEFAULT                        0x00000000UL                        /**< Mode DEFAULT for ADC_CMD */
#define ADC_CMD_SINGLESTOP_DEFAULT                         (_ADC_CMD_SINGLESTOP_DEFAULT << 1)  /**< Shifted mode DEFAULT for ADC_CMD */
#define ADC_CMD_SCANSTART                                  (0x1UL << 2)                        /**< Scan Sequence Start */
#define _ADC_CMD_SCANSTART_SHIFT                           2                                   /**< Shift value for ADC_SCANSTART */
#define _ADC_CMD_SCANSTART_MASK                            0x4UL                               /**< Bit mask for ADC_SCANSTART */
#define _ADC_CMD_SCANSTART_DEFAULT                         0x00000000UL                        /**< Mode DEFAULT for ADC_CMD */
#define ADC_CMD_SCANSTART_DEFAULT                          (_ADC_CMD_SCANSTART_DEFAULT << 2)   /**< Shifted mode DEFAULT for ADC_CMD */
#define ADC_CMD_SCANSTOP                                   (0x1UL << 3)                        /**< Scan Sequence Stop */
#define _ADC_CMD_SCANSTOP_SHIFT                            3                                   /**< Shift value for ADC_SCANSTOP */
#define _ADC_CMD_SCANSTOP_MASK                             0x8UL                               /**< Bit mask for ADC_SCANSTOP */
#define _ADC_CMD_SCANSTOP_DEFAULT                          0x00000000UL                        /**< Mode DEFAULT for ADC_CMD */
#define ADC_CMD_SCANSTOP_DEFAULT                           (_ADC_CMD_SCANSTOP_DEFAULT << 3)    /**< Shifted mode DEFAULT for ADC_CMD */

/* Bit fields for ADC STATUS */
#define _ADC_STATUS_RESETVALUE                             0x00000000UL                             /**< Default value for ADC_STATUS */
#define _ADC_STATUS_MASK                                   0x00031F07UL                             /**< Mask for ADC_STATUS */
#define ADC_STATUS_SINGLEACT                               (0x1UL << 0)                             /**< Single Channel Conversion Active */
#define _ADC_STATUS_SINGLEACT_SHIFT                        0                                        /**< Shift value for ADC_SINGLEACT */
#define _ADC_STATUS_SINGLEACT_MASK                         0x1UL                                    /**< Bit mask for ADC_SINGLEACT */
#define _ADC_STATUS_SINGLEACT_DEFAULT                      0x00000000UL                             /**< Mode DEFAULT for ADC_STATUS */
#define ADC_STATUS_SINGLEACT_DEFAULT                       (_ADC_STATUS_SINGLEACT_DEFAULT << 0)     /**< Shifted mode DEFAULT for ADC_STATUS */
#define ADC_STATUS_SCANACT                                 (0x1UL << 1)                             /**< Scan Conversion Active */
#define _ADC_STATUS_SCANACT_SHIFT                          1                                        /**< Shift value for ADC_SCANACT */
#define _ADC_STATUS_SCANACT_MASK                           0x2UL                                    /**< Bit mask for ADC_SCANACT */
#define _ADC_STATUS_SCANACT_DEFAULT                        0x00000000UL                             /**< Mode DEFAULT for ADC_STATUS */
#define ADC_STATUS_SCANACT_DEFAULT                         (_ADC_STATUS_SCANACT_DEFAULT << 1)       /**< Shifted mode DEFAULT for ADC_STATUS */
#define ADC_STATUS_SCANPENDING                             (0x1UL << 2)                             /**< Scan Conversion Pending */
#define _ADC_STATUS_SCANPENDING_SHIFT                      2                                        /**< Shift value for ADC_SCANPENDING */
#define _ADC_STATUS_SCANPENDING_MASK                       0x4UL                                    /**< Bit mask for ADC_SCANPENDING */
#define _ADC_STATUS_SCANPENDING_DEFAULT                    0x00000000UL                             /**< Mode DEFAULT for ADC_STATUS */
#define ADC_STATUS_SCANPENDING_DEFAULT                     (_ADC_STATUS_SCANPENDING_DEFAULT << 2)   /**< Shifted mode DEFAULT for ADC_STATUS */
#define ADC_STATUS_SINGLEREFWARM                           (0x1UL << 8)                             /**< Single Channel Reference Warmed Up */
#define _ADC_STATUS_SINGLEREFWARM_SHIFT                    8                                        /**< Shift value for ADC_SINGLEREFWARM */
#define _ADC_STATUS_SINGLEREFWARM_MASK                     0x100UL                                  /**< Bit mask for ADC_SINGLEREFWARM */
#define _ADC_STATUS_SINGLEREFWARM_DEFAULT                  0x00000000UL                             /**< Mode DEFAULT for ADC_STATUS */
#define ADC_STATUS_SINGLEREFWARM_DEFAULT                   (_ADC_STATUS_SINGLEREFWARM_DEFAULT << 8) /**< Shifted mode DEFAULT for ADC_STATUS */
#define ADC_STATUS_SCANREFWARM                             (0x1UL << 9)                             /**< Scan Reference Warmed Up */
#define _ADC_STATUS_SCANREFWARM_SHIFT                      9                                        /**< Shift value for ADC_SCANREFWARM */
#define _ADC_STATUS_SCANREFWARM_MASK                       0x200UL                                  /**< Bit mask for ADC_SCANREFWARM */
#define _ADC_STATUS_SCANREFWARM_DEFAULT                    0x00000000UL                             /**< Mode DEFAULT for ADC_STATUS */
#define ADC_STATUS_SCANREFWARM_DEFAULT                     (_ADC_STATUS_SCANREFWARM_DEFAULT << 9)   /**< Shifted mode DEFAULT for ADC_STATUS */
#define _ADC_STATUS_PROGERR_SHIFT                          10                                       /**< Shift value for ADC_PROGERR */
#define _ADC_STATUS_PROGERR_MASK                           0xC00UL                                  /**< Bit mask for ADC_PROGERR */
#define _ADC_STATUS_PROGERR_DEFAULT                        0x00000000UL                             /**< Mode DEFAULT for ADC_STATUS */
#define _ADC_STATUS_PROGERR_BUSCONF                        0x00000001UL                             /**< Mode BUSCONF for ADC_STATUS */
#define _ADC_STATUS_PROGERR_NEGSELCONF                     0x00000002UL                             /**< Mode NEGSELCONF for ADC_STATUS */
#define ADC_STATUS_PROGERR_DEFAULT                         (_ADC_STATUS_PROGERR_DEFAULT << 10)      /**< Shifted mode DEFAULT for ADC_STATUS */
#define ADC_STATUS_PROGERR_BUSCONF                         (_ADC_STATUS_PROGERR_BUSCONF << 10)      /**< Shifted mode BUSCONF for ADC_STATUS */
#define ADC_STATUS_PROGERR_NEGSELCONF                      (_ADC_STATUS_PROGERR_NEGSELCONF << 10)   /**< Shifted mode NEGSELCONF for ADC_STATUS */
#define ADC_STATUS_WARM                                    (0x1UL << 12)                            /**< ADC Warmed Up */
#define _ADC_STATUS_WARM_SHIFT                             12                                       /**< Shift value for ADC_WARM */
#define _ADC_STATUS_WARM_MASK                              0x1000UL                                 /**< Bit mask for ADC_WARM */
#define _ADC_STATUS_WARM_DEFAULT                           0x00000000UL                             /**< Mode DEFAULT for ADC_STATUS */
#define ADC_STATUS_WARM_DEFAULT                            (_ADC_STATUS_WARM_DEFAULT << 12)         /**< Shifted mode DEFAULT for ADC_STATUS */
#define ADC_STATUS_SINGLEDV                                (0x1UL << 16)                            /**< Single Channel Data Valid */
#define _ADC_STATUS_SINGLEDV_SHIFT                         16                                       /**< Shift value for ADC_SINGLEDV */
#define _ADC_STATUS_SINGLEDV_MASK                          0x10000UL                                /**< Bit mask for ADC_SINGLEDV */
#define _ADC_STATUS_SINGLEDV_DEFAULT                       0x00000000UL                             /**< Mode DEFAULT for ADC_STATUS */
#define ADC_STATUS_SINGLEDV_DEFAULT                        (_ADC_STATUS_SINGLEDV_DEFAULT << 16)     /**< Shifted mode DEFAULT for ADC_STATUS */
#define ADC_STATUS_SCANDV                                  (0x1UL << 17)                            /**< Scan Data Valid */
#define _ADC_STATUS_SCANDV_SHIFT                           17                                       /**< Shift value for ADC_SCANDV */
#define _ADC_STATUS_SCANDV_MASK                            0x20000UL                                /**< Bit mask for ADC_SCANDV */
#define _ADC_STATUS_SCANDV_DEFAULT                         0x00000000UL                             /**< Mode DEFAULT for ADC_STATUS */
#define ADC_STATUS_SCANDV_DEFAULT                          (_ADC_STATUS_SCANDV_DEFAULT << 17)       /**< Shifted mode DEFAULT for ADC_STATUS */

/* Bit fields for ADC SINGLECTRL */
#define _ADC_SINGLECTRL_RESETVALUE                         0x00FFFF00UL                               /**< Default value for ADC_SINGLECTRL */
#define _ADC_SINGLECTRL_MASK                               0xAFFFFFFFUL                               /**< Mask for ADC_SINGLECTRL */
#define ADC_SINGLECTRL_REP                                 (0x1UL << 0)                               /**< Single Channel Repetitive Mode */
#define _ADC_SINGLECTRL_REP_SHIFT                          0                                          /**< Shift value for ADC_REP */
#define _ADC_SINGLECTRL_REP_MASK                           0x1UL                                      /**< Bit mask for ADC_REP */
#define _ADC_SINGLECTRL_REP_DEFAULT                        0x00000000UL                               /**< Mode DEFAULT for ADC_SINGLECTRL */
#define ADC_SINGLECTRL_REP_DEFAULT                         (_ADC_SINGLECTRL_REP_DEFAULT << 0)         /**< Shifted mode DEFAULT for ADC_SINGLECTRL */
#define ADC_SINGLECTRL_DIFF                                (0x1UL << 1)                               /**< Single Channel Differential Mode */
#define _ADC_SINGLECTRL_DIFF_SHIFT                         1                                          /**< Shift value for ADC_DIFF */
#define _ADC_SINGLECTRL_DIFF_MASK                          0x2UL                                      /**< Bit mask for ADC_DIFF */
#define _ADC_SINGLECTRL_DIFF_DEFAULT                       0x00000000UL                               /**< Mode DEFAULT for ADC_SINGLECTRL */
#define ADC_SINGLECTRL_DIFF_DEFAULT                        (_ADC_SINGLECTRL_DIFF_DEFAULT << 1)        /**< Shifted mode DEFAULT for ADC_SINGLECTRL */
#define ADC_SINGLECTRL_ADJ                                 (0x1UL << 2)                               /**< Single Channel Result Adjustment */
#define _ADC_SINGLECTRL_ADJ_SHIFT                          2                                          /**< Shift value for ADC_ADJ */
#define _ADC_SINGLECTRL_ADJ_MASK                           0x4UL                                      /**< Bit mask for ADC_ADJ */
#define _ADC_SINGLECTRL_ADJ_DEFAULT                        0x00000000UL                               /**< Mode DEFAULT for ADC_SINGLECTRL */
#define _ADC_SINGLECTRL_ADJ_RIGHT                          0x00000000UL                               /**< Mode RIGHT for ADC_SINGLECTRL */
#define _ADC_SINGLECTRL_ADJ_LEFT                           0x00000001UL                               /**< Mode LEFT for ADC_SINGLECTRL */
#define ADC_SINGLECTRL_ADJ_DEFAULT                         (_ADC_SINGLECTRL_ADJ_DEFAULT << 2)         /**< Shifted mode DEFAULT for ADC_SINGLECTRL */
#define ADC_SINGLECTRL_ADJ_RIGHT                           (_ADC_SINGLECTRL_ADJ_RIGHT << 2)           /**< Shifted mode RIGHT for ADC_SINGLECTRL */
#define ADC_SINGLECTRL_ADJ_LEFT                            (_ADC_SINGLECTRL_ADJ_LEFT << 2)            /**< Shifted mode LEFT for ADC_SINGLECTRL */
#define _ADC_SINGLECTRL_RES_SHIFT                          3                                          /**< Shift value for ADC_RES */
#define _ADC_SINGLECTRL_RES_MASK                           0x18UL                                     /**< Bit mask for ADC_RES */
#define _ADC_SINGLECTRL_RES_DEFAULT                        0x00000000UL                               /**< Mode DEFAULT for ADC_SINGLECTRL */
#define _ADC_SINGLECTRL_RES_12BIT                          0x00000000UL                               /**< Mode 12BIT for ADC_SINGLECTRL */
#define _ADC_SINGLECTRL_RES_8BIT                           0x00000001UL                               /**< Mode 8BIT for ADC_SINGLECTRL */
#define _ADC_SINGLECTRL_RES_6BIT                           0x00000002UL                               /**< Mode 6BIT for ADC_SINGLECTRL */
#define _ADC_SINGLECTRL_RES_OVS                            0x00000003UL                               /**< Mode OVS for ADC_SINGLECTRL */
#define ADC_SINGLECTRL_RES_DEFAULT                         (_ADC_SINGLECTRL_RES_DEFAULT << 3)         /**< Shifted mode DEFAULT for ADC_SINGLECTRL */
#define ADC_SINGLECTRL_RES_12BIT                           (_ADC_SINGLECTRL_RES_12BIT << 3)           /**< Shifted mode 12BIT for ADC_SINGLECTRL */
#define ADC_SINGLECTRL_RES_8BIT                            (_ADC_SINGLECTRL_RES_8BIT << 3)            /**< Shifted mode 8BIT for ADC_SINGLECTRL */
#define ADC_SINGLECTRL_RES_6BIT                            (_ADC_SINGLECTRL_RES_6BIT << 3)            /**< Shifted mode 6BIT for ADC_SINGLECTRL */
#define ADC_SINGLECTRL_RES_OVS                             (_ADC_SINGLECTRL_RES_OVS << 3)             /**< Shifted mode OVS for ADC_SINGLECTRL */
#define _ADC_SINGLECTRL_REF_SHIFT                          5                                          /**< Shift value for ADC_REF */
#define _ADC_SINGLECTRL_REF_MASK                           0xE0UL                                     /**< Bit mask for ADC_REF */
#define _ADC_SINGLECTRL_REF_DEFAULT                        0x00000000UL                               /**< Mode DEFAULT for ADC_SINGLECTRL */
#define _ADC_SINGLECTRL_REF_1V25                           0x00000000UL                               /**< Mode 1V25 for ADC_SINGLECTRL */
#define _ADC_SINGLECTRL_REF_2V5                            0x00000001UL                               /**< Mode 2V5 for ADC_SINGLECTRL */
#define _ADC_SINGLECTRL_REF_VDD                            0x00000002UL                               /**< Mode VDD for ADC_SINGLECTRL */
#define _ADC_SINGLECTRL_REF_5V                             0x00000003UL                               /**< Mode 5V for ADC_SINGLECTRL */
#define _ADC_SINGLECTRL_REF_EXTSINGLE                      0x00000004UL                               /**< Mode EXTSINGLE for ADC_SINGLECTRL */
#define _ADC_SINGLECTRL_REF_2XEXTDIFF                      0x00000005UL                               /**< Mode 2XEXTDIFF for ADC_SINGLECTRL */
#define _ADC_SINGLECTRL_REF_2XVDD                          0x00000006UL                               /**< Mode 2XVDD for ADC_SINGLECTRL */
#define _ADC_SINGLECTRL_REF_CONF                           0x00000007UL                               /**< Mode CONF for ADC_SINGLECTRL */
#define ADC_SINGLECTRL_REF_DEFAULT                         (_ADC_SINGLECTRL_REF_DEFAULT << 5)         /**< Shifted mode DEFAULT for ADC_SINGLECTRL */
#define ADC_SINGLECTRL_REF_1V25                            (_ADC_SINGLECTRL_REF_1V25 << 5)            /**< Shifted mode 1V25 for ADC_SINGLECTRL */
#define ADC_SINGLECTRL_REF_2V5                             (_ADC_SINGLECTRL_REF_2V5 << 5)             /**< Shifted mode 2V5 for ADC_SINGLECTRL */
#define ADC_SINGLECTRL_REF_VDD                             (_ADC_SINGLECTRL_REF_VDD << 5)             /**< Shifted mode VDD for ADC_SINGLECTRL */
#define ADC_SINGLECTRL_REF_5V                              (_ADC_SINGLECTRL_REF_5V << 5)              /**< Shifted mode 5V for ADC_SINGLECTRL */
#define ADC_SINGLECTRL_REF_EXTSINGLE                       (_ADC_SINGLECTRL_REF_EXTSINGLE << 5)       /**< Shifted mode EXTSINGLE for ADC_SINGLECTRL */
#define ADC_SINGLECTRL_REF_2XEXTDIFF                       (_ADC_SINGLECTRL_REF_2XEXTDIFF << 5)       /**< Shifted mode 2XEXTDIFF for ADC_SINGLECTRL */
#define ADC_SINGLECTRL_REF_2XVDD                           (_ADC_SINGLECTRL_REF_2XVDD << 5)           /**< Shifted mode 2XVDD for ADC_SINGLECTRL */
#define ADC_SINGLECTRL_REF_CONF                            (_ADC_SINGLECTRL_REF_CONF << 5)            /**< Shifted mode CONF for ADC_SINGLECTRL */
#define _ADC_SINGLECTRL_POSSEL_SHIFT                       8                                          /**< Shift value for ADC_POSSEL */
#define _ADC_SINGLECTRL_POSSEL_MASK                        0xFF00UL                                   /**< Bit mask for ADC_POSSEL */
#define _ADC_SINGLECTRL_POSSEL_APORT0XCH0                  0x00000000UL                               /**< Mode APORT0XCH0 for ADC_SINGLECTRL */
#define _ADC_SINGLECTRL_POSSEL_APORT0XCH1                  0x00000001UL                               /**< Mode APORT0XCH1 for ADC_SINGLECTRL */
#define _ADC_SINGLECTRL_POSSEL_APORT0XCH2                  0x00000002UL                               /**< Mode APORT0XCH2 for ADC_SINGLECTRL */
#define _ADC_SINGLECTRL_POSSEL_APORT0XCH3                  0x00000003UL                               /**< Mode APORT0XCH3 for ADC_SINGLECTRL */
#define _ADC_SINGLECTRL_POSSEL_APORT0XCH4                  0x00000004UL                               /**< Mode APORT0XCH4 for ADC_SINGLECTRL */
#define _ADC_SINGLECTRL_POSSEL_APORT0XCH5                  0x00000005UL                               /**< Mode APORT0XCH5 for ADC_SINGLECTRL */
#define _ADC_SINGLECTRL_POSSEL_APORT0XCH6                  0x00000006UL                               /**< Mode APORT0XCH6 for ADC_SINGLECTRL */
#define _ADC_SINGLECTRL_POSSEL_APORT0XCH7                  0x00000007UL                               /**< Mode APORT0XCH7 for ADC_SINGLECTRL */
#define _ADC_SINGLECTRL_POSSEL_APORT0XCH8                  0x00000008UL                               /**< Mode APORT0XCH8 for ADC_SINGLECTRL */
#define _ADC_SINGLECTRL_POSSEL_APORT0XCH9                  0x00000009UL                               /**< Mode APORT0XCH9 for ADC_SINGLECTRL */
#define _ADC_SINGLECTRL_POSSEL_APORT0XCH10                 0x0000000AUL                               /**< Mode APORT0XCH10 for ADC_SINGLECTRL */
#define _ADC_SINGLECTRL_POSSEL_APORT0XCH11                 0x0000000BUL                               /**< Mode APORT0XCH11 for ADC_SINGLECTRL */
#define _ADC_SINGLECTRL_POSSEL_APORT0XCH12                 0x0000000CUL                               /**< Mode APORT0XCH12 for ADC_SINGLECTRL */
#define _ADC_SINGLECTRL_POSSEL_APORT0XCH13                 0x0000000DUL                               /**< Mode APORT0XCH13 for ADC_SINGLECTRL */
#define _ADC_SINGLECTRL_POSSEL_APORT0XCH14                 0x0000000EUL                               /**< Mode APORT0XCH14 for ADC_SINGLECTRL */
#define _ADC_SINGLECTRL_POSSEL_APORT0XCH15                 0x0000000FUL                               /**< Mode APORT0XCH15 for ADC_SINGLECTRL */
#define _ADC_SINGLECTRL_POSSEL_APORT0YCH0                  0x00000010UL                               /**< Mode APORT0YCH0 for ADC_SINGLECTRL */
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
#define _ADC_SINGLECTRL_POSSEL_APORT4XCH17                 0x00000091UL                               /**< Mode APORT4XCH17 for ADC_SINGLECTRL */
#define _ADC_SINGLECTRL_POSSEL_APORT4YCH18                 0x00000092UL                               /**< Mode APORT4YCH18 for ADC_SINGLECTRL */
#define _ADC_SINGLECTRL_POSSEL_APORT4XCH19                 0x00000093UL                               /**< Mode APORT4XCH19 for ADC_SINGLECTRL */
#define _ADC_SINGLECTRL_POSSEL_APORT4YCH20                 0x00000094UL                               /**< Mode APORT4YCH20 for ADC_SINGLECTRL */
#define _ADC_SINGLECTRL_POSSEL_APORT4XCH21                 0x00000095UL                               /**< Mode APORT4XCH21 for ADC_SINGLECTRL */
#define _ADC_SINGLECTRL_POSSEL_APORT4YCH22                 0x00000096UL                               /**< Mode APORT4YCH22 for ADC_SINGLECTRL */
#define _ADC_SINGLECTRL_POSSEL_APORT4XCH23                 0x00000097UL                               /**< Mode APORT4XCH23 for ADC_SINGLECTRL */
#define _ADC_SINGLECTRL_POSSEL_APORT4YCH24                 0x00000098UL                               /**< Mode APORT4YCH24 for ADC_SINGLECTRL */
#define _ADC_SINGLECTRL_POSSEL_APORT4XCH25                 0x00000099UL                               /**< Mode APORT4XCH25 for ADC_SINGLECTRL */
#define _ADC_SINGLECTRL_POSSEL_APORT4YCH26                 0x0000009AUL                               /**< Mode APORT4YCH26 for ADC_SINGLECTRL */
#define _ADC_SINGLECTRL_POSSEL_APORT4XCH27                 0x0000009BUL                               /**< Mode APORT4XCH27 for ADC_SINGLECTRL */
#define _ADC_SINGLECTRL_POSSEL_APORT4YCH28                 0x0000009CUL                               /**< Mode APORT4YCH28 for ADC_SINGLECTRL */
#define _ADC_SINGLECTRL_POSSEL_APORT4XCH29                 0x0000009DUL                               /**< Mode APORT4XCH29 for ADC_SINGLECTRL */
#define _ADC_SINGLECTRL_POSSEL_APORT4YCH30                 0x0000009EUL                               /**< Mode APORT4YCH30 for ADC_SINGLECTRL */
#define _ADC_SINGLECTRL_POSSEL_APORT4XCH31                 0x0000009FUL                               /**< Mode APORT4XCH31 for ADC_SINGLECTRL */
#define _ADC_SINGLECTRL_POSSEL_AVDD                        0x000000E0UL                               /**< Mode AVDD for ADC_SINGLECTRL */
#define _ADC_SINGLECTRL_POSSEL_BU                          0x000000E1UL                               /**< Mode BU for ADC_SINGLECTRL */
#define _ADC_SINGLECTRL_POSSEL_AREG                        0x000000E2UL                               /**< Mode AREG for ADC_SINGLECTRL */
#define _ADC_SINGLECTRL_POSSEL_VREGOUTPA                   0x000000E3UL                               /**< Mode VREGOUTPA for ADC_SINGLECTRL */
#define _ADC_SINGLECTRL_POSSEL_PDBU                        0x000000E4UL                               /**< Mode PDBU for ADC_SINGLECTRL */
#define _ADC_SINGLECTRL_POSSEL_IO0                         0x000000E5UL                               /**< Mode IO0 for ADC_SINGLECTRL */
#define _ADC_SINGLECTRL_POSSEL_IO1                         0x000000E6UL                               /**< Mode IO1 for ADC_SINGLECTRL */
#define _ADC_SINGLECTRL_POSSEL_VSP                         0x000000E7UL                               /**< Mode VSP for ADC_SINGLECTRL */
#define _ADC_SINGLECTRL_POSSEL_OPA2                        0x000000F2UL                               /**< Mode OPA2 for ADC_SINGLECTRL */
#define _ADC_SINGLECTRL_POSSEL_TEMP                        0x000000F3UL                               /**< Mode TEMP for ADC_SINGLECTRL */
#define _ADC_SINGLECTRL_POSSEL_DAC0OUT0                    0x000000F4UL                               /**< Mode DAC0OUT0 for ADC_SINGLECTRL */
#define _ADC_SINGLECTRL_POSSEL_R5VOUT                      0x000000F5UL                               /**< Mode R5VOUT for ADC_SINGLECTRL */
#define _ADC_SINGLECTRL_POSSEL_SP1                         0x000000F6UL                               /**< Mode SP1 for ADC_SINGLECTRL */
#define _ADC_SINGLECTRL_POSSEL_SP2                         0x000000F7UL                               /**< Mode SP2 for ADC_SINGLECTRL */
#define _ADC_SINGLECTRL_POSSEL_DAC0OUT1                    0x000000F8UL                               /**< Mode DAC0OUT1 for ADC_SINGLECTRL */
#define _ADC_SINGLECTRL_POSSEL_SUBLSB                      0x000000F9UL                               /**< Mode SUBLSB for ADC_SINGLECTRL */
#define _ADC_SINGLECTRL_POSSEL_OPA3                        0x000000FAUL                               /**< Mode OPA3 for ADC_SINGLECTRL */
#define _ADC_SINGLECTRL_POSSEL_DEFAULT                     0x000000FFUL                               /**< Mode DEFAULT for ADC_SINGLECTRL */
#define _ADC_SINGLECTRL_POSSEL_VSS                         0x000000FFUL                               /**< Mode VSS for ADC_SINGLECTRL */
#define ADC_SINGLECTRL_POSSEL_APORT0XCH0                   (_ADC_SINGLECTRL_POSSEL_APORT0XCH0 << 8)   /**< Shifted mode APORT0XCH0 for ADC_SINGLECTRL */
#define ADC_SINGLECTRL_POSSEL_APORT0XCH1                   (_ADC_SINGLECTRL_POSSEL_APORT0XCH1 << 8)   /**< Shifted mode APORT0XCH1 for ADC_SINGLECTRL */
#define ADC_SINGLECTRL_POSSEL_APORT0XCH2                   (_ADC_SINGLECTRL_POSSEL_APORT0XCH2 << 8)   /**< Shifted mode APORT0XCH2 for ADC_SINGLECTRL */
#define ADC_SINGLECTRL_POSSEL_APORT0XCH3                   (_ADC_SINGLECTRL_POSSEL_APORT0XCH3 << 8)   /**< Shifted mode APORT0XCH3 for ADC_SINGLECTRL */
#define ADC_SINGLECTRL_POSSEL_APORT0XCH4                   (_ADC_SINGLECTRL_POSSEL_APORT0XCH4 << 8)   /**< Shifted mode APORT0XCH4 for ADC_SINGLECTRL */
#define ADC_SINGLECTRL_POSSEL_APORT0XCH5                   (_ADC_SINGLECTRL_POSSEL_APORT0XCH5 << 8)   /**< Shifted mode APORT0XCH5 for ADC_SINGLECTRL */
#define ADC_SINGLECTRL_POSSEL_APORT0XCH6                   (_ADC_SINGLECTRL_POSSEL_APORT0XCH6 << 8)   /**< Shifted mode APORT0XCH6 for ADC_SINGLECTRL */
#define ADC_SINGLECTRL_POSSEL_APORT0XCH7                   (_ADC_SINGLECTRL_POSSEL_APORT0XCH7 << 8)   /**< Shifted mode APORT0XCH7 for ADC_SINGLECTRL */
#define ADC_SINGLECTRL_POSSEL_APORT0XCH8                   (_ADC_SINGLECTRL_POSSEL_APORT0XCH8 << 8)   /**< Shifted mode APORT0XCH8 for ADC_SINGLECTRL */
#define ADC_SINGLECTRL_POSSEL_APORT0XCH9                   (_ADC_SINGLECTRL_POSSEL_APORT0XCH9 << 8)   /**< Shifted mode APORT0XCH9 for ADC_SINGLECTRL */
#define ADC_SINGLECTRL_POSSEL_APORT0XCH10                  (_ADC_SINGLECTRL_POSSEL_APORT0XCH10 << 8)  /**< Shifted mode APORT0XCH10 for ADC_SINGLECTRL */
#define ADC_SINGLECTRL_POSSEL_APORT0XCH11                  (_ADC_SINGLECTRL_POSSEL_APORT0XCH11 << 8)  /**< Shifted mode APORT0XCH11 for ADC_SINGLECTRL */
#define ADC_SINGLECTRL_POSSEL_APORT0XCH12                  (_ADC_SINGLECTRL_POSSEL_APORT0XCH12 << 8)  /**< Shifted mode APORT0XCH12 for ADC_SINGLECTRL */
#define ADC_SINGLECTRL_POSSEL_APORT0XCH13                  (_ADC_SINGLECTRL_POSSEL_APORT0XCH13 << 8)  /**< Shifted mode APORT0XCH13 for ADC_SINGLECTRL */
#define ADC_SINGLECTRL_POSSEL_APORT0XCH14                  (_ADC_SINGLECTRL_POSSEL_APORT0XCH14 << 8)  /**< Shifted mode APORT0XCH14 for ADC_SINGLECTRL */
#define ADC_SINGLECTRL_POSSEL_APORT0XCH15                  (_ADC_SINGLECTRL_POSSEL_APORT0XCH15 << 8)  /**< Shifted mode APORT0XCH15 for ADC_SINGLECTRL */
#define ADC_SINGLECTRL_POSSEL_APORT0YCH0                   (_ADC_SINGLECTRL_POSSEL_APORT0YCH0 << 8)   /**< Shifted mode APORT0YCH0 for ADC_SINGLECTRL */
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
#define ADC_SINGLECTRL_POSSEL_APORT4XCH31                  (_ADC_SINGLECTRL_POSSEL_APORT4XCH31 << 8)  /**< Shifted mode APORT4XCH31 for ADC_SINGLECTRL */
#define ADC_SINGLECTRL_POSSEL_AVDD                         (_ADC_SINGLECTRL_POSSEL_AVDD << 8)         /**< Shifted mode AVDD for ADC_SINGLECTRL */
#define ADC_SINGLECTRL_POSSEL_BU                           (_ADC_SINGLECTRL_POSSEL_BU << 8)           /**< Shifted mode BU for ADC_SINGLECTRL */
#define ADC_SINGLECTRL_POSSEL_AREG                         (_ADC_SINGLECTRL_POSSEL_AREG << 8)         /**< Shifted mode AREG for ADC_SINGLECTRL */
#define ADC_SINGLECTRL_POSSEL_VREGOUTPA                    (_ADC_SINGLECTRL_POSSEL_VREGOUTPA << 8)    /**< Shifted mode VREGOUTPA for ADC_SINGLECTRL */
#define ADC_SINGLECTRL_POSSEL_PDBU                         (_ADC_SINGLECTRL_POSSEL_PDBU << 8)         /**< Shifted mode PDBU for ADC_SINGLECTRL */
#define ADC_SINGLECTRL_POSSEL_IO0                          (_ADC_SINGLECTRL_POSSEL_IO0 << 8)          /**< Shifted mode IO0 for ADC_SINGLECTRL */
#define ADC_SINGLECTRL_POSSEL_IO1                          (_ADC_SINGLECTRL_POSSEL_IO1 << 8)          /**< Shifted mode IO1 for ADC_SINGLECTRL */
#define ADC_SINGLECTRL_POSSEL_VSP                          (_ADC_SINGLECTRL_POSSEL_VSP << 8)          /**< Shifted mode VSP for ADC_SINGLECTRL */
#define ADC_SINGLECTRL_POSSEL_OPA2                         (_ADC_SINGLECTRL_POSSEL_OPA2 << 8)         /**< Shifted mode OPA2 for ADC_SINGLECTRL */
#define ADC_SINGLECTRL_POSSEL_TEMP                         (_ADC_SINGLECTRL_POSSEL_TEMP << 8)         /**< Shifted mode TEMP for ADC_SINGLECTRL */
#define ADC_SINGLECTRL_POSSEL_DAC0OUT0                     (_ADC_SINGLECTRL_POSSEL_DAC0OUT0 << 8)     /**< Shifted mode DAC0OUT0 for ADC_SINGLECTRL */
#define ADC_SINGLECTRL_POSSEL_R5VOUT                       (_ADC_SINGLECTRL_POSSEL_R5VOUT << 8)       /**< Shifted mode R5VOUT for ADC_SINGLECTRL */
#define ADC_SINGLECTRL_POSSEL_SP1                          (_ADC_SINGLECTRL_POSSEL_SP1 << 8)          /**< Shifted mode SP1 for ADC_SINGLECTRL */
#define ADC_SINGLECTRL_POSSEL_SP2                          (_ADC_SINGLECTRL_POSSEL_SP2 << 8)          /**< Shifted mode SP2 for ADC_SINGLECTRL */
#define ADC_SINGLECTRL_POSSEL_DAC0OUT1                     (_ADC_SINGLECTRL_POSSEL_DAC0OUT1 << 8)     /**< Shifted mode DAC0OUT1 for ADC_SINGLECTRL */
#define ADC_SINGLECTRL_POSSEL_SUBLSB                       (_ADC_SINGLECTRL_POSSEL_SUBLSB << 8)       /**< Shifted mode SUBLSB for ADC_SINGLECTRL */
#define ADC_SINGLECTRL_POSSEL_OPA3                         (_ADC_SINGLECTRL_POSSEL_OPA3 << 8)         /**< Shifted mode OPA3 for ADC_SINGLECTRL */
#define ADC_SINGLECTRL_POSSEL_DEFAULT                      (_ADC_SINGLECTRL_POSSEL_DEFAULT << 8)      /**< Shifted mode DEFAULT for ADC_SINGLECTRL */
#define ADC_SINGLECTRL_POSSEL_VSS                          (_ADC_SINGLECTRL_POSSEL_VSS << 8)          /**< Shifted mode VSS for ADC_SINGLECTRL */
#define _ADC_SINGLECTRL_NEGSEL_SHIFT                       16                                         /**< Shift value for ADC_NEGSEL */
#define _ADC_SINGLECTRL_NEGSEL_MASK                        0xFF0000UL                                 /**< Bit mask for ADC_NEGSEL */
#define _ADC_SINGLECTRL_NEGSEL_APORT0XCH0                  0x00000000UL                               /**< Mode APORT0XCH0 for ADC_SINGLECTRL */
#define _ADC_SINGLECTRL_NEGSEL_APORT0XCH1                  0x00000001UL                               /**< Mode APORT0XCH1 for ADC_SINGLECTRL */
#define _ADC_SINGLECTRL_NEGSEL_APORT0XCH2                  0x00000002UL                               /**< Mode APORT0XCH2 for ADC_SINGLECTRL */
#define _ADC_SINGLECTRL_NEGSEL_APORT0XCH3                  0x00000003UL                               /**< Mode APORT0XCH3 for ADC_SINGLECTRL */
#define _ADC_SINGLECTRL_NEGSEL_APORT0XCH4                  0x00000004UL                               /**< Mode APORT0XCH4 for ADC_SINGLECTRL */
#define _ADC_SINGLECTRL_NEGSEL_APORT0XCH5                  0x00000005UL                               /**< Mode APORT0XCH5 for ADC_SINGLECTRL */
#define _ADC_SINGLECTRL_NEGSEL_APORT0XCH6                  0x00000006UL                               /**< Mode APORT0XCH6 for ADC_SINGLECTRL */
#define _ADC_SINGLECTRL_NEGSEL_APORT0XCH7                  0x00000007UL                               /**< Mode APORT0XCH7 for ADC_SINGLECTRL */
#define _ADC_SINGLECTRL_NEGSEL_APORT0XCH8                  0x00000008UL                               /**< Mode APORT0XCH8 for ADC_SINGLECTRL */
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
#define _ADC_SINGLECTRL_NEGSEL_APORT4XCH29                 0x0000009DUL                               /**< Mode APORT4XCH29 for ADC_SINGLECTRL */
#define _ADC_SINGLECTRL_NEGSEL_APORT4YCH30                 0x0000009EUL                               /**< Mode APORT4YCH30 for ADC_SINGLECTRL */
#define _ADC_SINGLECTRL_NEGSEL_APORT4XCH31                 0x0000009FUL                               /**< Mode APORT4XCH31 for ADC_SINGLECTRL */
#define _ADC_SINGLECTRL_NEGSEL_TESTN                       0x000000F5UL                               /**< Mode TESTN for ADC_SINGLECTRL */
#define _ADC_SINGLECTRL_NEGSEL_DEFAULT                     0x000000FFUL                               /**< Mode DEFAULT for ADC_SINGLECTRL */
#define _ADC_SINGLECTRL_NEGSEL_VSS                         0x000000FFUL                               /**< Mode VSS for ADC_SINGLECTRL */
#define ADC_SINGLECTRL_NEGSEL_APORT0XCH0                   (_ADC_SINGLECTRL_NEGSEL_APORT0XCH0 << 16)  /**< Shifted mode APORT0XCH0 for ADC_SINGLECTRL */
#define ADC_SINGLECTRL_NEGSEL_APORT0XCH1                   (_ADC_SINGLECTRL_NEGSEL_APORT0XCH1 << 16)  /**< Shifted mode APORT0XCH1 for ADC_SINGLECTRL */
#define ADC_SINGLECTRL_NEGSEL_APORT0XCH2                   (_ADC_SINGLECTRL_NEGSEL_APORT0XCH2 << 16)  /**< Shifted mode APORT0XCH2 for ADC_SINGLECTRL */
#define ADC_SINGLECTRL_NEGSEL_APORT0XCH3                   (_ADC_SINGLECTRL_NEGSEL_APORT0XCH3 << 16)  /**< Shifted mode APORT0XCH3 for ADC_SINGLECTRL */
#define ADC_SINGLECTRL_NEGSEL_APORT0XCH4                   (_ADC_SINGLECTRL_NEGSEL_APORT0XCH4 << 16)  /**< Shifted mode APORT0XCH4 for ADC_SINGLECTRL */
#define ADC_SINGLECTRL_NEGSEL_APORT0XCH5                   (_ADC_SINGLECTRL_NEGSEL_APORT0XCH5 << 16)  /**< Shifted mode APORT0XCH5 for ADC_SINGLECTRL */
#define ADC_SINGLECTRL_NEGSEL_APORT0XCH6                   (_ADC_SINGLECTRL_NEGSEL_APORT0XCH6 << 16)  /**< Shifted mode APORT0XCH6 for ADC_SINGLECTRL */
#define ADC_SINGLECTRL_NEGSEL_APORT0XCH7                   (_ADC_SINGLECTRL_NEGSEL_APORT0XCH7 << 16)  /**< Shifted mode APORT0XCH7 for ADC_SINGLECTRL */
#define ADC_SINGLECTRL_NEGSEL_APORT0XCH8                   (_ADC_SINGLECTRL_NEGSEL_APORT0XCH8 << 16)  /**< Shifted mode APORT0XCH8 for ADC_SINGLECTRL */
#define ADC_SINGLECTRL_NEGSEL_APORT0XCH9                   (_ADC_SINGLECTRL_NEGSEL_APORT0XCH9 << 16)  /**< Shifted mode APORT0XCH9 for ADC_SINGLECTRL */
#define ADC_SINGLECTRL_NEGSEL_APORT0XCH10                  (_ADC_SINGLECTRL_NEGSEL_APORT0XCH10 << 16) /**< Shifted mode APORT0XCH10 for ADC_SINGLECTRL */
#define ADC_SINGLECTRL_NEGSEL_APORT0XCH11                  (_ADC_SINGLECTRL_NEGSEL_APORT0XCH11 << 16) /**< Shifted mode APORT0XCH11 for ADC_SINGLECTRL */
#define ADC_SINGLECTRL_NEGSEL_APORT0XCH12                  (_ADC_SINGLECTRL_NEGSEL_APORT0XCH12 << 16) /**< Shifted mode APORT0XCH12 for ADC_SINGLECTRL */
#define ADC_SINGLECTRL_NEGSEL_APORT0XCH13                  (_ADC_SINGLECTRL_NEGSEL_APORT0XCH13 << 16) /**< Shifted mode APORT0XCH13 for ADC_SINGLECTRL */
#define ADC_SINGLECTRL_NEGSEL_APORT0XCH14                  (_ADC_SINGLECTRL_NEGSEL_APORT0XCH14 << 16) /**< Shifted mode APORT0XCH14 for ADC_SINGLECTRL */
#define ADC_SINGLECTRL_NEGSEL_APORT0XCH15                  (_ADC_SINGLECTRL_NEGSEL_APORT0XCH15 << 16) /**< Shifted mode APORT0XCH15 for ADC_SINGLECTRL */
#define ADC_SINGLECTRL_NEGSEL_APORT0YCH0                   (_ADC_SINGLECTRL_NEGSEL_APORT0YCH0 << 16)  /**< Shifted mode APORT0YCH0 for ADC_SINGLECTRL */
#define ADC_SINGLECTRL_NEGSEL_APORT0YCH1                   (_ADC_SINGLECTRL_NEGSEL_APORT0YCH1 << 16)  /**< Shifted mode APORT0YCH1 for ADC_SINGLECTRL */
#define ADC_SINGLECTRL_NEGSEL_APORT0YCH2                   (_ADC_SINGLECTRL_NEGSEL_APORT0YCH2 << 16)  /**< Shifted mode APORT0YCH2 for ADC_SINGLECTRL */
#define ADC_SINGLECTRL_NEGSEL_APORT0YCH3                   (_ADC_SINGLECTRL_NEGSEL_APORT0YCH3 << 16)  /**< Shifted mode APORT0YCH3 for ADC_SINGLECTRL */
#define ADC_SINGLECTRL_NEGSEL_APORT0YCH4                   (_ADC_SINGLECTRL_NEGSEL_APORT0YCH4 << 16)  /**< Shifted mode APORT0YCH4 for ADC_SINGLECTRL */
#define ADC_SINGLECTRL_NEGSEL_APORT0YCH5                   (_ADC_SINGLECTRL_NEGSEL_APORT0YCH5 << 16)  /**< Shifted mode APORT0YCH5 for ADC_SINGLECTRL */
#define ADC_SINGLECTRL_NEGSEL_APORT0YCH6                   (_ADC_SINGLECTRL_NEGSEL_APORT0YCH6 << 16)  /**< Shifted mode APORT0YCH6 for ADC_SINGLECTRL */
#define ADC_SINGLECTRL_NEGSEL_APORT0YCH7                   (_ADC_SINGLECTRL_NEGSEL_APORT0YCH7 << 16)  /**< Shifted mode APORT0YCH7 for ADC_SINGLECTRL */
#define ADC_SINGLECTRL_NEGSEL_APORT0YCH8                   (_ADC_SINGLECTRL_NEGSEL_APORT0YCH8 << 16)  /**< Shifted mode APORT0YCH8 for ADC_SINGLECTRL */
#define ADC_SINGLECTRL_NEGSEL_APORT0YCH9                   (_ADC_SINGLECTRL_NEGSEL_APORT0YCH9 << 16)  /**< Shifted mode APORT0YCH9 for ADC_SINGLECTRL */
#define ADC_SINGLECTRL_NEGSEL_APORT0YCH10                  (_ADC_SINGLECTRL_NEGSEL_APORT0YCH10 << 16) /**< Shifted mode APORT0YCH10 for ADC_SINGLECTRL */
#define ADC_SINGLECTRL_NEGSEL_APORT0YCH11                  (_ADC_SINGLECTRL_NEGSEL_APORT0YCH11 << 16) /**< Shifted mode APORT0YCH11 for ADC_SINGLECTRL */
#define ADC_SINGLECTRL_NEGSEL_APORT0YCH12                  (_ADC_SINGLECTRL_NEGSEL_APORT0YCH12 << 16) /**< Shifted mode APORT0YCH12 for ADC_SINGLECTRL */
#define ADC_SINGLECTRL_NEGSEL_APORT0YCH13                  (_ADC_SINGLECTRL_NEGSEL_APORT0YCH13 << 16) /**< Shifted mode APORT0YCH13 for ADC_SINGLECTRL */
#define ADC_SINGLECTRL_NEGSEL_APORT0YCH14                  (_ADC_SINGLECTRL_NEGSEL_APORT0YCH14 << 16) /**< Shifted mode APORT0YCH14 for ADC_SINGLECTRL */
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
