shsa5563/Ring-WearTech/Firmware/soc-smartPhone_NoBuff/inc/efr32bg13p_cmu.h

/**************************************************************************//**
 * @file efr32bg13p_cmu.h
 * @brief EFR32BG13P_CMU register and bit field definitions
 * @version 5.3.2
 ******************************************************************************
 * # License
 * <b>Copyright 2017 Silicon Laboratories, Inc. http://www.silabs.com</b>
 ******************************************************************************
 *
 * Permission is granted to anyone to use this software for any purpose,
 * including commercial applications, and to alter it and redistribute it
 * freely, subject to the following restrictions:
 *
 * 1. The origin of this software must not be misrepresented; you must not
 *    claim that you wrote the original software.@n
 * 2. Altered source versions must be plainly marked as such, and must not be
 *    misrepresented as being the original software.@n
 * 3. This notice may not be removed or altered from any source distribution.
 *
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
 * Silicon Laboratories, Inc. will not be liable for any consequential,
 * incidental, or special damages, or any other relief, or for any claim by
 * any third party, arising from your use of this Software.
 *
 *****************************************************************************/

#if defined(__ICCARM__)
#pragma system_include       /* Treat file as system include file. */
#elif defined(__ARMCC_VERSION) && (__ARMCC_VERSION >= 6010050)
#pragma clang system_header  /* Treat file as system include file. */
#endif

/**************************************************************************//**
* @addtogroup Parts
* @{
******************************************************************************/
/**************************************************************************//**
 * @defgroup EFR32BG13P_CMU CMU
 * @{
 * @brief EFR32BG13P_CMU Register Declaration
 *****************************************************************************/
/** CMU Register Declaration */
typedef struct {
  __IOM uint32_t CTRL;                /**< CMU Control Register  */

  uint32_t       RESERVED0[3];        /**< Reserved for future use **/
  __IOM uint32_t HFRCOCTRL;           /**< HFRCO Control Register  */

  uint32_t       RESERVED1[1];        /**< Reserved for future use **/
  __IOM uint32_t AUXHFRCOCTRL;        /**< AUXHFRCO Control Register  */

  uint32_t       RESERVED2[1];        /**< Reserved for future use **/
  __IOM uint32_t LFRCOCTRL;           /**< LFRCO Control Register  */
  __IOM uint32_t HFXOCTRL;            /**< HFXO Control Register  */

  uint32_t       RESERVED3[1];        /**< Reserved for future use **/
  __IOM uint32_t HFXOSTARTUPCTRL;     /**< HFXO Startup Control  */
  __IOM uint32_t HFXOSTEADYSTATECTRL; /**< HFXO Steady State control  */
  __IOM uint32_t HFXOTIMEOUTCTRL;     /**< HFXO Timeout Control  */
  __IOM uint32_t LFXOCTRL;            /**< LFXO Control Register  */

  uint32_t       RESERVED4[1];        /**< Reserved for future use **/
  __IOM uint32_t DPLLCTRL;            /**< DPLL Control Register  */
  __IOM uint32_t DPLLCTRL1;           /**< DPLL Control Register  */
  uint32_t       RESERVED5[2];        /**< Reserved for future use **/
  __IOM uint32_t CALCTRL;             /**< Calibration Control Register  */
  __IOM uint32_t CALCNT;              /**< Calibration Counter Register  */
  uint32_t       RESERVED6[2];        /**< Reserved for future use **/
  __IOM uint32_t OSCENCMD;            /**< Oscillator Enable/Disable Command Register  */
  __IOM uint32_t CMD;                 /**< Command Register  */
  uint32_t       RESERVED7[2];        /**< Reserved for future use **/
  __IOM uint32_t DBGCLKSEL;           /**< Debug Trace Clock Select  */
  __IOM uint32_t HFCLKSEL;            /**< High Frequency Clock Select Command Register  */
  uint32_t       RESERVED8[2];        /**< Reserved for future use **/
  __IOM uint32_t LFACLKSEL;           /**< Low Frequency A Clock Select Register  */
  __IOM uint32_t LFBCLKSEL;           /**< Low Frequency B Clock Select Register  */
  __IOM uint32_t LFECLKSEL;           /**< Low Frequency E Clock Select Register  */

  uint32_t       RESERVED9[1];        /**< Reserved for future use **/
  __IM uint32_t  STATUS;              /**< Status Register  */
  __IM uint32_t  HFCLKSTATUS;         /**< HFCLK Status Register  */
  uint32_t       RESERVED10[1];       /**< Reserved for future use **/
  __IM uint32_t  HFXOTRIMSTATUS;      /**< HFXO Trim Status  */
  __IM uint32_t  IF;                  /**< Interrupt Flag Register  */
  __IOM uint32_t IFS;                 /**< Interrupt Flag Set Register  */
  __IOM uint32_t IFC;                 /**< Interrupt Flag Clear Register  */
  __IOM uint32_t IEN;                 /**< Interrupt Enable Register  */
  __IOM uint32_t HFBUSCLKEN0;         /**< High Frequency Bus Clock Enable Register 0  */

  uint32_t       RESERVED11[3];       /**< Reserved for future use **/
  __IOM uint32_t HFPERCLKEN0;         /**< High Frequency Peripheral Clock Enable Register 0  */

  uint32_t       RESERVED12[7];       /**< Reserved for future use **/
  __IOM uint32_t LFACLKEN0;           /**< Low Frequency A Clock Enable Register 0  (Async Reg)  */
  uint32_t       RESERVED13[1];       /**< Reserved for future use **/
  __IOM uint32_t LFBCLKEN0;           /**< Low Frequency B Clock Enable Register 0 (Async Reg)  */

  uint32_t       RESERVED14[1];       /**< Reserved for future use **/
  __IOM uint32_t LFECLKEN0;           /**< Low Frequency E Clock Enable Register 0 (Async Reg)  */
  uint32_t       RESERVED15[3];       /**< Reserved for future use **/
  __IOM uint32_t HFPRESC;             /**< High Frequency Clock Prescaler Register  */

  uint32_t       RESERVED16[1];       /**< Reserved for future use **/
  __IOM uint32_t HFCOREPRESC;         /**< High Frequency Core Clock Prescaler Register  */
  __IOM uint32_t HFPERPRESC;          /**< High Frequency Peripheral Clock Prescaler Register  */

  uint32_t       RESERVED17[1];       /**< Reserved for future use **/
  __IOM uint32_t HFEXPPRESC;          /**< High Frequency Export Clock Prescaler Register  */

  uint32_t       RESERVED18[2];       /**< Reserved for future use **/
  __IOM uint32_t LFAPRESC0;           /**< Low Frequency A Prescaler Register 0 (Async Reg)  */
  uint32_t       RESERVED19[1];       /**< Reserved for future use **/
  __IOM uint32_t LFBPRESC0;           /**< Low Frequency B Prescaler Register 0  (Async Reg)  */
  uint32_t       RESERVED20[1];       /**< Reserved for future use **/
  __IOM uint32_t LFEPRESC0;           /**< Low Frequency E Prescaler Register 0  (Async Reg)  */

  uint32_t       RESERVED21[3];       /**< Reserved for future use **/
  __IM uint32_t  SYNCBUSY;            /**< Synchronization Busy Register  */
  __IOM uint32_t FREEZE;              /**< Freeze Register  */
  uint32_t       RESERVED22[2];       /**< Reserved for future use **/
  __IOM uint32_t PCNTCTRL;            /**< PCNT Control Register  */

  uint32_t       RESERVED23[2];       /**< Reserved for future use **/
  __IOM uint32_t ADCCTRL;             /**< ADC Control Register  */

  uint32_t       RESERVED24[4];       /**< Reserved for future use **/
  __IOM uint32_t ROUTEPEN;            /**< I/O Routing Pin Enable Register  */
  __IOM uint32_t ROUTELOC0;           /**< I/O Routing Location Register  */
  __IOM uint32_t ROUTELOC1;           /**< I/O Routing Location Register  */
  uint32_t       RESERVED25[1];       /**< Reserved for future use **/
  __IOM uint32_t LOCK;                /**< Configuration Lock Register  */
  __IOM uint32_t HFRCOSS;             /**< HFRCO Spread Spectrum Register  */
} CMU_TypeDef;                        /** @} */

/**************************************************************************//**
 * @addtogroup EFR32BG13P_CMU
 * @{
 * @defgroup EFR32BG13P_CMU_BitFields  CMU Bit Fields
 * @{
 *****************************************************************************/
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
