shsa5563/Ring-WearTech/Firmware/soc-smartPhone_NoBuff/inc/efr32bg13p_crypto.h

/**************************************************************************//**
 * @file efr32bg13p_crypto.h
 * @brief EFR32BG13P_CRYPTO register and bit field definitions
 * @version 5.3.2
 ******************************************************************************
 * # License
 * <b>Copyright 2017 Silicon Laboratories, Inc. http://www.silabs.com</b>
 ******************************************************************************
 *
 * Permission is granted to anyone to use this software for any purpose,
 * including commercial applications, and to alter it and redistribute it
 * freely, subject to the following restrictions:
 *
 * 1. The origin of this software must not be misrepresented; you must not
 *    claim that you wrote the original software.@n
 * 2. Altered source versions must be plainly marked as such, and must not be
 *    misrepresented as being the original software.@n
 * 3. This notice may not be removed or altered from any source distribution.
 *
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
 * Silicon Laboratories, Inc. will not be liable for any consequential,
 * incidental, or special damages, or any other relief, or for any claim by
 * any third party, arising from your use of this Software.
 *
 *****************************************************************************/

#if defined(__ICCARM__)
#pragma system_include       /* Treat file as system include file. */
#elif defined(__ARMCC_VERSION) && (__ARMCC_VERSION >= 6010050)
#pragma clang system_header  /* Treat file as system include file. */
#endif

/**************************************************************************//**
* @addtogroup Parts
* @{
******************************************************************************/
/**************************************************************************//**
 * @defgroup EFR32BG13P_CRYPTO CRYPTO
 * @{
 * @brief EFR32BG13P_CRYPTO Register Declaration
 *****************************************************************************/
/** CRYPTO Register Declaration */
typedef struct {
  __IOM uint32_t CTRL;           /**< Control Register  */
  __IOM uint32_t WAC;            /**< Wide Arithmetic Configuration  */
  __IOM uint32_t CMD;            /**< Command Register  */
  uint32_t       RESERVED0[1];   /**< Reserved for future use **/
  __IM uint32_t  STATUS;         /**< Status Register  */
  __IM uint32_t  DSTATUS;        /**< Data Status Register  */
  __IM uint32_t  CSTATUS;        /**< Control Status Register  */
  uint32_t       RESERVED1[1];   /**< Reserved for future use **/
  __IOM uint32_t KEY;            /**< KEY Register Access  */
  __IOM uint32_t KEYBUF;         /**< KEY Buffer Register Access  */
  uint32_t       RESERVED2[2];   /**< Reserved for future use **/
  __IOM uint32_t SEQCTRL;        /**< Sequence Control  */
  __IOM uint32_t SEQCTRLB;       /**< Sequence Control B  */
  uint32_t       RESERVED3[2];   /**< Reserved for future use **/
  __IM uint32_t  IF;             /**< AES Interrupt Flags  */
  __IOM uint32_t IFS;            /**< Interrupt Flag Set Register  */
  __IOM uint32_t IFC;            /**< Interrupt Flag Clear Register  */
  __IOM uint32_t IEN;            /**< Interrupt Enable Register  */
  __IOM uint32_t SEQ0;           /**< Sequence register 0  */
  __IOM uint32_t SEQ1;           /**< Sequence Register 1  */
  __IOM uint32_t SEQ2;           /**< Sequence Register 2  */
  __IOM uint32_t SEQ3;           /**< Sequence Register 3  */
  __IOM uint32_t SEQ4;           /**< Sequence Register 4  */
  uint32_t       RESERVED4[7];   /**< Reserved for future use **/
  __IOM uint32_t DATA0;          /**< DATA0 Register Access  */
  __IOM uint32_t DATA1;          /**< DATA1 Register Access  */
  __IOM uint32_t DATA2;          /**< DATA2 Register Access  */
  __IOM uint32_t DATA3;          /**< DATA3 Register Access  */
  uint32_t       RESERVED5[4];   /**< Reserved for future use **/
  __IOM uint32_t DATA0XOR;       /**< DATA0XOR Register Access  */
  uint32_t       RESERVED6[3];   /**< Reserved for future use **/
  __IOM uint32_t DATA0BYTE;      /**< DATA0 Register Byte Access  */
  __IOM uint32_t DATA1BYTE;      /**< DATA1 Register Byte Access  */
  uint32_t       RESERVED7[1];   /**< Reserved for future use **/
  __IOM uint32_t DATA0XORBYTE;   /**< DATA0 Register Byte XOR Access  */
  __IOM uint32_t DATA0BYTE12;    /**< DATA0 Register Byte 12 Access  */
  __IOM uint32_t DATA0BYTE13;    /**< DATA0 Register Byte 13 Access  */
  __IOM uint32_t DATA0BYTE14;    /**< DATA0 Register Byte 14 Access  */
  __IOM uint32_t DATA0BYTE15;    /**< DATA0 Register Byte 15 Access  */
  uint32_t       RESERVED8[12];  /**< Reserved for future use **/
  __IOM uint32_t DDATA0;         /**< DDATA0 Register Access  */
  __IOM uint32_t DDATA1;         /**< DDATA1 Register Access  */
  __IOM uint32_t DDATA2;         /**< DDATA2 Register Access  */
  __IOM uint32_t DDATA3;         /**< DDATA3 Register Access  */
  __IOM uint32_t DDATA4;         /**< DDATA4 Register Access  */
  uint32_t       RESERVED9[7];   /**< Reserved for future use **/
  __IOM uint32_t DDATA0BIG;      /**< DDATA0 Register Big Endian Access  */
  uint32_t       RESERVED10[3];  /**< Reserved for future use **/
  __IOM uint32_t DDATA0BYTE;     /**< DDATA0 Register Byte Access  */
  __IOM uint32_t DDATA1BYTE;     /**< DDATA1 Register Byte Access  */
  __IOM uint32_t DDATA0BYTE32;   /**< DDATA0 Register Byte 32 access.  */
  uint32_t       RESERVED11[13]; /**< Reserved for future use **/
  __IOM uint32_t QDATA0;         /**< QDATA0 Register Access  */
  __IOM uint32_t QDATA1;         /**< QDATA1 Register Access  */
  uint32_t       RESERVED12[7];  /**< Reserved for future use **/
  __IOM uint32_t QDATA1BIG;      /**< QDATA1 Register Big Endian Access  */
  uint32_t       RESERVED13[6];  /**< Reserved for future use **/
  __IOM uint32_t QDATA0BYTE;     /**< QDATA0 Register Byte Access  */
  __IOM uint32_t QDATA1BYTE;     /**< QDATA1 Register Byte Access  */
} CRYPTO_TypeDef;                /** @} */

/**************************************************************************//**
 * @addtogroup EFR32BG13P_CRYPTO
 * @{
 * @defgroup EFR32BG13P_CRYPTO_BitFields  CRYPTO Bit Fields
 * @{
 *****************************************************************************/
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
