shsa5563/Ring-WearTech/Firmware/soc-smartPhone_NoBuff/hardware/kit/common/drivers/display.c

/***************************************************************************//**
 * @file display.c
 * @brief Display interface.
 * @version 5.3.3
 *******************************************************************************
 * # License
 * <b>Copyright 2015 Silicon Labs, Inc. http://www.silabs.com</b>
 *******************************************************************************
 *
 * This file is licensed under the Silabs License Agreement. See the file
 * "Silabs_License_Agreement.txt" for details. Before using this software for
 * any purpose, you must agree to the terms of that agreement.
 *
 ******************************************************************************/

#include <stdint.h>
#include <stdbool.h>
#include <string.h>

#include "displayconfigall.h"
#include "display.h"
#include "displaybackend.h"

/** @cond DO_NOT_INCLUDE_WITH_DOXYGEN */

/*******************************************************************************
 ********************************  STATICS  ************************************
 ******************************************************************************/

/* Table of display devices. */
static DISPLAY_Device_t deviceTable[DISPLAY_DEVICES_MAX];

/* This variable keeps track of whether the DISPLAY module is initialized
   or not. */
static bool moduleInitialized = false;

/* This variable keeps track of the number of devices that have been
    registered. */
static int devicesRegistered = 0;
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
